teusH/MySense/docs/ssd1306.md

# Adafruit tiny display SSD1306
The Adafruit display

has SPI (7 wires) or I2C bus (4 wires) connector.
The SPI version will not cooperate with Grove Pi Shield!

## references
* https://raspberrytips.nl/oled-display-spi-raspberry-pi/
* https://media.readthedocs.org/pdf/ssd1306/stable/ssd1306.pdf

## hardware SPI installation
Wiring:
```
Raspberry Pi    color   OLED Module
5V   (PIN #1)   red     VDD (VIN)       PIN1 is V3.3
GND  (PIN #6)   black   GND
GPIO23 (PIN #16)        green   DC
GPIO24 (PIN #18)        blew    RES (RST)
MOSI (PIN #19)  purple  SDA (DATA)
SCLK (PIN #23)  orange  SCK (CLK)
CE0  (PIN #24)  yellow  CS
```
## Pi configuration
Use `ls -l /dev/spidev*`: /dev/spidev0.0  /dev/spidev0.1 to see if SPI is enabled.
If not existant enable SPI in the raspberry Pi config tool:
```shell
sudo raspi-config
```
* ‘Advanced Options' ▸ SPI ▸ YES and push Enter. 
Use `ls -l /dev/i2c-*` to see if I2C is enabled.
If not enable I2C via raspi-config.
The Pi might show I2C write errors. MySense display server will terminate if there are too many write errors. It is a known hardware bug in the Pi3 I2C driver.

## dependences installation
Use `INSTALL.sh DISPLAY` to install them or manually:
```shell
sudo apt-get install build-essential python-dev python-pip
sudo pip install RPi.GPIO

sudo apt-get install python-imaging python-smbus

sudo apt-get install git
git clone https://github.com/adafruit/Adafruit_Python_SSD1306.git
cd Adafruit_Python_SSD1306; sudo python setup.py install
```

## test hardware and software
SSD1306-test.py:
```python
import Adafruit_GPIO.SPI as SPI
import Adafruit_SSD1306

from PIL import Image
from PIL import ImageDraw
from PIL import ImageFont

disp = Adafruit_SSD1306.SSD1306_128_64(rst=24, dc=23, spi=SPI.SpiDev(0, 0, max_speed_hz=8000000))

disp.begin()
disp.clear()
disp.display()

image = Image.new('1', (disp.width, disp.height))

draw = ImageDraw.Draw(image)
draw.rectangle((0,0,disp.width-1,disp.height-1), outline=1, fill=0)

font = ImageFont.load_default()
draw.text((16, 24),'RASPBERRYTIPS.NL',  font=font, fill=255)

disp.image(image)
disp.display()
```

Voorbeeld:
import time
import sys
import subprocess

import Adafruit_GPIO.SPI as SPI
import Adafruit_SSD1306

from PIL import Image
from PIL import ImageDraw
from PIL import ImageFont

from time import sleep
```
## display service
Run `python MyDisplayServer.py start` to start the display service. The service uses localjost/2017 socket address to collect lines. Lines of text can be preceeded with the following xml:
* <clear> clear display immediatly
* <text font=FONT_NAME size=8> to get a line in some ttf font as defined in `/usr/share/fonts/truetype/` directory.
The line will scroll every 0.1 sec if the line is wider as the width of the display.
The display will scroll every 30 seconds one line if there are more lines as to be fit as the height of the display.

## test
Use MyDisplayClient.py to send a line to the service, eg.
```shell
python MyDisplayClient.py "This is first" "This is second line and is long."
```

## Use output channel
Add to `MySense.conf` the section:
```
    [display]
    output = True
```
