teusH/MySense/reports/Meetlokaties-Overzicht-2019-2026.pdf

# overzicht meetlocaties in enkele gemeenten

# onderzochte gemeentes met metingen en gebruikte sensoren 2019-2025

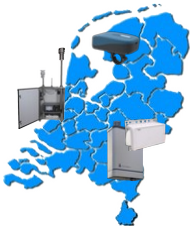
[picture p33: figure]

Teus Hagen, april 2026, MySense project.

gemeente | pagina
Amsterdam | 4
Beverwijk | 5
Gouda | 6
Haarlem | 7
Heemskerk | 8
Horst aan de Maas | 9
Hollandse Luchten | 10
Land van Cuijk | 11
Leidschendam-Voorburg | 12
Leusden | 13
Nijmegen | 14
Peel en Maas | 16
Velsen | 17
Venray | 18
Zaanstad | 19
informatie over de de metingen | 2
mogelijke conclusies en uitnodiging daartoe | 3

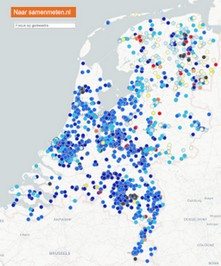
[picture p34: figure]

### - Voor een aantal gemeentes worden de low-cost meetstations van enkele gemeentes

aangegeven operationeel per jaar van 2019 t/m 2025.
- Meetstations, operationeel gehouden door diverse projecten en burger initiatieven,

### gebruikmakend van diverse fijnstof sensoren. Alleen PM2.5 metingen zijn meegenomen

in dit onderzoek.

### - De informatie is vergaard via Samen Meten Dataportaal API (april 2026) met

Samen Meten Tools. (https://github.com/teusH/MySense/blob/master/SamenMetenTools/README.md)

### - De om de interactieve kaartjes te downloaden als HTML bestand kan geclickt worden op de kaartjes bij elk overzicht. Het HTML bestand kan dan vervolgens via de browser

ingezien worden. De kaarten zijn van OpenStreetMap en Leaflet.

### - De icon’s en vlaggetjes van enkele regio’s zijn puur bedoeld als indicatie van een gemeente of regio. De gemeente vlaggetjes waaien soms alle kanten op. Wapperen bij

de één harder als bij de ander.

### - De analyse van het getoonde (spreadsheet) cijfermateriaal wordt overgelaten aan de

lezer. Er zijn meer mogelijkheden als dan hier getoond wordt.

### - Dit overview is met behulp van een spreadsheet (ODS formaat), zie

https://github.com/teusH/MySense/SamenMetenTools (https://github.com/teusH/MySense/blob/master/SamenMetenTools/SLA-cases-Overzicht-Meetpunten.ods) voor de data bron.

# overzicht meetlocaties in enkele gemeentes

# Samen Meten Dataportaal

# meetlocaties met metingen en gebruikte sensoren 2019-2025

Teus Hagen, april 2026, MySense project.

naar Samen Meten Dataportaal (https://samenmeten.rivm.nl/dataportaal/)

- Voor meer conclusies en mogelijkheden tot conclusie wordt verwezen naar de spreadsheet. (https://github.com/teusH/MySense/blob/master/SamenMetenTools/SLA-cases-Overzicht-Meetpunten.ods) Zie https://github.com/teusH/MySense/SamenMetenTools.
- De overzichten geven niet weer wat het meten heeft opgeleverd en bijgedragen aan beleidsmaatregelen.
- Maak gebruik van de interactieve browser kaartjes door downloaden van de pagina en te visualiseren in de browser.
- Ontwikkeling in kwaliteit en mogelijkheden van de fijnstof sensoren: van Shiney, naar Nova en Sensirion en recentelijk Bosch. Van WiFi naar IoT mobiel netwerk.
- Pas op er zijn groeperingen (clustering) van meetstations op minder dan 100 meter van elkaar. Ze hangen niet altijd op de meest gunstige plek.
- Er is onduidelijkheid tav de duurzaamheid van low-cost meetstations en meetprojecten en aantal metingen.
- Het aantal operationele meetstation bereikte, op maar een paar na, in 2023 het hoogtepunt.
- De uitdaging van dit document is om meer conclusies te trekken en de gegevens uit te breiden naar behoefte.
- De software is vrij te gebruiken en uit te breiden onder reciprocal licentie voorwaarden: EUPL (European Union Public Licence).
- Disclaimer: dit overzicht is met zorg samengesteld. De hoeveelheid gegevens is enorm. Verbeteringen worden op prijs gesteld.

# overzicht meetlocaties in enkele gemeentes

# Samen Meten Dataportaal

# voorzichtige conclusies en uitnodiging tot meer conclusies

Teus Hagen, april 2026, MySense project.
- Voor meer conclusies en mogelijkheden tot conclusie wordt verwezen naar de spreadsheet. (https://github.com/teusH/MySense/blob/master/SamenMetenTools/SLA-cases-Overzicht-Meetpunten.ods)

# overzicht meetlocaties Samen Meten Amsterdam

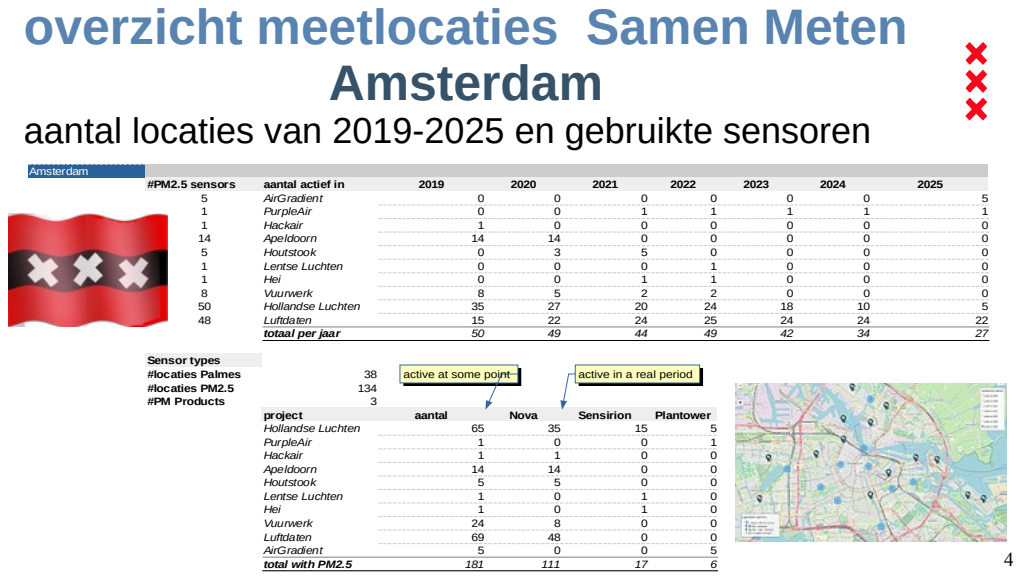
[picture p35: page 4]
Amsterdam; #PM2.5 sensors; aantal actief in; AirGradient; PurpleAir; Hackair; Apeldoorn; Houtstook; Lentse Luchten; Hei; Vuurwerk; Hollandse Luchten; Luftdaten; totaal per jaar; Sensor types; #locaties Palmes; #locaties PM2.5; #PM Products; Nova; project; aantal; Sensirion; Plantower; total with PM2.5; active at some point; active in a real period

aantal locaties van 2019-2025 en gebruikte sensoren

# overzicht meetlocaties Samen Meten Beverwijk

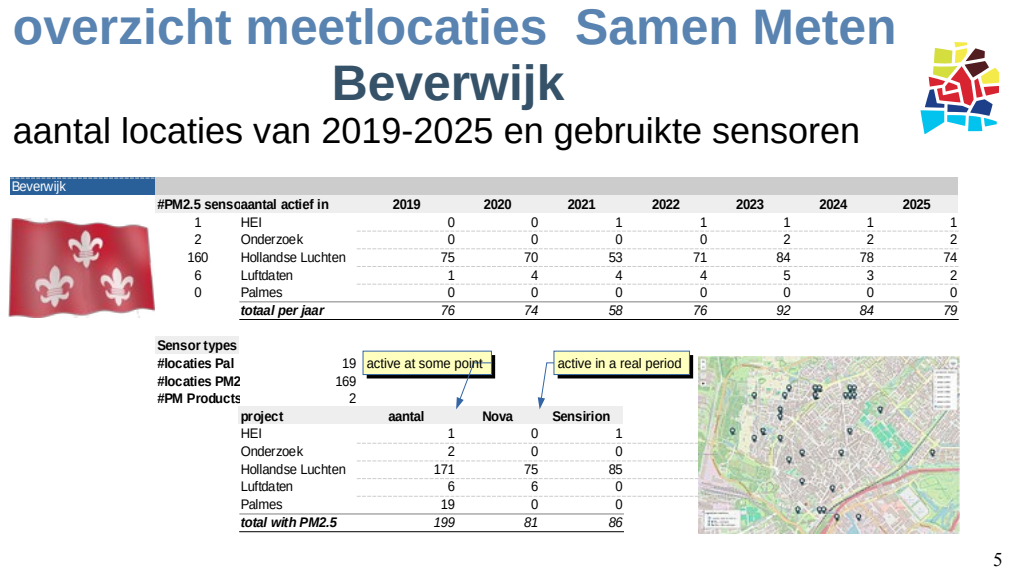
[picture p36: page 5]
Beverwijk; #PM2.5 sensoaantal actief in; HEI; Onderzoek; Hollandse Luchten; Luftdaten; Palmes; totaal per jaar; Sensor types; #locaties Pal; #locaties PM2; #PM Products; Nova; project; aantal; Sensirion; Sensirion HEI; Plantower Onderzoek; Shiney; total with PM2.5; active at some point; active in a real period

aantal locaties van 2019-2025 en gebruikte sensoren

# overzicht meetlocaties Samen Meten Gouda

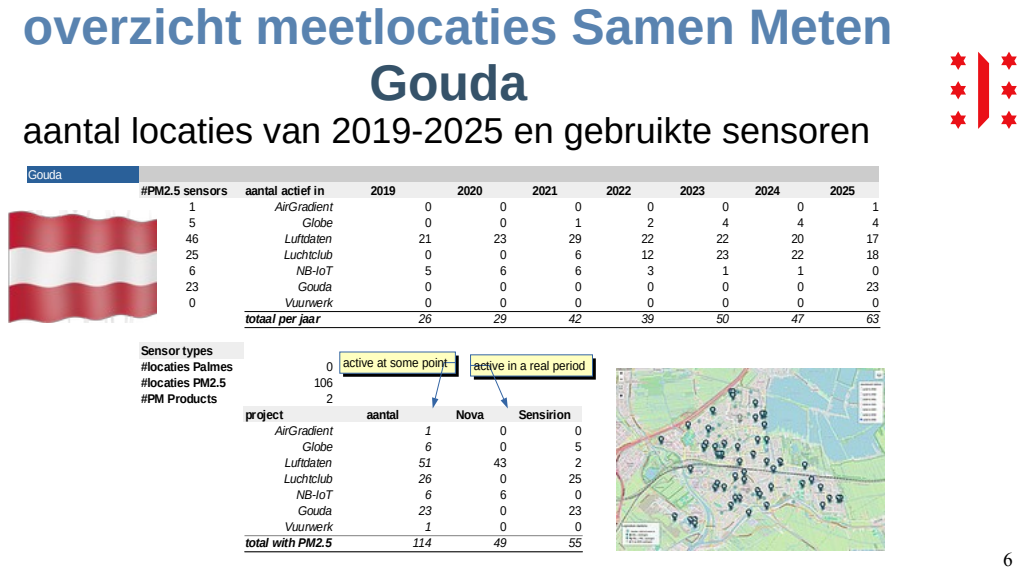
[picture p37: page 6]
Gouda; #PM2.5 sensors; aantal actief in; AirGradient; Globe; Luftdaten; Luchtclub; NB-IoT; Vuurwerk; totaal per jaar; Sensor types; #locaties Palmes; #locaties PM2.5; #PM Products; Nova; project; aantal; Sensirion; total with PM2.5; active at some point; active in a real period

aantal locaties van 2019-2025 en gebruikte sensoren

# overzicht meetlocaties Samen Meten Haarlem

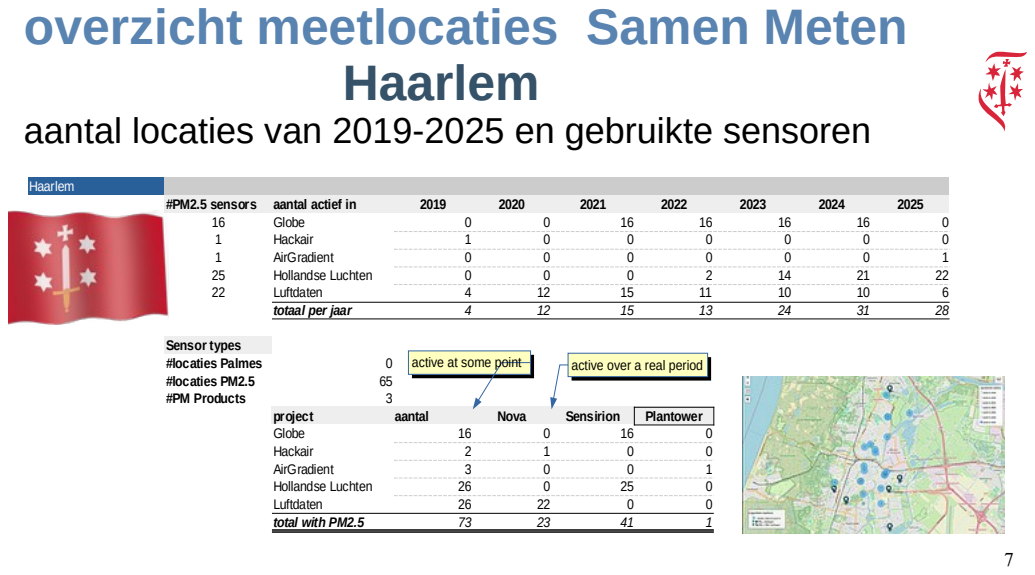
[picture p38: page 7]
Haarlem; #PM2.5 sensors aantal actief in; Globe; Hackair; AirGradient; Hollandse Luchten; Luftdaten; totaal per jaar; Sensor types; #locaties Palmes; #locaties PM2.5; #PM Products; Nova; project; aantal; Sensirion; Plantower; Shiney; total with PM2.5; active at some point; active over a real period

aantal locaties van 2019-2025 en gebruikte sensoren

# overzicht meetlocaties Samen Meten Heemskerk

# aantal locaties van 2019-2025 en gebruikte sensoren

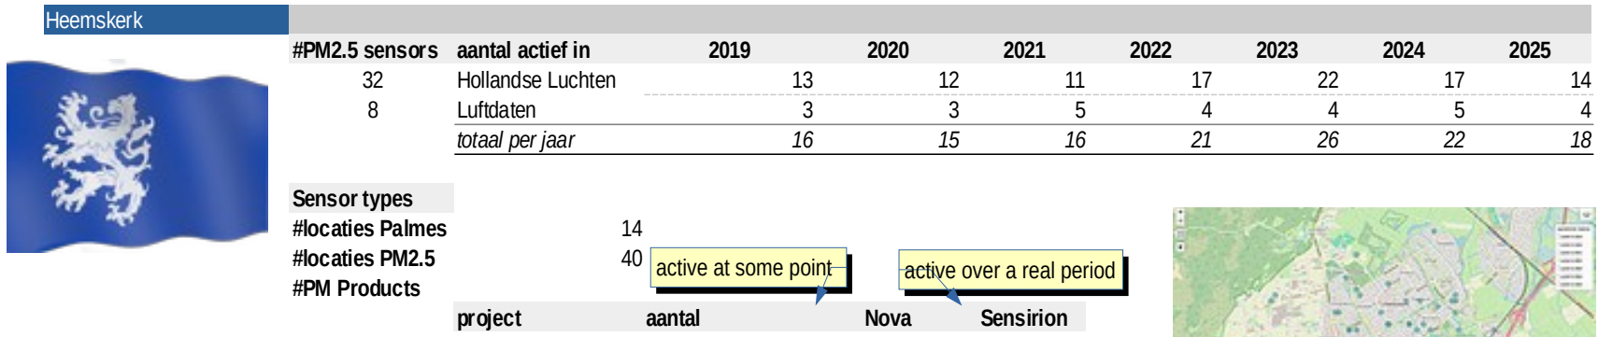
[picture p39: figure]
Heemskerk; #PM2.5 sensors aantal actief in; Hollandse Luchten; Luftdaten; totaal per jaar; Sensor types; #locaties Palmes; #locaties PM2.5; #PM Products; Nova; project; aantal; Sensirion; active at some point; active over a real period
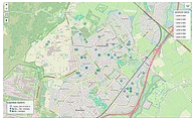
[picture p40: figure]

Sensirion | Hollandse Luchten | 32 | 13 | 19
Plantower | Luftdaten | 9 | 8 | 0
Shiney | total with PM2.5 | 41 | 21 | 19

# overzicht meetlocaties Samen Meten Horst aan de Maas

# aantal locaties van 2019-2025 en gebruikte sensoren

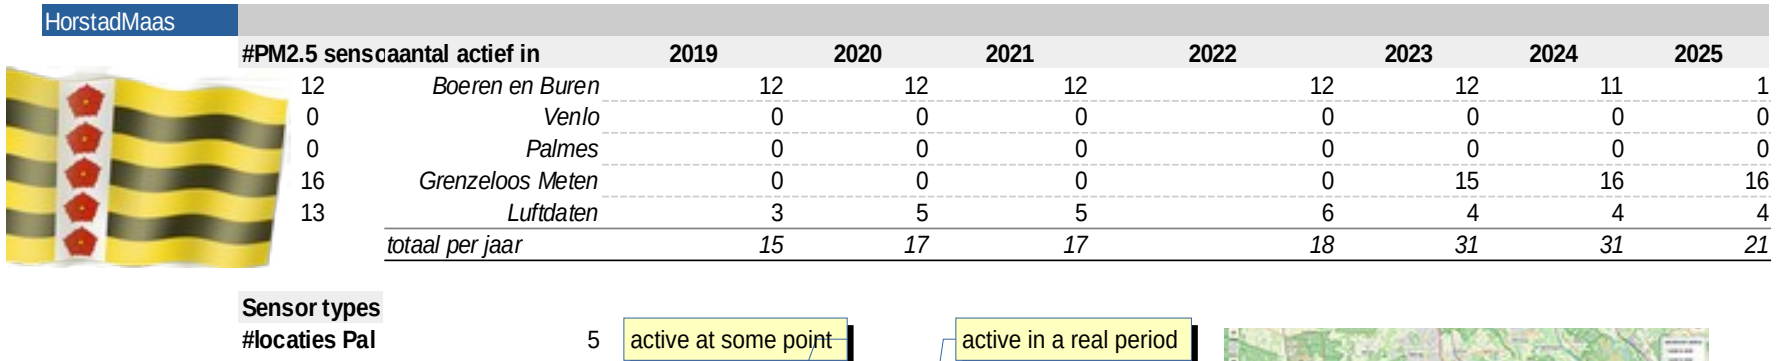
[picture p41: figure]
HorstadMaas; #PM2.5 sensoaantal actief in; Boeren en Buren; Venlo; Palmes; Grenzeloos Meten; Luftdaten; totaal per jaar; Sensor types; #locaties Pal; active at some point; active in a real period
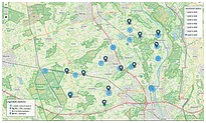
[picture p42: figure]

#locaties PM2 | 41

#PM Products | 2

Nova | project | aantal | Nova | Sensirion
Sensirion | Boeren en Buren | 12 | 12 | 0
| Venlo | 3 | 0 | 0
| Palmes | 5 | 0 | 0
| Grenzeloos Meten | 16 | 0 | 16
| Luftdaten | 19 | 13 | 0
| total with PM2.5 | 55 | 25 | 16

# overzicht meetlocaties Samen Meten Hollandse Luchten

# aantal locaties van 2019-2025 en gebruikte sensoren

Ijmond
#PM2.5 sensors | aantal actief in | 2019 | 2020 | 2021 | 2022 | 2023 | 2024 | 2025

Beverwijk | | 76 | 74 | 58 | 76 | 92 | 84 | 79
Haarlem | | 4 | 12 | 15 | 13 | 24 | 31 | 28
Heemskerk | | 16 | 15 | 16 | 21 | 26 | 22 | 18
Velsen | | 41 | 41 | 39 | 35 | 23 | 27 | 25
Amsterdam | | 50 | 49 | 44 | 49 | 42 | 34 | 27
Zaanstad | | 25 | 28 | 28 | 34 | 30 | 32 | 29
| totaal per jaar | 187 | 191 | 172 | 194 | 207 | 198 | 177

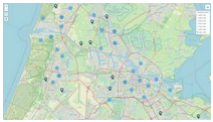
[picture p43: figure]

Sensor types | actief | Nova | Sensirion | Plantower
| Beverwijk | 81 | 86
| Haarlem | 23 | 41 | 1
| Heemskerk | 41 | 21 | 19
| Velsen | 47 | 23 | 1
| Amsterdam | 111 | 17 | 6
| Zaanstad | 1 | 31 | 33
| totaal met PM2.5 | 303 | 188 | 27

# overzicht meetlocaties Samen Meten Land van Cuijk

# aantal locaties van 2019-2025 en gebruikte sensoren

LandvCuijk
#PM2.5 sensors | aantal actief in | 2019 | 2020 | 2021 | 2022 | 2023 | 2024 | 2025

2 | AirGradient | 0 | 0 | 0 | 0 | 0 | 0 | 2
0 | Palmes | 0 | 0 | 0 | 0 | 0 | 0 | 0
1 | Hollandse Luchten | 0 | 0 | 0 | 1 | 1 | 1 | 0
89 | Luftdaten | 24 | 34 | 46 | 29 | 24 | 24 | 21
| totaal per jaar | 24 | 34 | 46 | 30 | 25 | 25 | 23

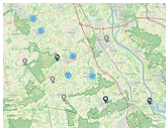
[picture p44: figure]

Sensor types
#locaties Palmes | 13

#locaties PM2.5 | 92

#PM Products | 3

Nova | project | aantal | Nova | Sensirion | Plantower
Sensirion | AirGradient | 2 | 0 | 0 | 2
Plantower | Palmes | 13 | 0 | 0 | 0
Shiney | Hollandse Luchten | 1 | 0 | 1 | 0
| Luftdaten | 97 | 87 | 1 | 1
| total with PM2.5 | 113 | 87 | 2 | 3
active at some point | active in a real period

# overzicht meetlocaties Samen Meten Leidschendam-Voorburg

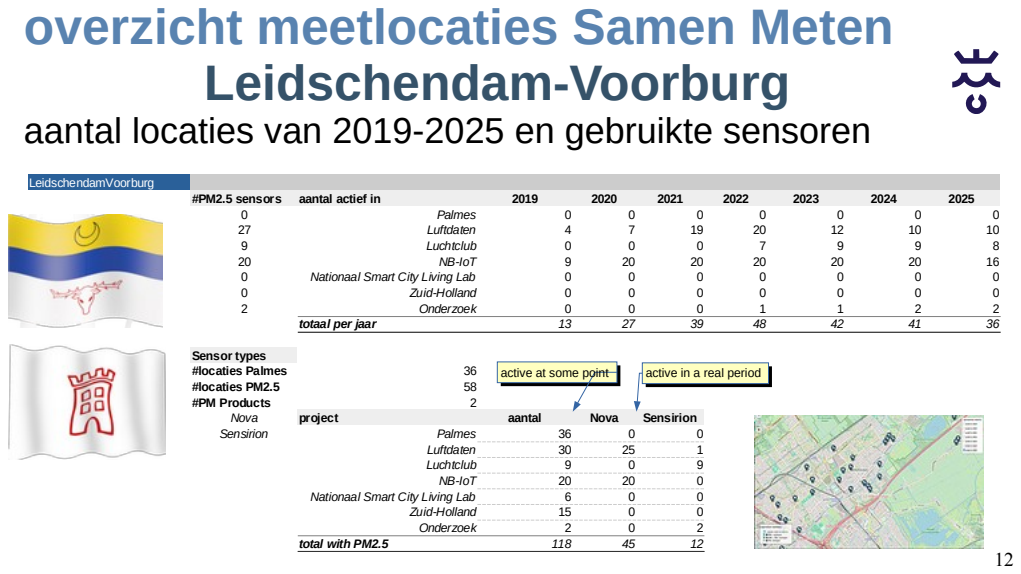
[picture p45: page 12]
LeidschendamVoorburg; #PM2.5 sensors; aantal actief in; Palmes; Luftdaten; Luchtclub; NB-IoT; Nationaal Smart City Living Lab; Zuid-Holland; Onderzoek; totaal per jaar; Sensor types; #locaties Palmes; #locaties PM2.5; #PM Products; Nova; project; aantal; Sensirion; total with PM2.5; active at some point; active in a real period

aantal locaties van 2019-2025 en gebruikte sensoren

# overzicht meetlocaties Samen Meten Leusden

# aantal locaties van 2019-2025 en gebruikte sensoren

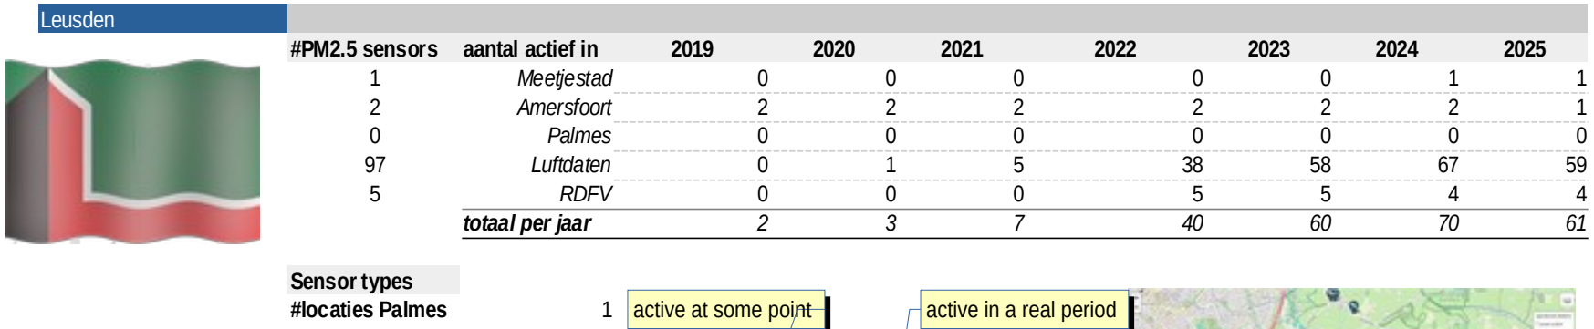
[picture p46: figure]
Leusden; #PM2.5 sensors aantal actief in; Meetjestad; Amersfoort; Palmes; Luftdaten; RDFV; totaal per jaar; Sensor types; #locaties Palmes; active at some point; active in a real period
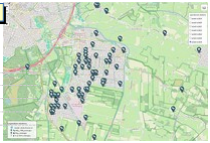
[picture p47: figure]

#locaties PM2.5 | 100

#PM Products | 2

project | aantal | Nova | Sensirion
Meetjestad | 1 | 0 | 1
Amersfoort | 2 | 2 | 0
Palmes | 1 | 0 | 0
Luftdaten | 172 | 75 | 22
RDFV | 6 | 0 | 5
total with PM2.5 | 182 | 77 | 28

# overzicht meetlocaties Samen Meten Nijmegen (1)

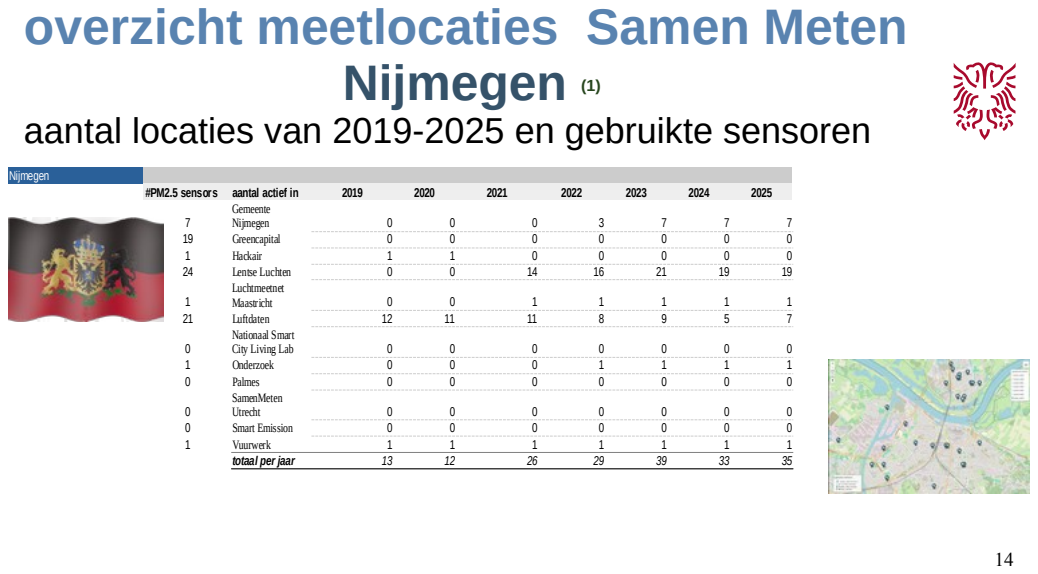
[picture p48: page 14]
Nijmegen; #PM2.5 sensors aantal actief in; Greencapital; Hackair; Lentse Luchten; Luftdaten; Onderzoek; Palmes; Smart Emission; Vuurwerk; totaal per jaar; Gemeente Nijmegen; Luchtmeetnet Maastricht; SamenMeten Utrecht

aantal locaties van 2019-2025 en gebruikte sensoren

Nationaal Smart
City Living Lab

# overzicht meetlocaties Samen Meten Nijmegen (2)

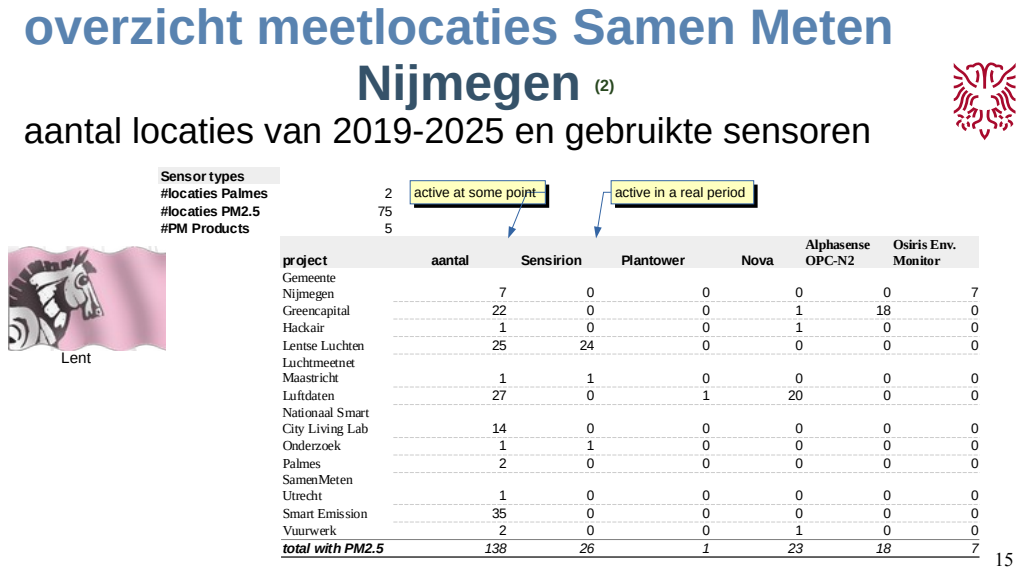
[picture p49: page 15]
Sensor types; #locaties Palmes; #locaties PM2.5; #PM Products; project; aantal; Sensirion; Plantower; Nova; Greencapital; Hackair; Lentse Luchten; Luftdaten; Onderzoek; Palmes; Smart Emission; Vuurwerk; total with PM2.5; Alphasense OPC-N2; Osiris Env. Monitor; Gemeente Nijmegen; Luchtmeetnet Maastricht; Nationaal Smart City Living Lab; SamenMeten Utrecht; active at some point; active in a real period; Lent

aantal locaties van 2019-2025 en gebruikte sensoren

# overzicht meetlocaties Samen Meten Peel en Maas

# aantal locaties van 2019-2025 en gebruikte sensoren

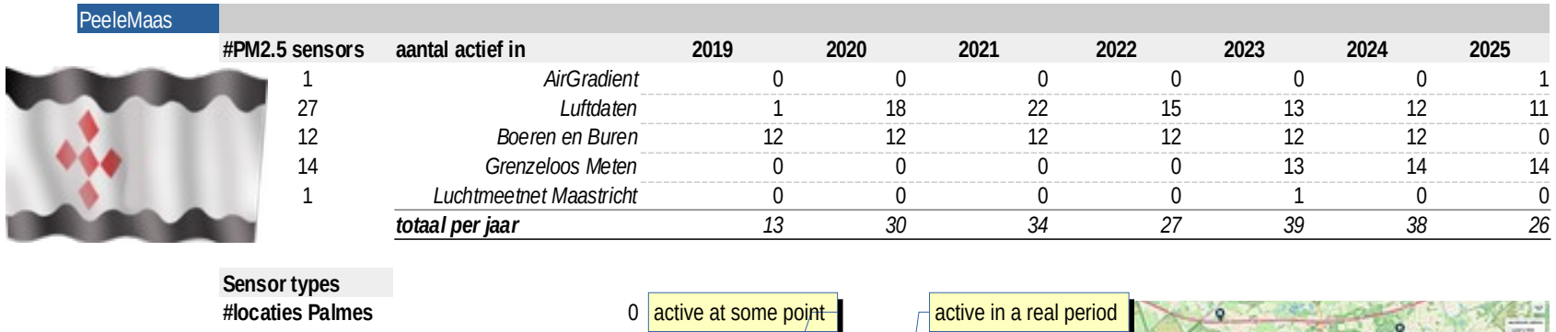
[picture p50: figure]
PeeleMaas; #PM2.5 sensors; aantal actief in; AirGradient; Luftdaten; Boeren en Buren; Grenzeloos Meten; Luchtmeetnet Maastricht; totaal per jaar; Sensor types; #locaties Palmes; active at some point; active in a real period
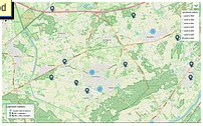
[picture p51: figure]

#locaties PM2.5 | 55

#PM Products | 2

Nova project | aantal | Nova | Sensirion
Sensirion | AirGradient | 1 | 0 | 0
Plantower | Luftdaten | 31 | 27 | 0
| Boeren en Buren | 12 | 12 | 0
| Grenzeloos Meten | 14 | 0 | 14
| Luchtmeetnet Maastricht | 1 | 0 | 1
total with PM2.5 | 59 | 39 | 15

# overzicht meetlocaties Samen Meten Velsen

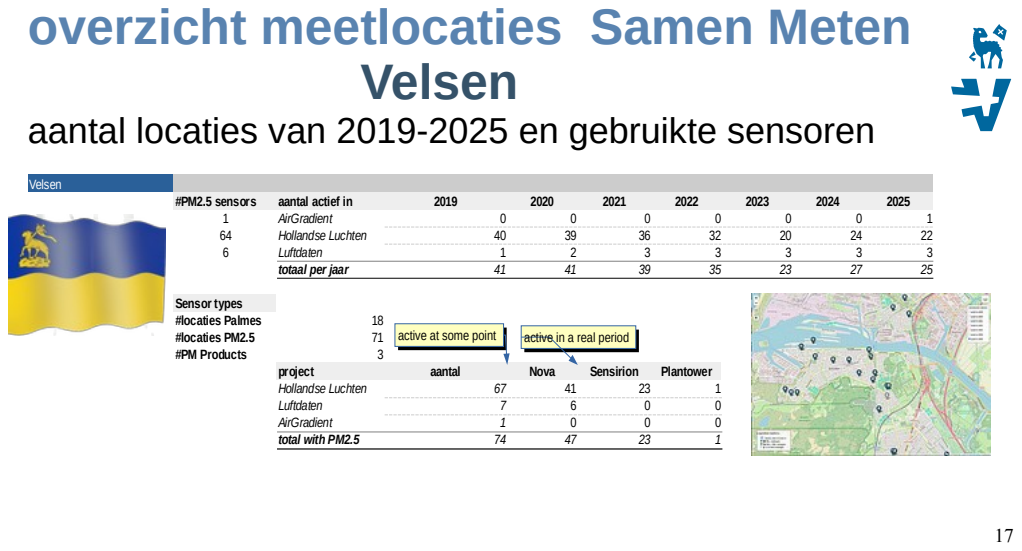
[picture p52: page 17]
Velsen; #PM2.5 sensors; aantal actief in; AirGradient; Hollandse Luchten; Luftdaten; totaal per jaar; Sensor types; #locaties Palmes; #locaties PM2.5; #PM Products; Nova; project; aantal; Sensirion; Plantower; total with PM2.5; active at some point; active in a real period

aantal locaties van 2019-2025 en gebruikte sensoren

# overzicht meetlocaties Samen Meten Venray

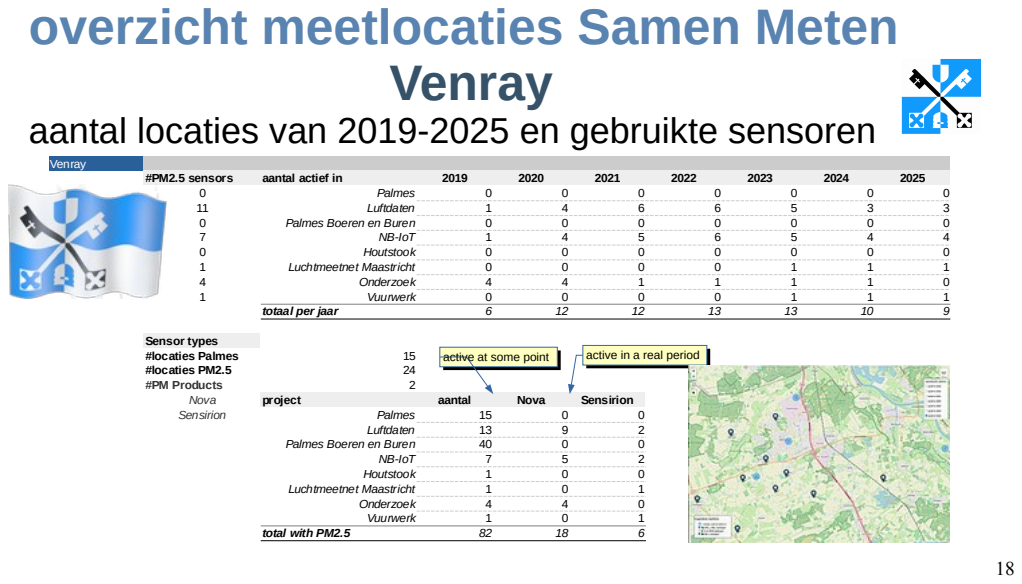
[picture p53: page 18]
Venray; #PM2.5 sensors; aantal actief in; Palmes; Luftdaten; Palmes Boeren en Buren; NB-IoT; Houtstook; Luchtmeetnet Maastricht; Onderzoek; Vuurwerk; totaal per jaar; Sensor types; #locaties Palmes; #locaties PM2.5; #PM Products; Nova; project; aantal; Sensirion; total with PM2.5; active at some point; active in a real period

aantal locaties van 2019-2025 en gebruikte sensoren

# overzicht meetlocaties Samen Meten Zaanstad

# aantal locaties van 2019-2025 en gebruikte sensoren

Zaanstad
#PM2.5 sensors aantal actief in | 2019 | 2020 | 2021 | 2022 | 2023 | 2024 | 2025

1 | AirGradient | 0 | 0 | 0 | 0 | 0 | 0 | 1
1 | Globe | 0 | 0 | 0 | 0 | 0 | 0 | 0
1 | HEI | 0 | 0 | 1 | 1 | 0 | 0 | 0
46 | Hollandse Luchten | 18 | 18 | 17 | 26 | 24 | 25 | 22
15 | Luftdaten | 7 | 10 | 10 | 7 | 5 | 6 | 5
1 | Onderzoek | 0 | 0 | 0 | 0 | 1 | 1 | 1
0 | Palmes | 0 | 0 | 0 | 0 | 0 | 0 | 0
| totaal per jaar | 25 | 28 | 28 | 34 | 30 | 32 | 29

Sensor types
#locaties Palmes | 55

#locaties PM2.5 | 65

#PM Products | 3

| project | aantal | Plantower | Sensirion | Nova
| AirGradient | 1 | 1 | 0 | 0
| Globe | 1 | 0 | 1 | 0
| HEI | 1 | 0 | 1 | 0
| Hollandse Luchten | 60 | 0 | 28 | 18
| Luftdaten | 20 | 0 | 0 | 15
| Onderzoek | 1 | 0 | 1 | 0
| Palmes | 55 | 0 | 0 | 0
| total with PM2.5 | 139 | 1 | 31 | 33
active at some point | active in a real period

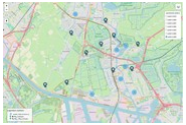
[picture p54: figure]
