teusH/MySense/reports/Scapeler Cases.pdf

## Over Scapeler

- Sensor Technologie
- Data Verzamelen, Verwerken, Analyseren, Modelleren en Visualiseren
- Maatschappelijke Waarde
- Dataportaal
- Empowerment
- Onafhankelijkheid

1

## Empowerment

Is het proces waarbij iemand gestimuleerd wordt zelfstandig te beslissen en te handelen en voor zichzelf op te komen. Dit gebeurt met methodieken die leiden tot het vergroten van het zelfvertrouwen, zelfbewustzijn en tot een positief zelfbeeld bij individuen, groepen of organisaties. Het doel van empowerment is iemand grip te laten krijgen op zijn of haar situatie en/of omgeving

2

05-04-2026

## Meetapparatuur

Drie standaard modellen:
1. ApriSensor-S:
PMSA003+DS18B20+BME280
2. ApriSensor-S-SPS30:
SPS30+DS18B20+BME680
3. ApriSensor-Duo:

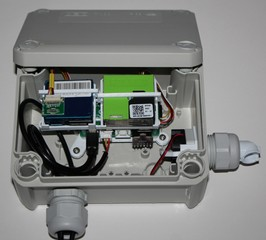
[picture p55: figure]

PMSA003+SPS30+DS18B20+BME680

3

## Wat meten we?

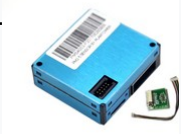
[picture p56: figure]

- Plantower PMSA003: Fijnstof PM+PN
- Sensirion SPS30: Fijnstof PM+PN
- Bosch BME280/BME680: T+RH+Pl
- Bosch BME680: T+RH+Pl (+VOC)

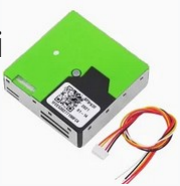
[picture p57: figure]

- Dallas DS18B20: T extern sensorkit
05-04-2026 | 4

## Dataportaal

- 135 sensor kits
- Nederland, België, Zwitserland en Japan
- Extra lagen:

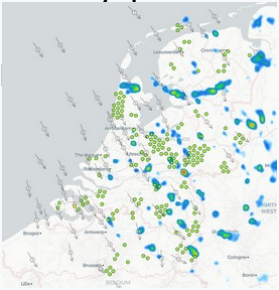
[picture p58: figure]

- Windrichting, windkracht (KNMI)
- Regen radar (KNMI)
- Luchtmeetnet
- CAMS
- Stookwijzer

5

## Case 1: Regionaal Meetnet Midden Limburg

- Meetperiode minimaal 3 jaar
- Regionaal Dataportaal
- Focus op schone lucht en gezondheid
- Houtrook

6

## Case 2: Hollandse Luchten

- HL op zoek naar alternatieve meetapparatuur
- Meetapparatuur in test opstelling
- 2x ApriSensor DUO + 2x ApriSensor-S
- Data verzamelen

7

## Case 3: Gemeente Rheden

- Sensor netwerk in gemeente Rheden
- Monitoren effect houtstookregels op luchtkwaliteit
- Meetlocaties bij burgers thuis en in openbare ruimten
- Meten in bebouwde kom en buitengebied
- Oriënterende fase met gemeente

8
