teusH/MySense/reports/SLA-Brandbrief-11mei2016.pdf

# SLA Brandbrief over de zin van:

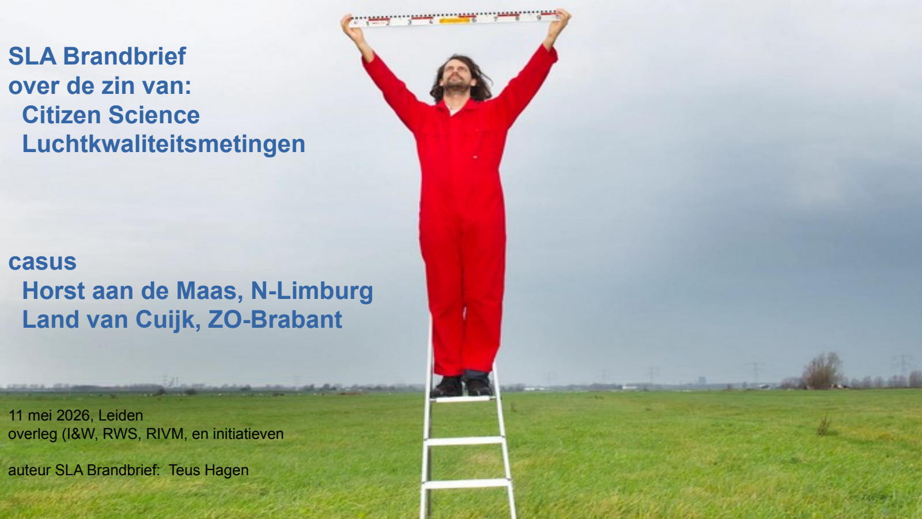
[picture p117: page 1]

# foto: Io Cooman, Volkskrant

# Citizen Science Luchtkwaliteitsmetingen

# casus Horst aan de Maas, N-Limburg Land van Cuijk, ZO-Brabant

## 11 mei 2026, Leiden overleg (I&W, RWS, RIVM, en initiatieven

## auteur SLA Brandbrief: Teus Hagen

Leiden, 11 mei 2026 - Teus Hagen | - SLA Brandbrief, casus Horst ad Maas, Land van Cuijk - | V1.1 | slide 2 van 15

# initiatief MySense

# Horst aan de Maas

⧫ | start ontwikkeling meetstations, data-com, data-analyse, website, rapportages
⧫ | 2018 start met interactieve real time overzichten, referentie metingen via LML
⧫ | doel: Terms of Reference: PM metingen rond melkvee-, varkens- en kippen-‘stallen’

⧫

# lokale beleidsvorming:

# constructieve en kwalitatieve inbreng, bewustwording, data analyse

# ⧫ 2025 einde: budgettering, demotivatie, uitblijven (lokale) dialoog met lokale overheid

# 2011 aanleg Landbouw Ontwikkelings-Gebied Grubbenvorst

referentie: CASUS Horst aan de Maas (https://github.com/teusH/MySense/blob/master/reports/202603-Casus-Horst%20aan%20de%20Maas.pdf)

Leiden, 11 mei 2026 - Teus Hagen | - SLA Brandbrief, casus Horst ad Maas, Land van Cuijk - | V1.1 | slide 3 van 15

# initiatief stichting BWLvC

# Land van Cuijk

⧫ | start lokale politiek, kosten bijdrage gem. St. Anthonis, MySense (fijnstof) meetstation, website,
| rapportages.
⧫ | 2019 start, onafhankelijke metingen, gekalibreerde metingen, verbetering meetstations
⧫ | doel: Terms of Reference: PM en NH3 metingen, meetfeiten rond emissies bronnen

⧫

# lokale beleidsvorming:

# constructieve en kwalitatieve inbreng, bewustwording, data analyse

⧫ | 2025 einde: einde budget, demotivatie, achterblijven (lokale) dialoog,
| einde gemeente St. Anthonis

# 2018 emissies bio-industrie: vleesvarkens, vlees- en legkippen

referentie: CASUS Land van Cuijk (https://github.com/teusH/MySense/blob/master/reports/202604-Casus-Land%20van%20Cuijk.pdf)

Leiden, 11 mei 2026 - Teus Hagen | - SLA Brandbrief, casus Horst ad Maas, Land van Cuijk - | V1.1 | slide 4 van 15

# wat en hoe nu gaan we nu samen verder ?

⧫ | doel luchtkwaliteitsmetingen en wat is er bereikt
⧫ | aanleiding tot schrijven van de brandbrief
⧫ | overwegingen en wederzijdse verwachtingen
⧫ | referentie materiaal (leesvoer voor thuis)

Leiden, 11 mei 2026 - Teus Hagen, Frans Kets, Walter Takens | - | Schone Lucht Akkoord Burger Participatie: het SLA glas is nu halfvol, en toen? - | V0.1 slide 5 van 15

# Citizen Science

en

# luchtkwaliteitsmetingen

# - doel:

λ

Inzicht te bieden in de luchtkwaliteit en de gezondheidseffecten daarvan, zich actief inzetten voor gezonde lucht in de gemeente, duiden en kwantificeren van effect van maatregelen door ondernemer en lokale overheid.

# - uitgangspunten:

λ | onafhankelijke, kwalitatief en goed geïnformeerde aanpak van meten en analyseren.
λ | proactieve communicatie naar en met belanghebbenden.
λ | een constructieve en op kennis gebaseerde inbreng ten opzichte van beleidskwesties in gemeente, provincie en rijk.

# - effectieve en informerende aanpak

# - bewustwording bij lokale overheid, ondernemer en burger

# - ontwikkeling van kwalitatieve low-cost meettechniek, data communicatie en opslag en data analyse

Leiden, 11 mei 2026 - Teus Hagen, Frans Kets, Walter Takens | - | Schone Lucht Akkoord Burger Participatie: het SLA glas is nu halfvol, en toen? - | V0.1 slide 6 van 15

# en ... de resultaten zijn best positief

# λ wetenschappelijk:

invloed weer en seizoen op luchtkwaliteit (wind, menglaag).
- vraagtekens: kalibratie, stabiliteit van metingen, afhankelijkheid van het weer.
- analyse software.
- ontwikkeling low-cost meettechniek, data management en data analyse.

# λ politiek:

# - bewustwording

λ | via inspreken Raad (fracties hebben het te druk).
λ | lokale nieuwsvoorzieningen

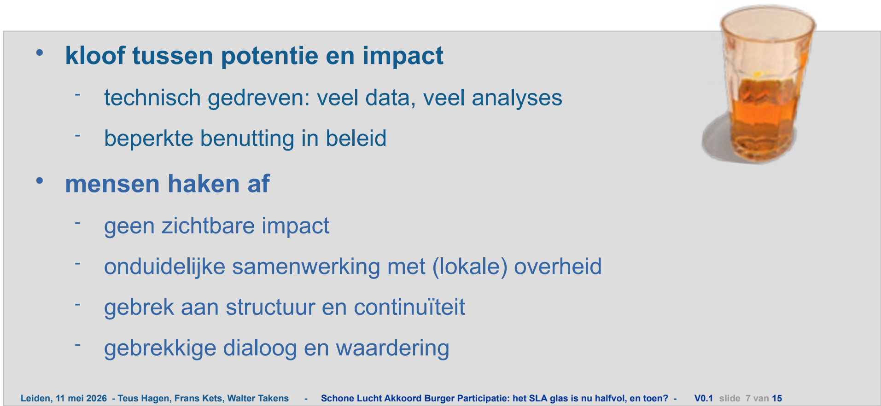
[picture p118: figure]
kloof tussen potentie en impact; - beperkte benutting in beleid; mensen haken af; - geen zichtbare impact; - gebrek aan structuur en continuïteit; - gebrekkige dialoog en waardering

Leiden, 11 mei 2026 - Teus Hagen, Frans Kets, Walter Takens | - | Schone Lucht Akkoord Burger Participatie: het SLA glas is nu halfvol, en toen? - | V0.1 slide 7 van 15
waarom? | de SLA Brandbrief

# technisch gedreven: veel data, veel analyses

# - onduidelijke samenwerking met (lokale) overheid

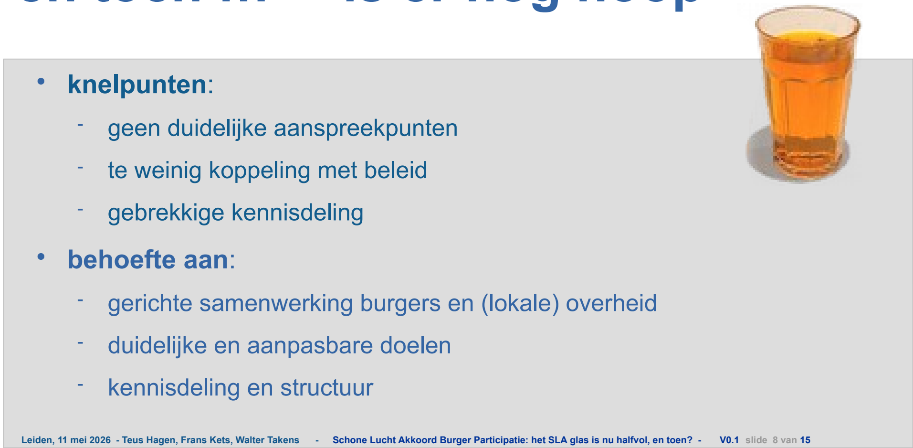
[picture p119: figure]
knelpunten:; - geen duidelijke aanspreekpunten; te weinig koppeling met beleid; - gebrekkige kennisdeling; behoefte aan:; - duidelijke en aanpasbare doelen; - kennisdeling en structuur

Leiden, 11 mei 2026 - Teus Hagen, Frans Kets, Walter Takens | - | Schone Lucht Akkoord Burger Participatie: het SLA glas is nu halfvol, en toen? - | V0.1 slide 8 van 15
en toch … | is er nog hoop

# - gerichte samenwerking burgers en (lokale) overheid

# de SLA Brandbrief

# 5 november 2025

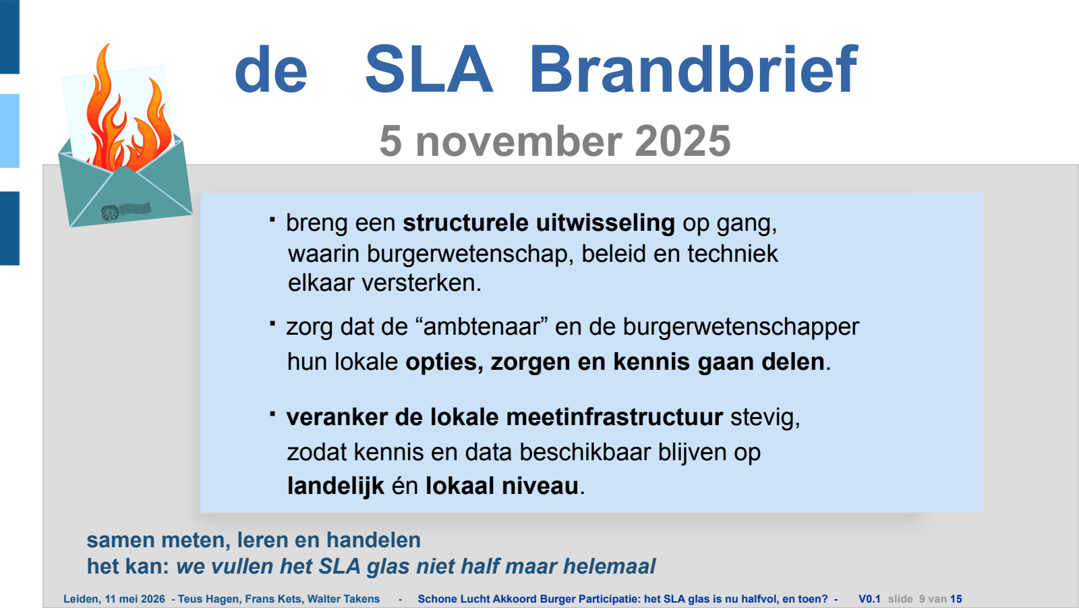
[picture p120: page 9]

Leiden, 11 mei 2026 - Teus Hagen, Frans Kets, Walter Takens | - | Schone Lucht Akkoord Burger Participatie: het SLA glas is nu halfvol, en toen? - | V0.1 slide 9 van 15
- breng een structurele uitwisseling op gang,

# waarin burgerwetenschap, beleid en techniek

elkaar versterken.

# - zorg dat de “ambtenaar” en de burgerwetenschapper

hun lokale opties, zorgen en kennis gaan delen.
- veranker de lokale meetinfrastructuur stevig,

# zodat kennis en data beschikbaar blijven op

landelijk én lokaal niveau.

# samen meten, leren en handelen het kan: we vullen het SLA glas niet half maar helemaal

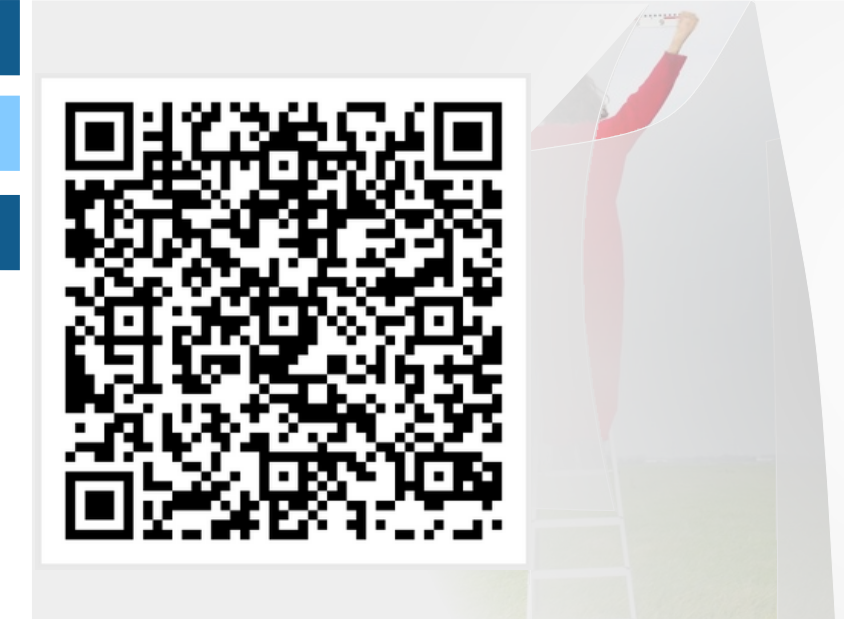
[picture p121: page 10]
Leiden, 11 mei 2026 - Teus Hagen, Frans Kets, Walter Takens; - naar photo: Io Cooman, Volkskrant; Schone Lucht Akkoord Burger Participatie: het SLA glas is nu halfvol, en toen? -; V0.1 slide 10 van 15

download:
github.com/teusH/MySense/reports/

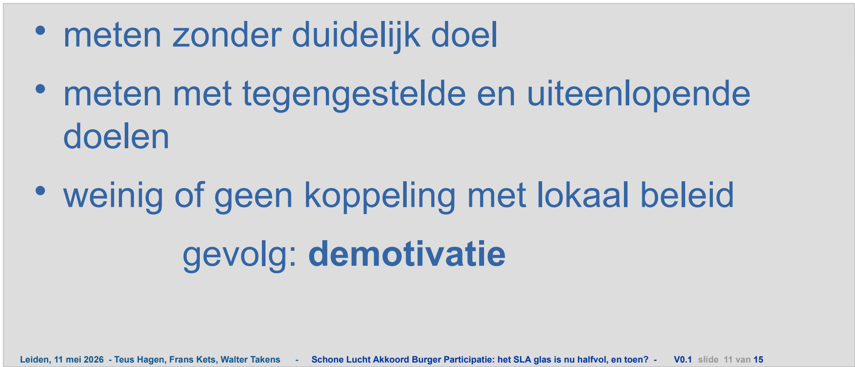
[picture p122: figure]
λ meten zonder duidelijk doel; doelen; gevolg: demotivatie

Leiden, 11 mei 2026 - Teus Hagen, Frans Kets, Walter Takens | - | Schone Lucht Akkoord Burger Participatie: het SLA glas is nu halfvol, en toen? - | V0.1 slide 11 van 15

# luchtkwaliteitsmetingen en doelgerichtheid

# λ meten met tegengestelde en uiteenlopende

# λ weinig of geen koppeling met lokaal beleid

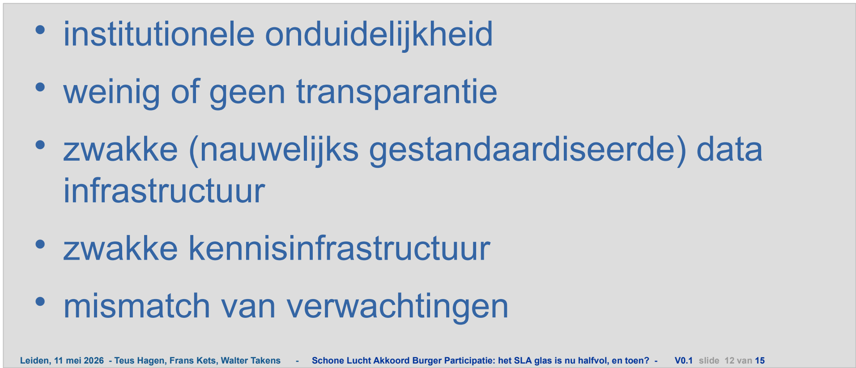
[picture p123: figure]
λ institutionele onduidelijkheid λ weinig of geen transparantie; infrastructuur λ zwakke kennisinfrastructuur λ mismatch van verwachtingen

Leiden, 11 mei 2026 - Teus Hagen, Frans Kets, Walter Takens | - | Schone Lucht Akkoord Burger Participatie: het SLA glas is nu halfvol, en toen? - | V0.1 slide 12 van 15

# de structurele problemen

# λ zwakke (nauwelijks gestandaardiseerde) data

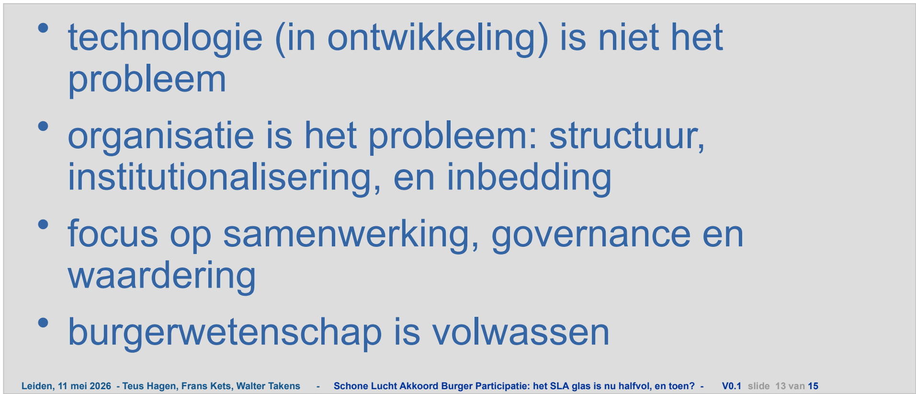
[picture p124: figure]
probleem; institutionalisering, en inbedding; focus op samenwerking, governance en waardering λ burgerwetenschap is volwassen

Leiden, 11 mei 2026 - Teus Hagen, Frans Kets, Walter Takens | - | Schone Lucht Akkoord Burger Participatie: het SLA glas is nu halfvol, en toen? - | V0.1 slide 13 van 15

# conclusie

# technologie (in ontwikkeling) is niet het

λ organisatie is het probleem: structuur,

Leiden, 11 mei 2026 - Teus Hagen, Frans Kets, Walter Takens | - | Schone Lucht Akkoord Burger Participatie: het SLA glas is nu halfvol, en toen? - | V0.1 slide 14 van 15

# leesvoer SLA Brandbrief

de vele details, een selectie | (o.a. https://github.com/teusH/MySense/)
λ | SLA Brandbrief (https://github.com/teusH/MySense/blob/master/reports/BrandBrief-SLA-V1.2.pdf) (open brief aan I&W, pdf, SLA Participatiedag 5 nov 2025)
λ | De digitale kloof overbruggen (https://waag.org/sites/waag/files/2026-03/De%20digitale%20kloof%20overbruggen.pdf) (onderzoeksrapport Waag Futurelab, pdf, maart 2026)
λ | Lokale Verbindingen (https://waag.org/sites/waag/files/2026-03/Lokale%20verbindingen.pdf) (gids voor ambtenaren, Waag Futurelab, pdf, maart 2026)
λ | SLA Participatie clarificatie document (https://github.com/teusH/MySense/blob/master/reports/ClarificatieBrandbrief260426.pdf) (achtergronds info, pdf, april 2026)
λ | Overzicht 15 gemeentes meetlokaties 2019-2025 (https://github.com/teusH/MySense/blob/master/reports/Meetlokaties-Overzicht-2019-2026.pdf) Noord- en Zuid-Holland, Brabant, Limburg (pdf, april 2026)
λ | Onderzoek 15 gemeentelijke meetlocaties en sensoren 2019-2025 (https://github.com/teusH/MySense/blob/master/reports/SLA-cases-Overzicht-Meetpunten.ods) (ODS spreadsheet, maart 2026)
λ | Cases en navelstaren:
- Casus Leidschendam-Voorburg (https://github.com/teusH/MySense/blob/master/reports/20260309-casus-Leidschendam-Voorburg.pdf) (Zuid Holland, pdf, febr 2026)
- Casus Horst ad Maas (https://github.com/teusH/MySense/blob/master/reports/202603-Casus-Horst%20aan%20de%20Maas.pdf) (Noord Limburg, pdf, maart 2026)
- Casus Land van Cuijk (https://github.com/teusH/MySense/blob/master/reports/202604-Casus-Land%20van%20Cuijk.pdf) (Zuid-Oost Brabant, pdf, maart 2026)
- Casus Scapeler (https://github.com/teusH/MySense/blob/master/reports/Scapeler%20Cases.pdf) (Houtstook metingen, pdf, april 2026)
λ Citizen Science: Citizen Sensing (https://waag.org/nl/citizen-sensing/) (Waag Futurelab webpagina, mei 2026)

Leiden, 11 mei 2026 - Teus Hagen, Frans Kets, Walter Takens | - | Schone Lucht Akkoord Burger Participatie: het SLA glas is nu halfvol, en toen? - | V0.1 slide 15 van 15

# leesvoer

de vele details, een selectie | (https://github.com/teusH/MySense/)
λ | Historisch overzicht luchtkwaliteit meten mbt lokale overheid (https://github.com/teusH/MySense/blob/master/reports/Tijdslijn%202011-2023%20luchtkwaliteitsmetingen%20Behoud%20de%20Parel%20_%20Behoud%20de%20Parel.pdf) (2011-2023,

# web pagina)

λ | 3 jaar meten in een agrarische omgeving (https://github.com/teusH/MySense/blob/master/reports/3JaarMetenInAgrRegioWatNu.pdf) (sept 2022, rapport)
λ | Luchtkwaliteit meten een leerschool (https://github.com/teusH/MySense/blob/master/reports/20230601-WAR-luchtkwaliteit-meten-leerschool-Teus-16X10-final.pdf) (juni 2023, Meetkoppel presentatie)
λ | Luchtkwaliteit meten: werkkader en organisatie structuur en ervaringen (https://github.com/teusH/MySense/blob/master/reports/Samen%20meten%20aan%20luchtkwaliteit%20_%20Behoud%20de%20Parel.pdf)

# (sept 2023, notitie)
