teusH/MySense/reports/ClarificatieBrandbrief260426.pdf

30 april 2026

## CLARIFICATIES T.A.V. SLA BRANDBRIEF

Introductie
Het gezamenlijke doel van beleid, bestuur en citizen science is een betere luchtkwaliteit in Nederland. Om dit te bereiken is een goede samenwerking noodzakelijk.
De intenties daartoe zijn er.

De brandbrief zoals gepresenteerd op de SLA Participatiedag op 5 november 2025 geeft uiting aan een aantal zorgen over de effectiviteit van deelname van burgerwetenschappers binnen het kader van het Schone Lucht Akkoord en geeft enkele knelpunten aan.
Alhoewel er zeker positieve kanten kunnen worden aangewezen, zien wij mogelijkheden tot verbetering.

Achtergrond: burgerwetenschappers zijn er in soorten en maten. Wij onderscheiden hier:
1. de innovator, geïnteresseerd in techniek en analysemethodes.
2. de milieuverbeteraar, gericht op invloed op bestuurlijke beslissingen en daarom als analist ook actief in het analyseren van metingen; Dit vertrouwt op metingen van “huisvesters”.
3. de huisvester, die het leuk vind om een metertje thuis te hebben.
4. de ondernemer, die de techniek omarmt en deze wil uitbaten.

Ruimte voor verbetering
We beschouwen de Burgerparticipatie issues zoals aangestipt in de SLA Brandbrief, hier nader:
- Er is een teruglopende interesse (bijv. minder stations, en problemen om opvolging voor lokale trekkers te vinden):
- t.a.v. de innovator: de technologie, die ten dienste staat van globale of lokale voorspellingen van luchtkwaliteit (de indicatoren PM2,5, PM10, NO2), is geëvolueerd en wordt volwassen. De innovatieve burgerwetenschapper kiest een andere uitdaging, minder in hardware ontwikkeling, meer in analyse, en soms in een ander veld.
- t.a.v. de milieuverbeteraar: er is een flinke zorg: de relatie burgerwetenschappers – bestuur / (lokale) ambtenaren:
- Burgerwetenschappers in luchtkwaliteit hebben serieuze tools en serieuze kennis verworven. Deze kunnen meer en beter worden benut dan nu het geval is.
- “Meten om alleen het meten” – zonder doel – draagt niets bij. Strakkere en doelgerichte samenwerking tussen politiek en meetgroep is nodig om projecten samen te definiëren / te effectueren.
- Het is onduidelijk hoe de overheid voor burgerinspraak is ingericht. Bijv. waar is het aanspreekpunt? Hoe effectueer je samenwerking? Hoe ga je om met het feit dat ambtenaren van baan wisselen en burgerwetenschappers er na een paar jaar mee ophouden?
- Een eerste eenvoudige stap ter verbetering: gezamenlijke SLA dag voor ambtenaren en burgerwetenschappers gericht op uitwisseling en actionele vooruitgang. Meer concrete verbeterstappen dienen partijen gezamenlijk te ontwikkelen.
- T.a.v. de huisvester:
- “Het nieuwtje is er van af”. De stekker gaat uit het stopcontact. Einde meting.
- Metingen zijn niet nuttig als een milieuverbeteraar en de overheidsinstanties (RIVM) er niets (zichtbaars) mee doen.
- Hoe lossen we dit op?
- Veranderingen van technologie – sensoren, data verwerking, analyse:
- Er is (dankzij o.a. de ondernemers”) een opmars van kant en klare sensoren.

SLA Brandbrief besprekingen april-mei 2026

30 april 2026

- Positief voor de ‘simpele’ kant van het werk van milieuverbeteraar en huisvester (er zijn data).
- Negatief voor de motivatie voor de innovator (waar is de uitdaging?) en analist (kwaliteitscontrole, publieke beschikbaarheid van meetresultaten).
- Knowledge management:
- Burgerwetenschappers zijn niet goed in het delen van methodes en verkopen van kennis. Resultaat – fragmentatie van kennis en duplicatie van werk. Kan het delen van methodes niet verder worden gestimuleerd? Hulp bieden door structuur te laten ontstaan? Uitdagingen aanbrengen?
- RIVM website en het Samen Meten Forum zijn niet voldoende voor een effectieve uitwisseling. Overheidsinstellingen kunnen zich daar ook laten zien.

Strategie vragen voor de toekomst
- Partijen: de vier klassen burgerparticipanten (al dan niet in verenigd verband), de lokale en provinciale overheden en diensten en de centrale overheid (ministerie). Met ieder zijn eigenaardigheden en eigen cultureel gedreven aanpak.
- Wat is het doel van het SLA en een SLA opvolger ten aanzien van het gebruik van burgerwetenschappers?
- Is er een beleidskader te schetsen voor de samenwerking tussen overheid en burgerwetenschap? Zo ja, voor welke type burgerwetenschapper?
- Komen de doelen van overheid en de verschillende soorten burgerwetenschappers overeen?
- Welke valkuilen en prioriteiten zijn er? Waar zitten de krenten in de pap? Hoe maken we de krenten smakelijk voor alle partijen? Het gaat om appreciatie voor de kostbare inbreng van alle partijen.

Teus Hagen, Frans Kets, Walter Takens, e.a.

SLA Brandbrief besprekingen april-mei 2026
