teusH/MySense/reports/20260309-casus-Leidschendam-Voorburg.pdf

# Navelstaren LV2 geschiedenis

# (Naar Mart de Kruif)

# λ Voorgeschiedenis λ Doel λ Middelen λ Mensen λ Resultaten λ Einde verhaal λ Wil

# Voorgeschiedenis

λ 2017

## - Aanleiding aanleg Rotterdamse Baan bij woonwijk

## λ Dec 2017

## - RIVM bijeenkomst

## - PZH stelt “paddenstoelen” beschikbaar (5 per gemeente)

## - Wij vragen om 10 (Leidschendam & Voorburg)

## λ Daarna pas (2018):

## - Organiseren distributie over gemeente

## - Maar twee in de buurt van de Rotterdamse Baan

## λ Eerste metingen:

## - Ontwikkelen van display methodes

# Doel

λ 2018 Definiëren van uitgangspunten en aanpak in Terms of Reference (één A4tje - Wie zijn wij?)

# - Doel:

λ

“door inzicht te bieden in de luchtkwaliteit en de gezondheidseffecten daarvan, zich actief inzetten voor gezonde

## lucht in de gemeente”

# - Uitgangspunten:

λ | Onafhankelijke en goed geïnformeerde aanpak van meten en analyseren
λ | Proactieve communicatie naar en met belanghebbenden
λ | Een constructieve en op kennis gebaseerde inbreng ten opzichte van beleidskwesties in gemeente, provincie en rijk

# - Detaillering van aanpak

λ |

# Middelen

λ

## “Paddenstoelen” (gesubsidieerd door PZH)

## - NO2, PM10

## λ PM2,5

## - Gesubsidieerd door PZH

## - Luftdaten kastjes

## λ Palmes buisjes

## - Gesubsidieerd door gemeente (2 projecten)

## λ Analyse

## - Getrivm.exe (zelfbouw)

## - Qlik sense Cloud (commerciëel)

## - Python: prototype en daarna opvolgende versies van ALVA

## λ Ondersteuning

## - Door RIVM

## - Door SLA; WHO en EU publicaties

# Mensen

## λ LV2

## - Kerngroep

λ | Verloop over de jaren
λ | Bèta mensen en politiek geïnteresseerden

## - Huisvesters

## λ Provincie

## - Andere groepen, coördinatie

## - Politieke steun – Jan Harm Brouwer

## λ Gemeente

## - Ambtenaar

## - Gemeenteraadsleden

## λ Rijk

## - SLA vergaderingen

## - RIVM

# Communicatie

λ | Nieuwsbrief (90 abonnees)
λ | Forum PZH

# Meetings

λ | PZH coördinatie
λ | SLA
λ | Koppelting
λ | PZH software groep
λ | gemeenteraadsvergaderingen
λ | Gesprekken met ambtenaar
λ | Gesprekken met fractie
| vertegenwoordigers gemeenteraad

# Volgen:

## λ Ontwikkelingen WHO, EU

# Positieve Resultaten

# λ Wetenschappelijk:

# Invloed weer en seizoen op luchtkwaliteit (wind, menglaag)

# - Vraagtekens kalibratie

# - Stabiliteit metingen

# - Analyse software

# λ Politiek:

# - Bewustwording

## λ Moties D66 en GL in gemeenteraad

### - D66: funding Palmesbuisjes

### - GL: aandringen op WHO; houtstook; snelheid op A12 (Utrechtse Baan), A4

# - Metingen Palmesbuisjes bij Mall of the Netherlands

λ | Maar - Budget onvoldoende voor meting over twee jaar
λ | Maar - Budget onvoldoende voor opvolgende metingen (werd later gecorrigeerd)

# Einde verhaal

λ

# Januari 2023

# “trekker” vertrekt uit LV2

# λ Maakt wat kleine dingen af

# - Blijft achter: IT-er (website ontwikkelaar); verbindingsman met huisvesters; twee meer politiek geïnteresseerden (connectie gemeentehuis)

# λ April 2023

# - Einde verhaal - Verbindingsman met huisvesters blijft actief

λ

# ondersteuning RIVM experimenten (roet meting)

λ

# Twee jaar projekt met Palmes buisjes bij gemeente

| –

# Wil

λ Continuïteit

- Gemeenteraadsverkiezingen 2022 geeft nieuwe coalitie – VVD, Gemeentebelangen, D66 (Was: Gemeentebelangen, GL, CDA)

λ Groundhog day – elke keer moeten gemeenteraadsleden worden bijgepraat

- Vervanging milieuambtenaar 2023 en in 2026
- Verloop binnen LV2 zelf

λ Resultaten

- Metingen niet merkbaar gebruikt in beslissingen
- Geen coördinatie metingen met gemeente (doelstelling vaag of onduidelijk)

λ Complexiteit

- Stabiliteit apparatuur en calibratie (onvoldoende nauwkeurig voor de gemeente)
- Commerciële apparatuur vervangt de zelfbouw (minder interessant voor CStists)
- Eigen analysesoftware telkens meer flexibel en daardoor moeilijker aan te sturen

λ Learning curve te hoog

- Veelheid van relaties die moeten worden onderhouden
λ | De getallen die bij de gemeente aanslaan komen van de officiële rapporten
λ | TIJD!

# Conclusie

- Doel | Te ambitieus?
- Middelen | OK, steeds beter
- Mensen | Veel relaties tov kerngroep
- Wil | Te weinig resultaat voor de moeite Steeds complexere omgeving
