teusH/MySense/reports/OverzichtMetingen BWLvC2019-2020.pdf

# drie jaar luchtkwaliteit meten

# in landelijk gebied

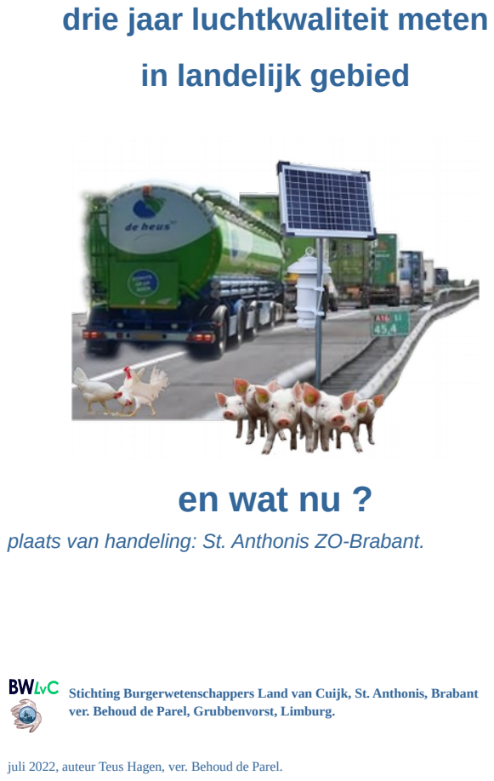
[picture p138: page 1]

en wat nu ?

plaats van handeling: St. Anthonis ZO-Brabant.

Stichting Burgerwetenschappers Land van Cuijk, St. Anthonis, Brabant
ver. Behoud de Parel, Grubbenvorst, Limburg.

juli 2022, auteur Teus Hagen, ver. Behoud de Parel.

## Voorwoord

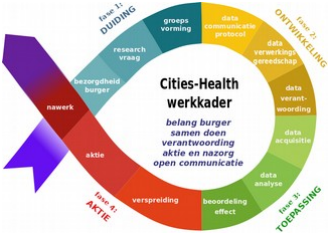
[picture p139: figure]

## Samenvatting

## Luchtkwaliteitsmetingen Land van Cuijk

Stichting Burgerwetenschappers Land van Cuijk is naar aanleiding van zorgen over de luchtkwaliteit ivm Intensieve Veeteelt ondernemingen in de (toenmalige) gemeente St Anthonis opgericht in 2019 om met name real time fijnstof en meteo metingen in de regio te doen. Dit naar aanleiding dat de gemeente Raad hiervoor een onkostenbijdrage aan de stichting Burgerwetenschappers hiervoor beschikbaar stelde en een open data communicatie LoRaWan netwerk liet aanleggen.

bron: citieshealth.eu

Ondersteund door de ver. Behoud de Parel in Grubbenvorst worden elk uur de metingen van een twintigtal meetpunten in St. Anthonis op http://behouddeparel.nl/ (http://behouddeparel.nl/meetkits/86) meetkits/86 (http://behouddeparel.nl/meetkits/86) real time weergegeven en in een overzichtssituatie per straat op http://behouddeparel.nl/?q=Regionaal Overzicht 86 beschikbaar gesteld. Hierdoor is door interactief door de tijd heen te lopen de verschillen tussen de

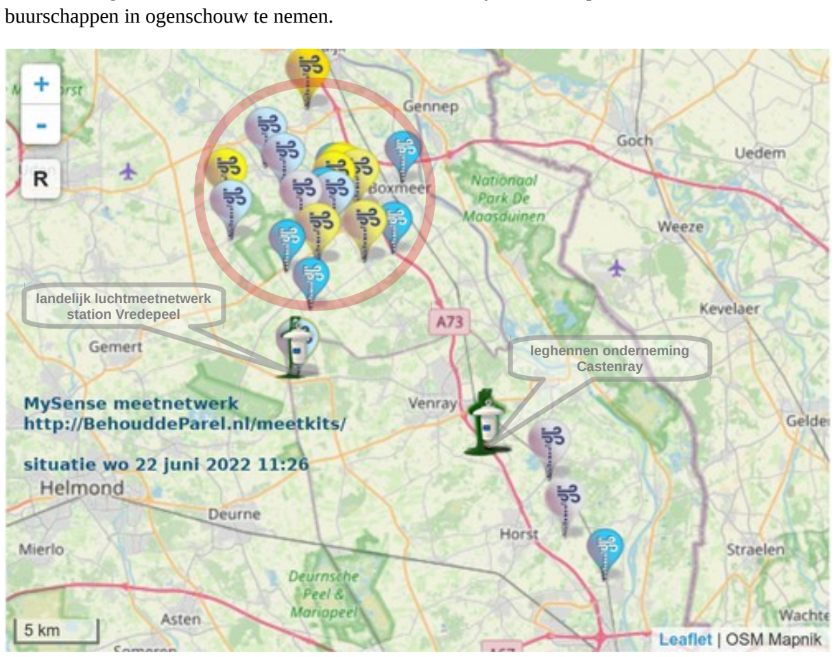
[picture p140: figure]
buurschappen in ogenschouw te nemen.; landelijk luchtmeetnetwerk station Vredepeel; leghennen onderneming Castenray

Op sommige locatie is er duidelijk sprake van meer of minder fijnstof. Externe invloeden zoals regen, luchtvochtigheid, temperatuur, windsnelheid (lagere concentraties) spelen een duidelijke rol. De fijnstof metingen zijn voor een deel ook in te zien bij RIVM (https://samenmeten.rivm.nl) en Sensors.Community (https://deutschland.maps.sensor.community/#11/51.6174/5.9566).
De markers op het kaartje geven een berekende gradatie (RIVM LKI index: (https://www.luchtmeetnet.nl/informatie/luchtkwaliteit/luchtkwaliteitsindex-(lki)) goed 0 t/m 10) van lucht kwaliteit aan. De kleur van de marker loopt van goed (donker blauw) via grijs, oranje (matig) op via rood (slecht) naar paars. Een marker in de vorm van een lantaarntje geeft aan dat de meetkit uitstaat. De LKI index is een Nederlandse weergave van RIVM om met een simpel getal mbv PM10, (PM2.5,) stikstofoxide en ozon de luchtkwaliteit weer te geven. Niet alle indicatoren behoeven gemeten te zijn.
In het afgelopen jaar heeft de stichting ook ammoniak en stikstofoxide metingen gedaan met behulp van zg gasbuisjes. Gedurende een jaar zijn op een achttal locaties zijn hiertoe maandelijks gasbuisjes geplaatst. De aflezing van de gas concentraties gebeurt door Bureau Blauw. De meetresultaten moeten nog door het RIVM beschikbaar gesteld worden. Helaas zijn deze metingen niet compleet over het gehele jaar. Van de stikstofoxide gasbuisjes zijn maar 60% van de laboratorium uitslagen bekend. Gemiste metingen zijn lineair geëxtrapoleerd.

Enkele opmerkingen tav de fijnstof metingen
- inzicht alleen als je over een langere periode kijkt
- PM2.5 fractie is indicator
- gaat om lokale verhoging of verlaging van fijnstof blootstelling tov achtergrondsnivos
- fijnstof nivo wordt gemeten door het tellen van deeltjes in groottes. De referentie metingen zijn in gewichten. Omrekenen van tellingen naar gewichten geeft fouten door omgevings-aktoren zoals bijv rel. vochtigheid. Maw correcties zijn noodzakelijk en zijn lokaal afhankelijk.
- ammoniak wordt boven de 300m omgezet naar bijv secundair fijnstof PM2.5).
- bij meten in buitenlucht heb je te maken met meten van lage concentraties.
- niet overal is energie uit stopcontact aanwezig: toepassen van zonne-energie is bij fijnstof metingen complex.
- een betrouwbaar communicatie voor meetdata is fundamenteel. Niet overal is internet betrouwbaar aanwezig.
- continue meten over lange periodes om kwalitatieve conclusies te trekken is noodzakelijk: het gaat dag en nacht door.
- het gaat om lokale blootstelling niet om interregionale modelberekeningen
- meetconclusies moeten ergens toe leiden: bijv lokaal beleid en adequate gezondheidsadvisering
- metingen zijn ongeschikt voor milieu handhaving
windsnelheden zijn in de regio laag. Maw verdunning vind niet gauw plaats.

Voorzichtige conclusies van metingen verricht over periode 2019-2021
- PM2.5 nivo’s neemt de laatste jaren niet af. De verwachting was een afname.
- PM10 nivo’s zijn ook bij de landelijke metingen nogal wisselvallig
- De fijnstof groottes (profiel) verschil nogal per type intensieve veeteelt onderneming: kippen (hogere PM10), varkens (hogere PM2.5, PM1)
- secundait fijnstof (PM2.5 afkomstig van ammoniak en stikstof) bij varkenshouderij is hoog
- lokaties waar doorlopend fijnstof nivo hoger is als het lokale gemiddelde
- lokaties waar in perioden hogere nivo’s zijn.
- lokaties met hoog percentage tov achtergronds nivo’s
-…

Fijnstof
Fijnstof (Particular Matter of PM) zijn vaste microscoop kleine vaste deeltjes van 10 micrometer en kleiner. Hoe kleiner hoe meer risicovol tav de gezondheid: bijv astma tot zelfs hartfalen. De oorsprong is zowel vanuit de natuur (meestal door natuurlijke oorsprong) als door toedoen van menselijk handelen (meestal de kleinere deeltjes).
Van oudsher wordt fijnstof gemeten in gewichten. Het tellen van deeltjes mbv laser technologie is goedkoper. Ook omdat de operationele kosten bij geavanceerde ‘deeltjes tellers’ goedkoper zijn en omdat er meerdere steekproeven mogelijk zijn zal op den duur de deeltjes tellingen gemeengoed worden. Een bijkomende voordeel is dat de verdeling naar grootte (fijnstof profiel) een beter inzicht geeft in de oorzaak van de emissies en dus de beleidsmaatregelen tot verlaging van de imissies.
De verschillende soorten fijnstof:
- De meest gebruikte benaming is naar grootte: PM10 (kleiner als 10 micrometer), PM2.5 (kleiner als 2.5 micrometer), t/m PM0.1 (ultra fijnstof).
- Naar oorzaak:
primair fijnstof (het resultaat van verbranding, wrijving, of verdamping) en secundair fijnstof (moleculen van verzurende stoffen). Secundaire fijnstof kan zich hechten aan primair fijnstof.
Condenseerbaar fijnstof bestaat uit deeltjes die zich in de lucht vormen door afkoeling van verbrandingsgassen, bijv door houtstook ofwel sfeerverwarming. Recent wordt condenseerbaar fijnstof pas meegerekend.
Stikstof

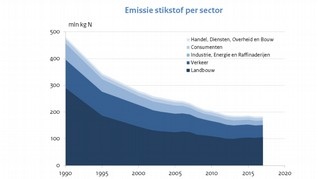
[picture p141: figure]

Stikstof is op zichzelf niet schadelijk voor de mens. Sommige stikstofverbindingen brengen echter wel schade toe aan onze gezondheid en aan de natuur. De uitstoot moet daarom omlaag. Voorbeelden van stikstof emissies zijn: ammoniak en fijnstof (ca 41% van stikstof emissies uit veeteelt en melkhouderij). Nederland is de hoogste in de EU. Bron: NPOkennis.nl

EU blootstellingsnormen en WHO advieswaarden
De EU normen (tientallen jaren geleden vastgesteld) en WHO adviesnivo’s van 2021 zijn gebaseerd op gewicht per kubieke meter.
De huidige EU normen (grenswaarden uit 2008), de WHO advieswaarden uit 2005 en de huidige WHO advieswaarden uit 2021 voor de jaargemiddelde concentratie NO2 en fijnstof PM10 en PM2,5. De normen definiëren grenswaarden mede gebaseerd op aantal dagen en daggemiddelden. Om de verschillen weer te geven is onderstaande tabel wat vereenvoudigde.
stof | EU normen
| 2008 | WHO advieswaarde
| | 2005 | WHO advieswaarde
| | | 2021
NO2 | 40 µg/m³ | 40 µg/m³ | 10 µg/m³
PM10 | 40 µg/m³ | 20 µg/m³ | 15 µg/m³
PM2,5 | 25 µg/m³ | 10 µg/m³ | 5 µg/m³

De laatste jaren zijn fijnstof sensoren beschikbaar gekomen die de fijnstofdeeltjes tellen (deeltjes tellers). Bij de weergave van de metingen worden de tellingen omgerekend naar gewichten. Nadeel is dat hierdoor correcties moeten gedaan worden nav allerlei invloeden zoals bijv rel. vochtigheid en lokatie afhankelijkheid. Een referentie meting bijv. door metingen van Lanbdelijk Meetnetwerk Luchtkwaliteit (LML) meetstation is hiervoor noodzakelijk. De nivo’s zijn (politiek) gekozen en vastgesteld op basis van wetenschappelijk onderzoek aan de hand van ‘aanvaarde’ gezondheidsrisico’s en blootstelling (inademing) van de stoffen over een periode van een jaar. Schone Lucht Akkoord (SLA)
Het doel van het Schone Lucht Akkoord is om de luchtkwaliteit in Nederland te verbeteren. Het is een akkoord tussen Rijk, 12 provincies en momenteel 90 gemeenten. Samen streven
de deelnemende partijen naar een gezondheidswinst van minimaal 50 procent in 2030 ten opzichte van 2016. Ondanks dat duidelijk is geworden ( Brief aan Tweede Kamer van ju (https://www.schoneluchtakkoord.nl/actueel/nieuws-schone-lucht-akkoord/algemeen/rivm-onderzoek-who-advieswaarden-tweede-kamer/) l (https://www.schoneluchtakkoord.nl/actueel/nieuws-schone-lucht-akkoord/algemeen/rivm-onderzoek-who-advieswaarden-tweede-kamer/) i 2022) (https://www.schoneluchtakkoord.nl/actueel/nieuws-schone-lucht-akkoord/algemeen/rivm-onderzoek-who-advieswaarden-tweede-kamer/) dat de WHO advieswaarden van 2021 niet in 2030 gehaald zullen worden is het streven wel om die waarden te halen (bron: RIVM rapport aan de Tweede Kamer).
De eerste uitvoeringsagenda en rapportage (https://www.rivm.nl/lucht/sla) van mei 2022 geeft duidelijk aan dat dan wel alle zeilen ook bij de gemeentes bijgezet moet worden. Nederland staat ook dan nog steeds aan de top van de EU landen tav emissies (fijnstof, stikstof, ammoniak en ozon). SLA deelnemers kunnen cofinanciering krijgen voor projecten via de Specifieke Uitkering Schone Lucht Akkoord (SpUkSLA) (https://www.schoneluchtakkoord.nl/schone-lucht-akkoord/producten/) van totaal 10M Euro. Het is een 50% subsidie regeling. Aan te vragen voor 1 oktober 2022!
Het RIVM berekende gezondheidseffect (korter leven) in 2016 en in 2030 bij het al vastgestelde luchtbeleid (KEV) en met aanvullende maatregelen waaronder de SLA maatregelen van provincies en gemeenten (VES), bijv voor Land van Cuijk (bron: https://www.rivm.nl/lucht/sla):

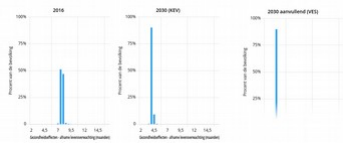
[picture p142: figure]

Geordende lijst van locaties op maandag 11 juli 2022 van locaties gemeente Land van Cuijk met een hogere meetwaarden hebben als het gemiddelde in deze regio. Top 10 met waarden hoger als het gemiddelde fijnstof PM2.5:

1.Boompjesweg Landhorst (http://behouddeparel.nl/SAN?q=content/landhorst-boompjesweg)
2.Noordkant-3 St Anthonis (http://behouddeparel.nl/SAN?q=content/st-anthonis-noordkant-3)
3.Zandkant St Anthonis (http://behouddeparel.nl/SAN?q=content/st-anthonis-zandkant)
4.Noordkant-2 St Anthonis (http://behouddeparel.nl/SAN?q=content/st-anthonis-noordkant-2)
5.Cerespark Stevensbeek (http://behouddeparel.nl/SAN?q=content/stevensbeek-cerespark)
6.Spekklef Oploo (http://behouddeparel.nl/SAN?q=content/oploo-spekklef)
7.Willem-Alexanderlaan Haps (http://behouddeparel.nl/SAN?q=content/haps-willem-alexanderlaan) 8.Noordkant-1 St Anthonis (http://behouddeparel.nl/SAN?q=content/st-anthonis-noordkant-1)
9.Bosweg St Anthonis (http://behouddeparel.nl/SAN?q=content/st-anthonis-bosweg)
10.Vloetweg Oploo (http://behouddeparel.nl/SAN?q=content/oploo-vloetweg)

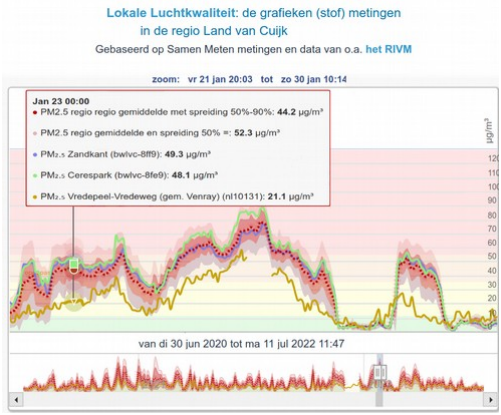
[picture p143: figure]
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
