teusH/MySense/docs/images/DC1100.png

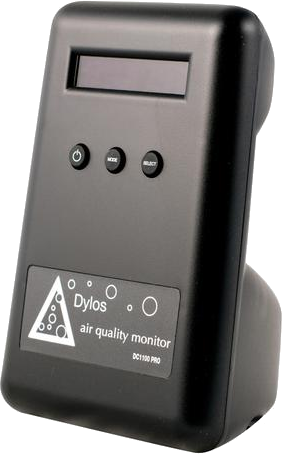
docs/images/DC1100.png
