teusH/MySense/PyCom/images/dubbelwandige-LantaarnType-MySense-3.png

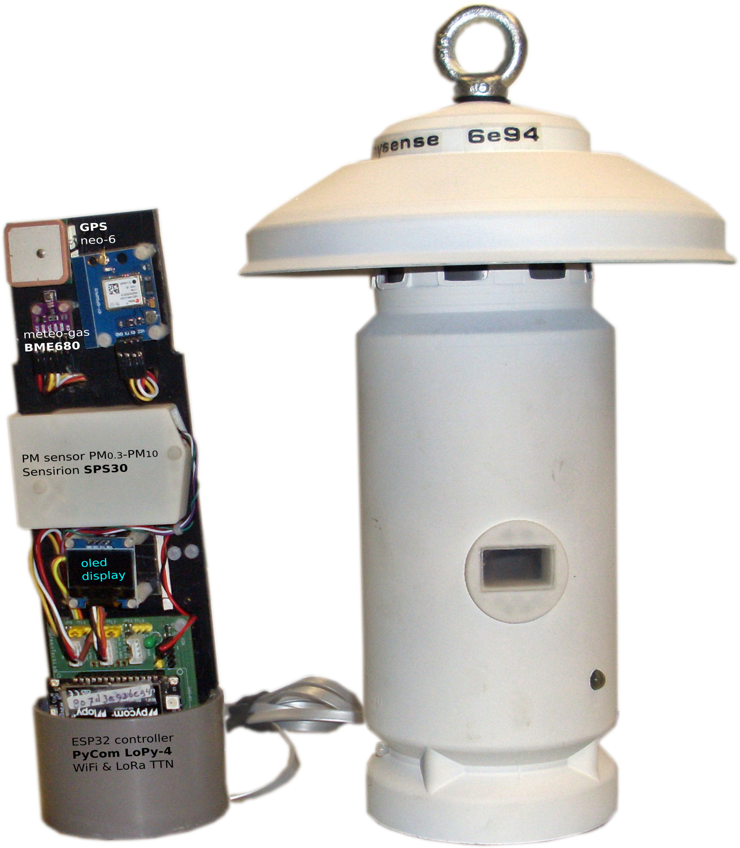
PyCom/images/dubbelwandige-LantaarnType-MySense-3.png
