teusH/MySense/PyCom/images/pwsave1.jpg

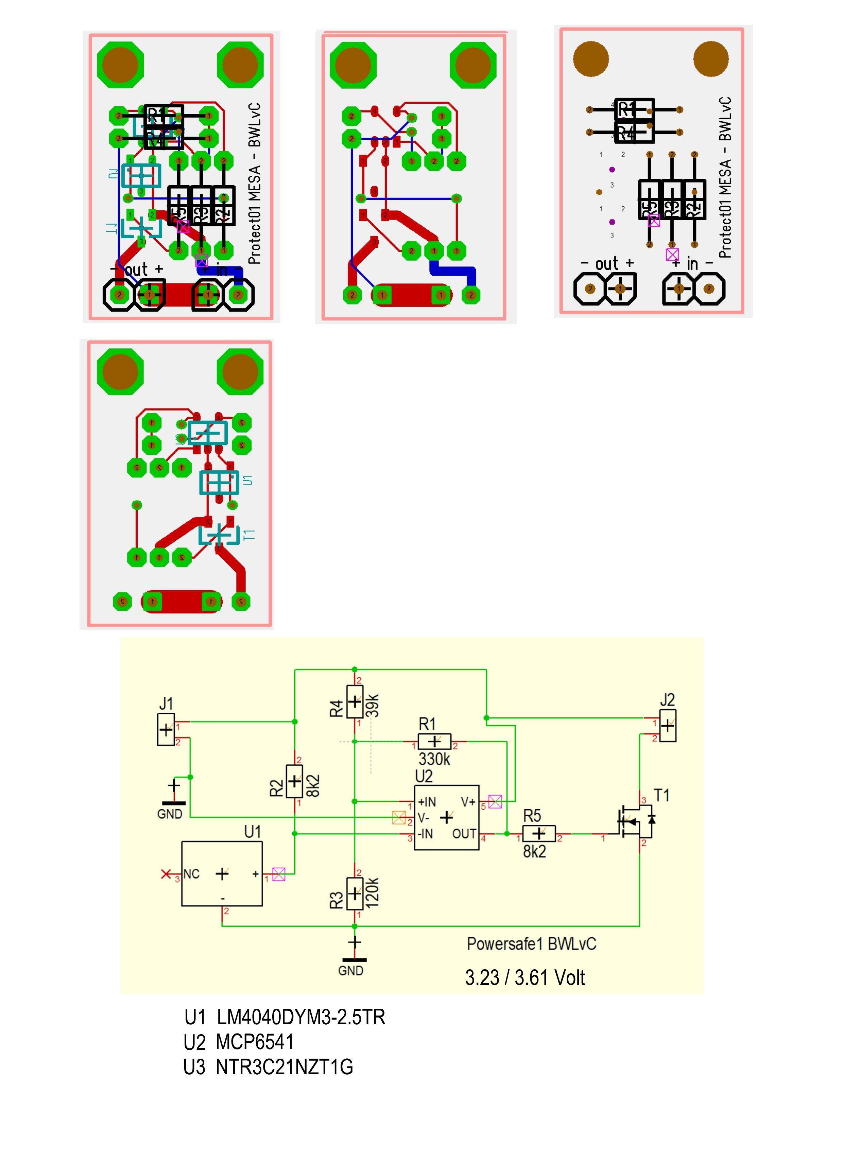
PyCom/images/pwsave1.jpg
