teusH/MySense/RPi/images/MySense1.png

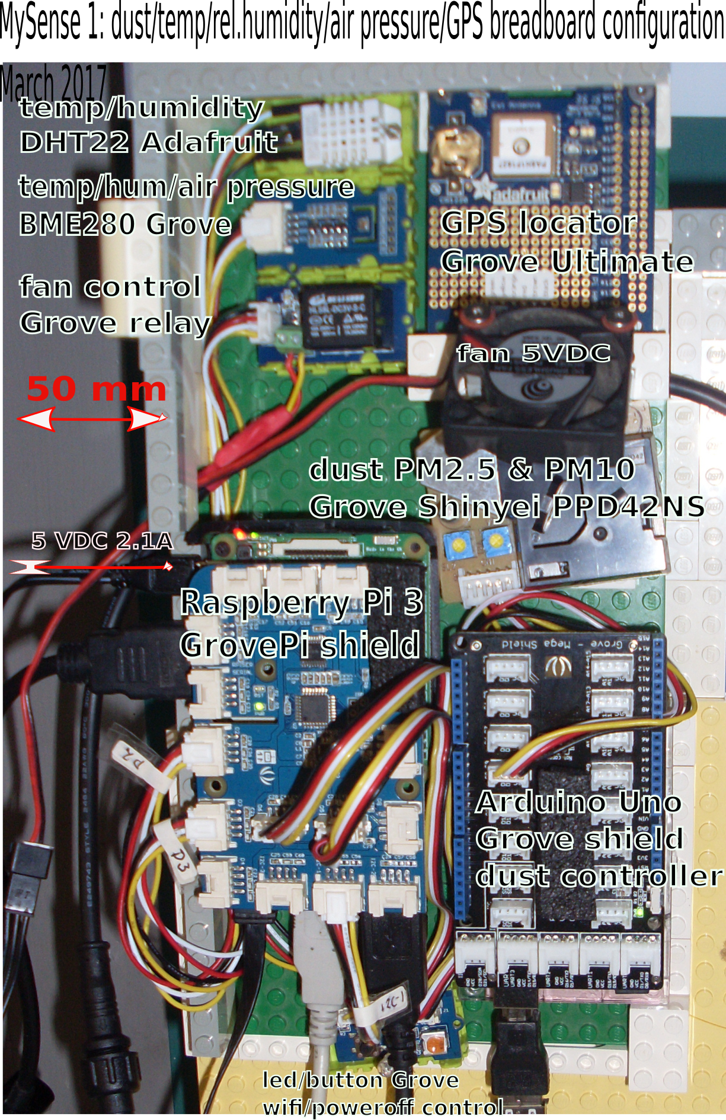
RPi/images/MySense1.png
