teusH/MySense/RPi/images/MySense-kit-1.png

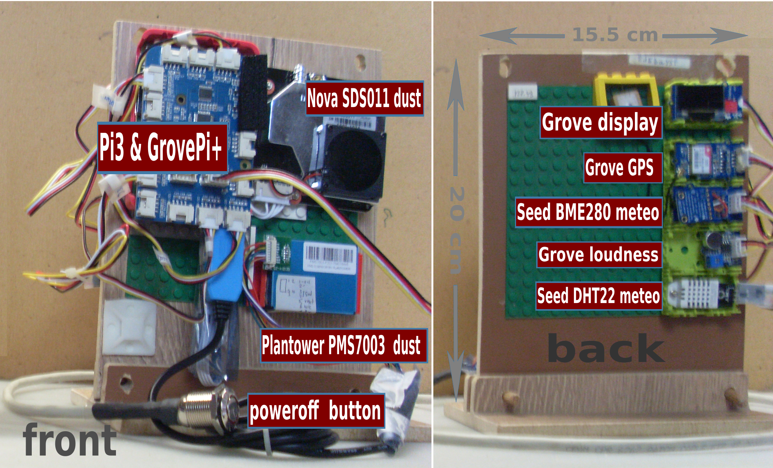
RPi/images/MySense-kit-1.png
