teusH/MySense/RPi/images/MySense-kit-2.png

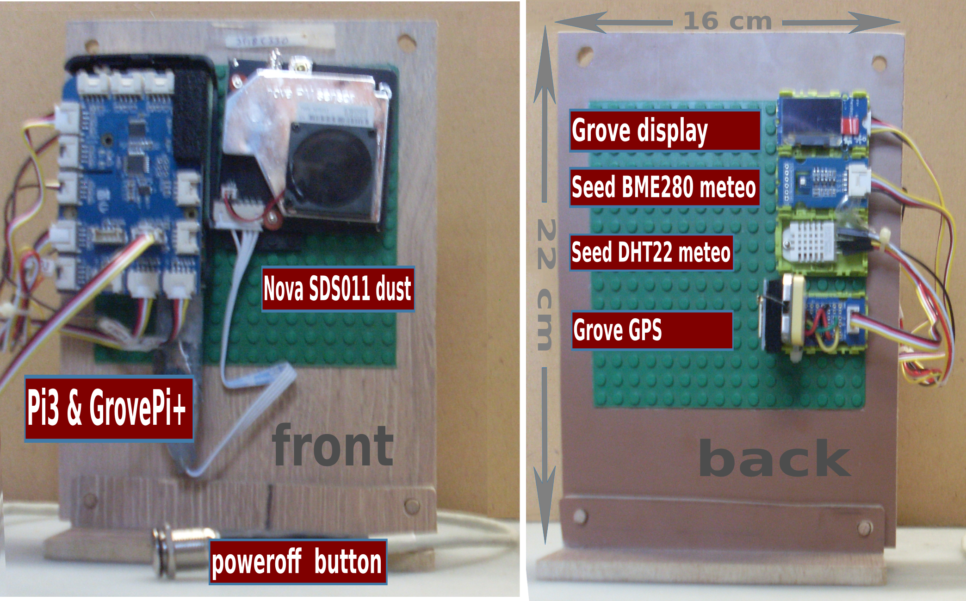
RPi/images/MySense-kit-2.png
