teusH/MySense/RPi/images/MySenseCase-Pi.png

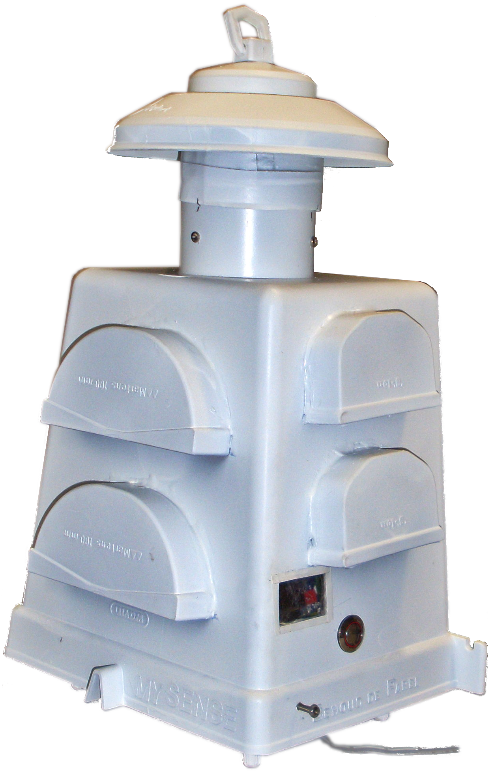
RPi/images/MySenseCase-Pi.png
