teusH/MySense/RPi/images/NH3-IBC-ADC.png

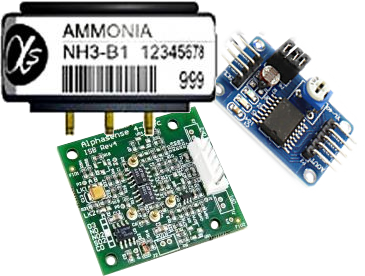
RPi/images/NH3-IBC-ADC.png
