teusH/MySense/RPi/images/Sensor-2-kast+sensors.png

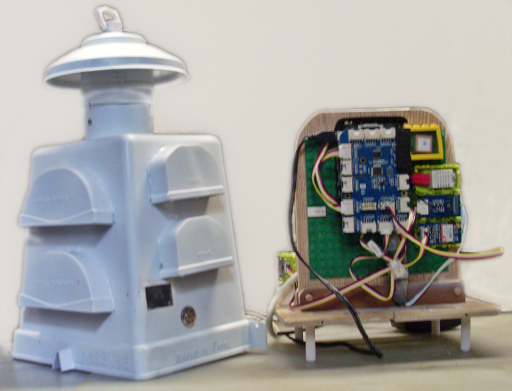
RPi/images/Sensor-2-kast+sensors.png
