teusH/MySense/RPi/images/VW_13033927-PPD42NS_ESP8266-wifi-sensor.png

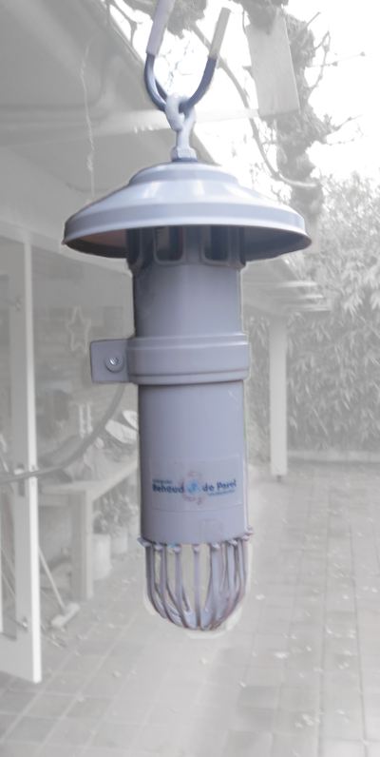
RPi/images/VW_13033927-PPD42NS_ESP8266-wifi-sensor.png
