teusH/MySense/reports/Overview sensorkits HW costs.pdf

# Table of costs and bills (the shopping list)

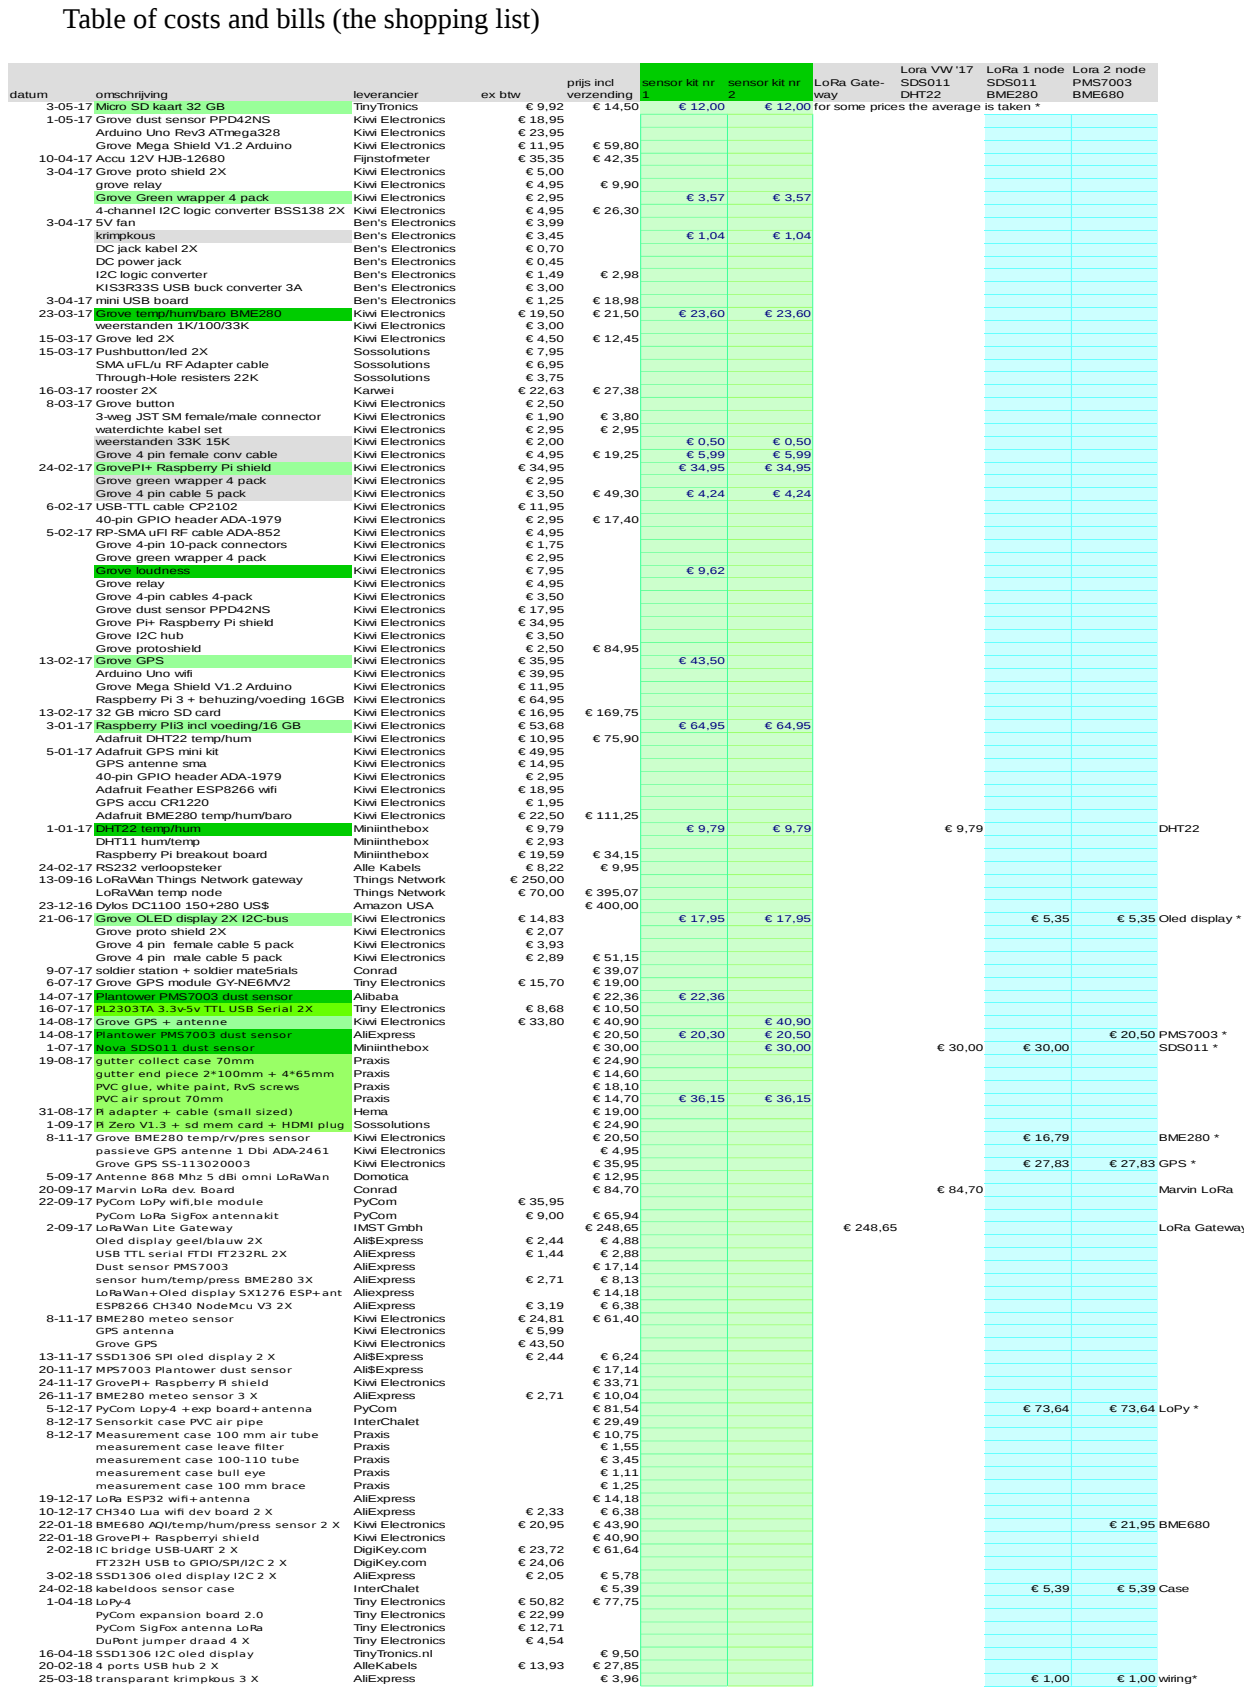
[picture p189: page 1]
datum; omschrijving; leverancier; ex btw; 3-05-17 Micro SD kaart 32 GB; TinyTronics; € 12,00 for some prices the average is taken *; 1-05-17 Grove dust sensor PPD42NS; Kiwi Electronics; Arduino Uno Rev3 ATmega328; Grove Mega Shield V1.2 Arduino; 10-04-17 Accu 12V HJB-12680; Fijnstofmeter; 3-04-17 Grove proto shield 2X; grove relay; Grove Green wrapper 4 pack; 4-channel I2C logic converter BSS138 2X Kiwi Electronics; 3-04-17 5V fan; Ben's Electronics; krimpkous; DC jack kabel 2X; DC power jack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

sensor kit nr
