teusH/MySense/PyCom/images/LoPy-PCB-V1-wiring.pdf

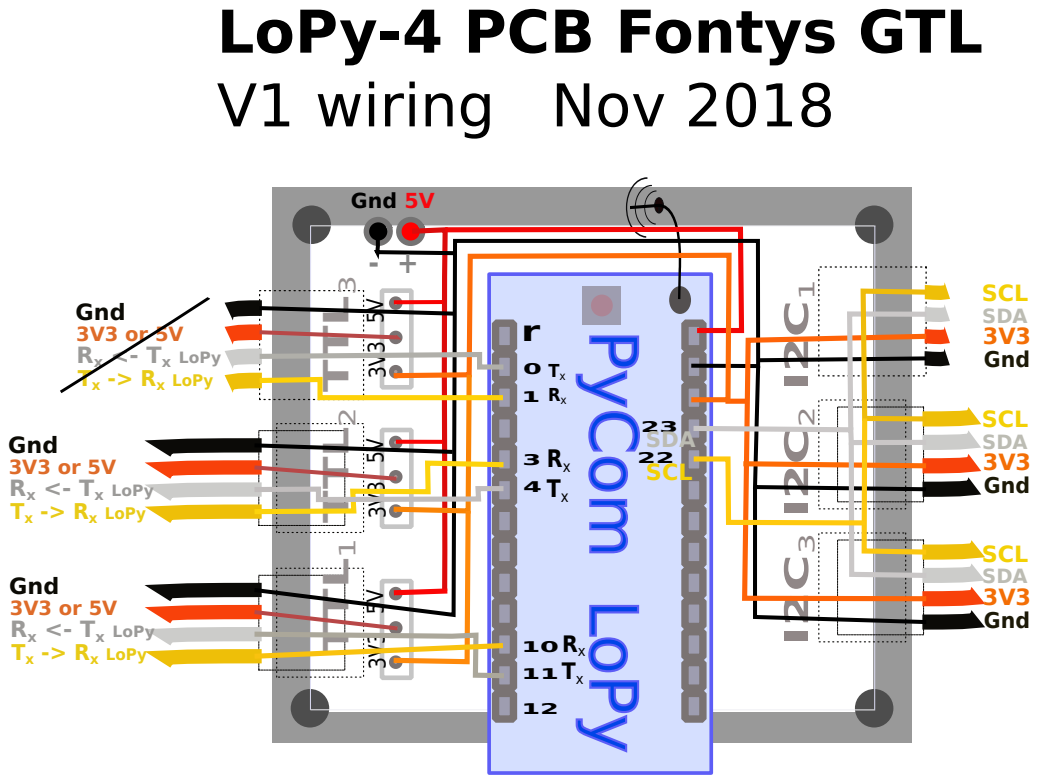
[picture p190: page 1]
V1 wiring Nov 2018 TTL¹ TTL² TTL³ 3V3 5V 3V3 5V 3V3 5V; 23 22SCL; SDA; SCL; 3V3 Gnd; Gnd 5V

LoPy-4 PCB Fontys GTL

Gnd
Rx <- Tx LoPy
Tx -> Rx LoPy
