teusH/MySense/PyCom/images/MySense-LoRa-layout-lantern.pdf

# fan

# Nova

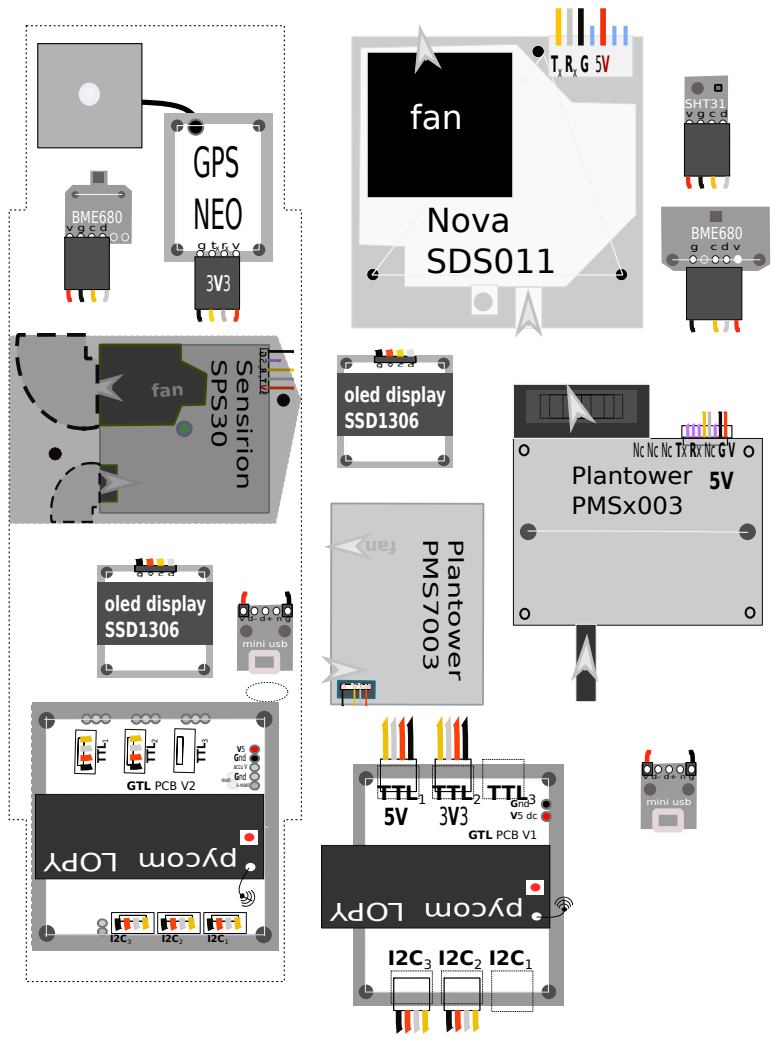
[picture p191: page 1]
PMS7003; Plantower; Gnd V5 dc; TTL1 TTL2 TTL3 5V 3V3; GTL PCB V1; SDS011; SHT31 v g c d; BME680; oled display SSD1306; BME680 v g c d; SPS30; Sensirion; fan; TTL1; TTL2; TTL3; GTL PCB V2; Gnd; Gnd s-reset reset; accu V; GPS NEO; mini usb

Plantower
PMSx003
