teusH/MySense/PyCom/lopy-191228_PCB.pdf

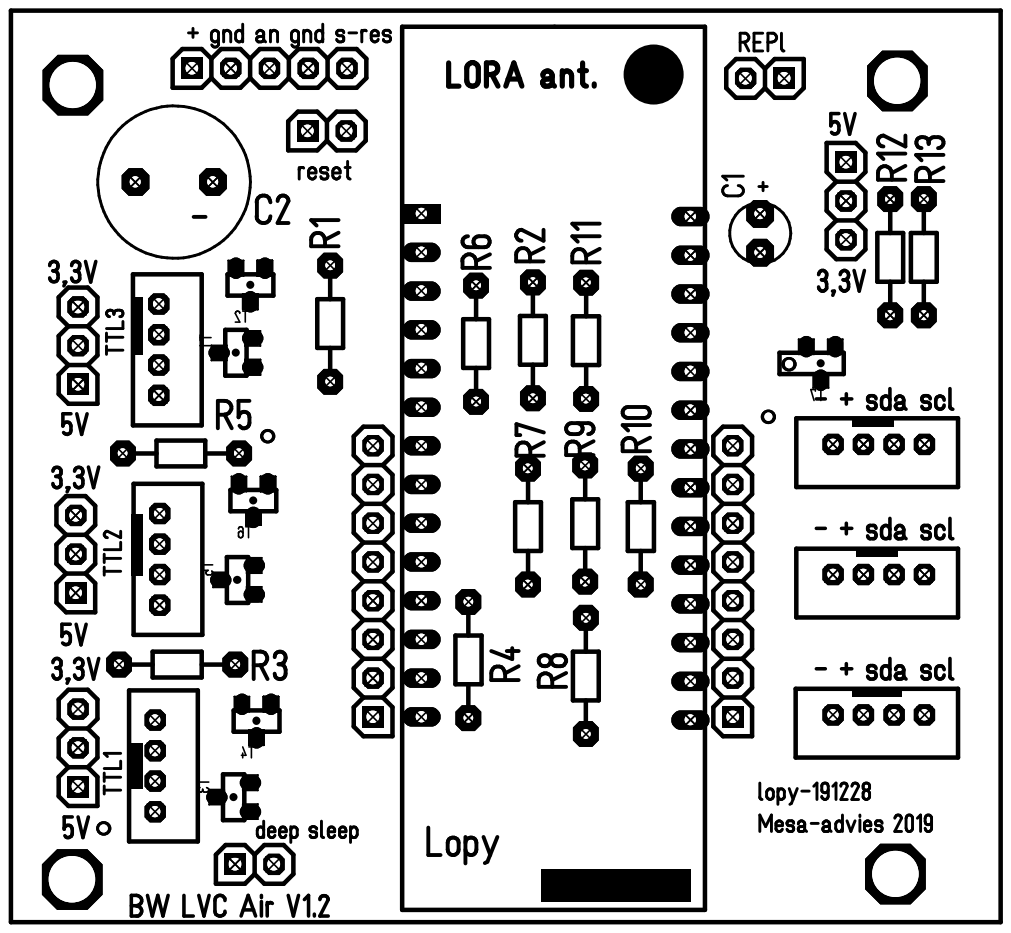
[picture p192: page 1]
