teusH/MySense/PyCom/lopy-191228_SCH.pdf

J9

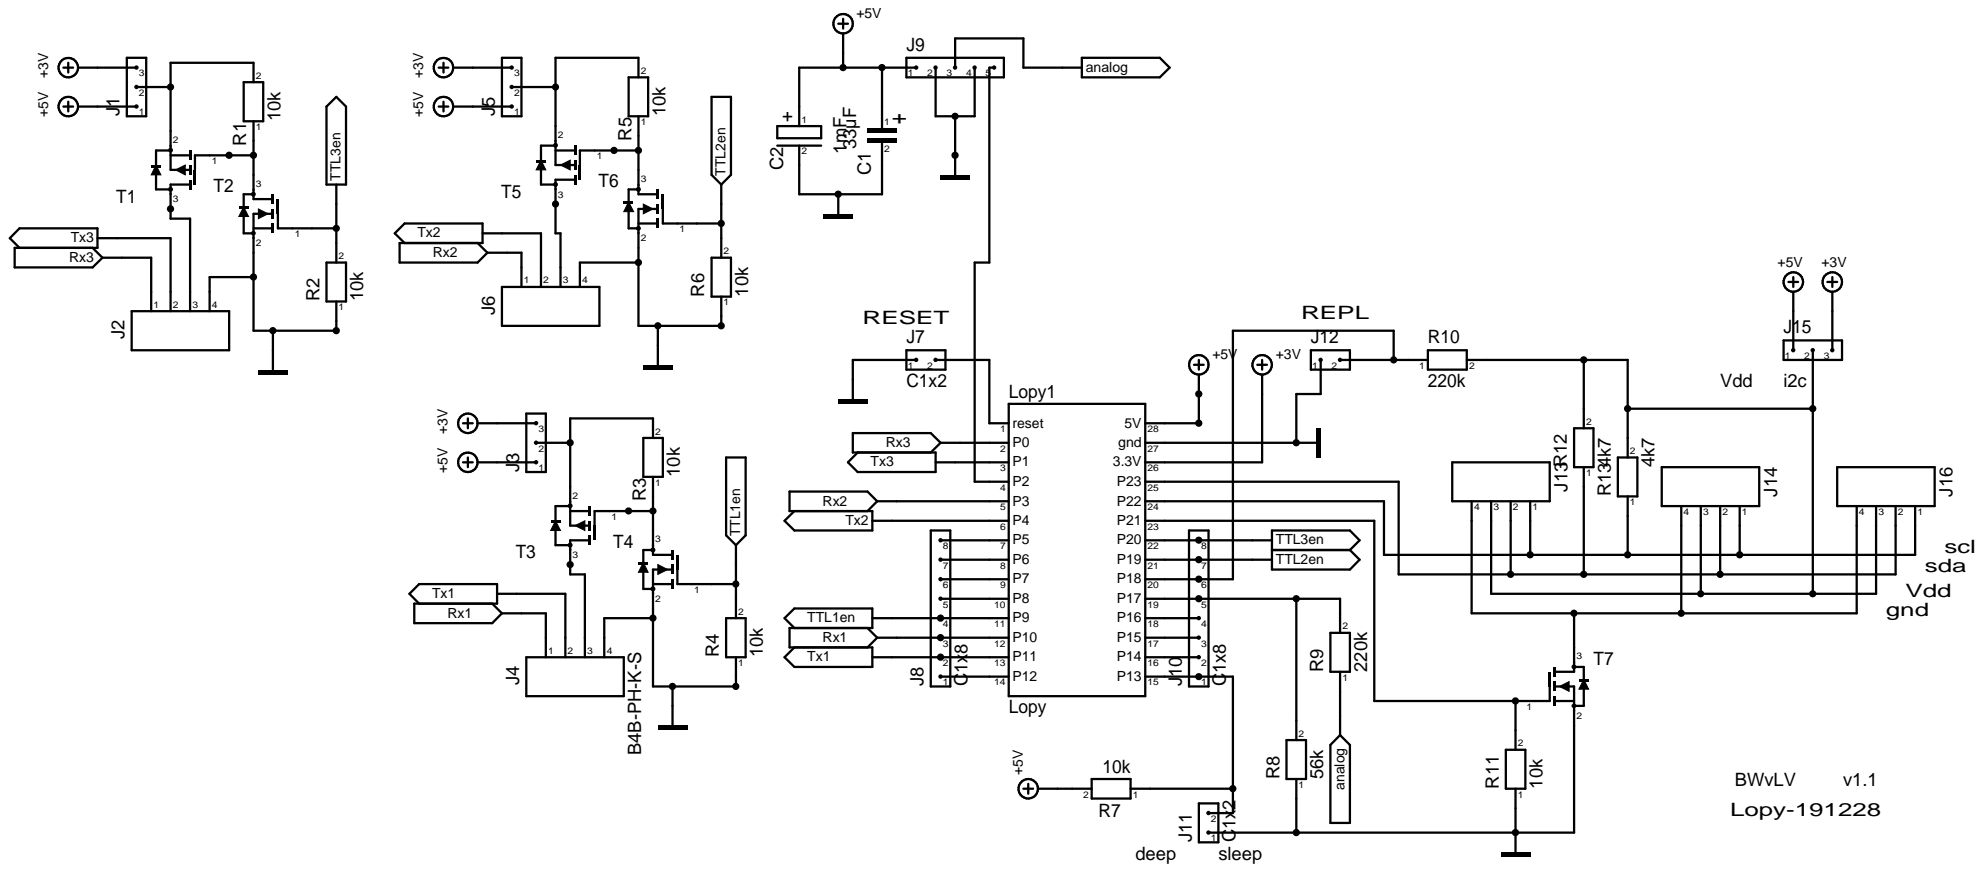
[picture p193: page 1]
