teusH/MySense/RPi/MyLUFTDATEN.py

#!/usr/bin/env python3
# -*- coding: utf-8 -*-
# Contact Teus Hagen webmaster@behouddeparel.nl to report improvements and bugs
# 
# Copyright (C) 2017, Behoud de Parel, Teus Hagen, the Netherlands
#
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

# $Id: MyLUFTDATEN.py,v 1.1 2019/10/25 15:55:42 teus Exp teus $

# TO DO: write to file or cache
# reminder: InFlux is able to sync tables with other MySQL servers

""" Publish measurements to Madavi.de and Luftdaten.info
    they will appear as graphs in http://www.madavi.de/sensor/graph.php
    Make sure to enable acceptance for publishing in the map of Luftdaten
    by emailing the prefix-serial and location details.
    if 'madavi' and/or 'luftdaten' is enabled in ident send them a HTTP POST
    Relies on Conf setting by main program
"""
modulename='$RCSfile: MyLUFTDATEN.py,v $'[10:-4]
__version__ = "0." + "$Revision: 1.1 $"[11:-2]

try:
    import MyLogger
    import sys
    import datetime
    import json
    import requests
    import signal
    from time import time
    import re
except ImportError as e:
    MyLogger.log(modulename,"FATAL","One of the import modules not found: %s" % e)

# configurable options
__options__ = ['output','luftdaten','madavi','id_prefix', 'serials', 'projects','active']

Conf = {
    'output': False,
    # defined by, obtained from LuftDaten: Rajko Zschiegner dd 24-12-2017
    'id_prefix': "TTNMySense-", # prefix ID prepended to serial number of module
    'luftdaten': 'https://api.luftdaten.info/v1/push-sensor-data/', # api end point
    'madavi': 'https://api-rrd.madavi.de/data.php', # madavi.de end point
    # expression to identify serials to be subjected to be posted
    'serials': '(f07df1c50[02-9]|93d73279d[cd])', # pmsensor[1 .. 11] from pmsensors
    'projects': 'VW2017',  # expression to identify projects to be posted
    'active': True,      # output to luftdaten maps is also activated
    'registrated': None, # has done initial setup
    # 'debug': True,       # print output on POSTs
}

# ========================================================
# write data directly to a database
# =======================================================
# once per session registrate and receive session cookie
# =======================================================
# TO DO: this needs to have more security in it e.g. add apikey signature
def registrate(net):
    global Conf
    if Conf['registrated'] != None:
            return Conf['registrated']
    if net['module'] is bool:
        if (not net['module']) or (not net['connected']): return False
    Conf['match'] = re.compile(Conf['projects']+'_'+Conf['serials'], re.I)
    Conf['registrated'] = True
    return Conf['registrated']

# Luftdaten nomenclature and ID codes:
sense_table = {
    "meteo": {
        # X-Pin codes as id used by Luftdaten for meteo sensors
        # from airrohr-firmware/ext_def.h
        "types": {
            # 680 pin nr is a guess
            'DHT22': 7, 'BME680': 11, 'BME280': 11, 'BME180': 11,
            'BMP280': 3, 'BMP180': 3,
            'DS18B20': 13, 'HTU21D': 7,
        },
        "temperature": ['temperature','temp','dtemp',],
        "humidity": ['humidity','hum','rv','rh',],
        "pressure": ['pres','pressure','luchtdruk',],
    },
    "dust": {
        # X-Pin codes as id used by Luftdaten for dust sensors
        # TO DO: complete the ID codes used by Luftdaten
        "types": {
            'SDS011': 1, 'PMS3003': 1, 'PMS7003': 1, 'PMS5003': 1,
            # SPS30 pin nr is a guess
            'SPS30': 1, 'HPM': 25, 'PPD42NS': 5, 'SHINEY': 5,
        },
        "P1": ['pm10','pm10_atm',],  # should be P10
        "P2": ['pm2.5','pm25'],      # should be P25
        # missing pm1
    },
}

# send only a selection of possible measurements from the sensors
# Post meteo and dust data separately
def sendLuftdaten(ident,values):
    global __version__, Conf
    # the Luftdaten API json template
    # suggest to limit posts and allow one post with multiple measurements
    headers = {
        'X-Sensor': Conf['id_prefix'] + ident['serial'],
        # 'X-Pin': str(integer_ID),  # this should be deprecated. It is doubling traffic
    }
    postdata = {
        'software_version': 'MySense' + __version__,
        # 'sensordatavalues': [{ sensor_field_id: %.2f float},]
    }
    postTo = []
    for url in ['madavi','luftdaten']:
        if (url == 'luftdaten') and (not Conf['active']): continue
        # post first to Madavi on succes maybe to Luftdaten
        if (url in ident.keys()) and ident[url]:
            postTo.append(Conf[url])
    if not len(postTo): return True
    for sensed in ['dust','meteo']:
        headers['X-Pin'] = None
        for sensorType in sense_table[sensed]['types']:
            if sensorType.lower() in [ x.lower() for x in ident['types']]:
                headers['X-Pin'] = str(sense_table[sensed]['types'][sensorType])
                break
        if not headers['X-Pin']: continue
        postdata['sensordatavalues'] = []
        for field in sense_table[sensed].keys():
            for valueField in values:
                if valueField in sense_table[sensed][field]:
                    postdata['sensordatavalues'].append({ 'value_type': field, 'value': str(round(values[valueField],2)) })
        if not len(postdata['sensordatavalues']): continue
        if not post2Luftdaten(headers,postdata,postTo):
            return False
    return True
        
# seems https may hang once a while
def alrmHandler(signal,frame):
    MyLogger.log(modulename,'ATTENT','HTTP POST hangup, post aborted. Alarm nr %d' % signal)
    # signal.signal(signal.SIGALRM,None)

def watchOn(url):
    if url[:6] != 'https:': return None
    rts = [None,0,0]
    rts[0] = signal.signal(signal.SIGALRM,alrmHandler)
    rts[1] = int(time())
    rts[2] = signal.alarm(3*60)
    return rts

def watchOff(prev):
    if prev == None: return 1
    alrm = signal.alarm(0)
    if prev[0] and (prev[0] != alrmHandler):
        signal.signal(signal.SIGALRM,prev[0])
        if prev[2] > 0: # another alarm and handler was active
            prev[1] = prev[2] - (int(time()) - prev[1])
            if prev[1] <= 0:
                prev[1] = 1
            signal.alarm(prev[1])
    return alrm
    
# do an HTTP POST to [ Madavi.de, Luftdaten, ...]
def post2Luftdaten(headers,postdata,postTo):
    global Conf
    # debug time: do not really post this
    if ('debug' in Conf.keys()) and Conf['debug']:
        MyLogger.log(modulename,'DEBUG',"Post headers: %s" % str(headers))
        MyLogger.log(modulename,'DEBUG',"Post data   : %s" % str(postdata))
    rts = True
    for url in postTo:
        # print("Luftdaten POST to %s" % url)
        # print("Post headers: %s" % str(headers))
        # print("Post data   : %s" % str(postdata))
        prev = watchOn(url)
        try:
            r = requests.post(url, json=postdata, headers=headers)
            # MyLogger.log(modulename,'INFO','Post to: %s' % url)
            MyLogger.log(modulename,'DEBUG','Post returned status: %d' % r.status_code)
            if not r.ok:
                MyLogger.log(modulename,'ERROR','Post to %s with status code: %d' % (headers['X-Sensor'],r.status_code))
        except requests.ConnectionError as e:
            MyLogger.log(modulename,'ERROR','Connection error: ' + str(e))
            rts = False
        except Exception as e:
            MyLogger.log(modulename,'ERROR','Error: ' + str(e))
            rts = False
        if not watchOff(prev):
            MyLogger.log(modulename,'ERROR','HTTP timeout error on %s' % url)
            rts = False
    return rts

notMatchedSerials = []
def publish(**args):
    global Conf, notMatchedSerials
    if (not 'output' in Conf.keys()) or (not Conf['output']):
        return
    for key in ['data','internet','ident']:
        if not key in args.keys():
            MyLogger.log(modulename,'FATAL',"Publish call missing argument %s." % key)
    if not registrate(args['internet']):
        MyLogger.log(modulename,'WARNING',"Unable to registrate the sensor.")
        return False 
    for key in ['project','serial']:
        if (not key in args['ident'].keys()) or (not args['ident'][key]):
            return True
    matched = Conf['match'].match(args['ident']['project']+'_'+args['ident']['serial'])
    # publish only records of the matched project/serial combi,
    # default Madavi is enabled for those matches
    if not matched:
        if not args['ident']['project']+'_'+args['ident']['serial'] in notMatchedSerials:
            notMatchedSerials.append(args['ident']['project']+'_'+args['ident']['serial'])
            MyLogger.log(modulename,'INFO',"Skipping records of project %s with serial %s to post to Luftdaten" % (args['ident']['project'],args['ident']['serial']))
        return True
    elif not 'madavi' in args['ident'].keys():  # dflt: Post to madavi.de
        args['ident']['madavi'] = True
    mayPost = False
    # if 'madavi' and/or 'luftdaten' is enabled in ident send them a HTTP POST
    for postTo in ['madavi','luftdaten',]:
        if not postTo in args['ident'].keys(): args['ident'][postTo] = False
        elif args['ident'][postTo]: mayPost = True
    if args['ident']['luftdaten']: args['ident']['madavi'] = True
    if mayPost: return sendLuftdaten(args['ident'],args['data'])
    return True

# test main loop
if __name__ == '__main__':
    from time import sleep
    Conf['output'] = True
    Conf['active'] = False      # no Post to Luftdaten in this test
    net = { 'module': True, 'connected': True }
    # Conf['debug'] = True        # e.g. print Posts
    Output_test_data = [
        {   'ident': {'geolocation': '?',
              'luftdaten': False,
              'description': 'MQTT AppID=pmsensors MQTT DeviceID=pmsensor11',
              'fields': ['time', 'pm25', 'pm10', 'temp', 'rv'],
              'project': 'VW2017', 'units': ['s', 'ug/m3', 'ug/m3', 'C', '%'],
              'serial': '93d73279dc',
              'types': ['time', u'SDS011', u'SDS011', 'DHT22', 'DHT22']},
           'data': {
                'pm10': 3.6, 'rv': 39.8, 'pm25': 1.4, 'temp': 25,
                'time': int(time())-24*60*60}},
        {   'ident': {
              'description': 'MQTT AppID=pmsensors MQTT DeviceID=pmsensor1',
              'luftdaten': False,
              'fields': ['time', 'pm25', 'pm10', 'temp', 'rv'],
              'project': 'VW2017', 'units': ['s', 'ug/m3', 'ug/m3', 'C', '%'],
              'serial': 'f07df1c500',
              'types': ['time', u'PMS7003', u'PMS7003', 'BME280', 'BME280']},
           'data': {
                'pm10': 3.6, 'rv': 39.8, 'pm25': 1.6, 'temp': 24, 'pressure': 1024.2,
                'time': int(time())-23*60*60}},
        {   'ident': {
              'geolocation': '51.420635,6.1356117,22.9',
              'version': '0.2.28', 'serial': 'test_sense', # no serial match
              'fields': ['time', 'pm_25', 'pm_10', 'dtemp', 'drh', 'temp', 'rh', 'hpa'],
              'extern_ip': ['83.161.151.250'], 'label': 'alphaTest', 'project': 'BdP',
              'units': ['s', 'pcs/qf', u'pcs/qf', 'C', '%', 'C', '%', 'hPa'],
              'intern_ip': ['192.168.178.49', '2001:980:ac6a:1:83c2:7b8d:90b7:8750',
                    '2001:980:ac6a:1:17bf:6b65:17d2:dd7a'],
              'types': ['time','Dylos DC1100', 'Dylos DC1100',
                'DHT22', 'DHT22', 'BME280', 'BME280', 'BME280'],
              },
            'data': {
              'drh': 29.3, 'pm_25': 318.0, 'temp': 28.75,
              'time': 1494777772, 'hpa': 712.0, 'dtemp': 27.8,
              'rh': 25.0, 'pm_10': 62.0 },
        },
        ]
    for post in Output_test_data:
        try:
            if publish(
                ident=post['ident'],
                data=post['data'],
                internet=net
            ):
                print "Published\n"
            else:
                print "ERROR\n"
        except Exception as e:
            print("output channel error was raised as %s" % e)
            eak
