teusH/MySense/RPi/MyDISPLAY.py

#!/usr/bin/env python3
# -*- coding: utf-8 -*-
# Contact Teus Hagen webmaster@behouddeparel.nl to report improvements and bugs
# 
# Copyright (C) 2017, Behoud de Parel, Teus Hagen, the Netherlands
#
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

# $Id: MyDISPLAY.py,v 1.9 2018/08/29 15:29:28 teus Exp teus $

""" Publish measurements to display service
    Relies on Conf setting by main program
"""
modulename='$RCSfile: MyDISPLAY.py,v $'[10:-4]
__version__ = "0." + "$Revision: 1.9 $"[11:-2]

try:
    import MyLogger
    import sys
    import datetime
    import socket
    from time import time, sleep
except ImportError as e:
    MyLogger.log(modulename,"FATAL","One of the import modules not found: %s" % e)

# configurable options
__options__ = ['output','port']

Conf = {
    'output': False,
    'host': 'localhost', # host InFlux server, key 'host': no need for internet access
    'port': 2017,        # default display port number
    'fd': None,          # have sent to db: current fd descriptor, 0 on IO error
    'omit' : ['time','geolocation',],  # fields not archived
    'match': [		 # translation table for db and unit names
        ('pm_','PM'),
        ('PM25','PM2.5'),
        ('PM1','PM1'),
        ('C','oC'),
        ('F','oF'),
        ('o3','O3'),
        ('co','CO'),
        ('no','NO'),
        ('nh','NH'),
        ('pha','air'),
        ('pcs/0.01qf','pcs/qf'),
        ('pcs','#'),
           ],
}

# ========================================================
# write data directly to a database
# ========================================================
# create table <ProjectID_Serial>, record columns,
#       registration Sensors table on the fly
def attributes(**t):
    global Conf
    Conf.update(t)

def displayMsg(msg):
    global Conf
    # degree = u'\N{DEGREE SIGN}'
    # micro = u'\N{MICRO SIGN}'
        
    if not len(msg): return True
    if not type(msg) is list: msg = msg.split("\n")
    for i in range(len(msg)-1,-1,-1): 
        if not len(msg[i]):
            msg.pop(i)
            continue
        msg[i] = format(msg[i])
        if msg[i][-1] == "\n": msg[i] = msg[i][:-1]
        # no unicode for socket send
        # msg[i] = msg[i].replace('oC',degree + 'C')
        #msg[i] = msg[i].replace('ug/m3',micro + 'g/m³')
        # msg[i] = msg[i].replace('ug/m3',micro + 'g/m3')
    msg = "\n".join(msg) + "\n"
    if not len(msg): return True
    try:
        sock = socket.socket(socket.AF_INET, socket.SOCK_STREAM)
        sock.connect((Conf['host'],Conf['port']))
        sock.send(msg)
        sock.close()
        return True
    except:
        raise IOError("Unable to talk to display service")
        return False

# connect to db and keep connection as long as possible
def db_connect(geo,name):
    """ Display geo location and name on display """
    global Conf
    if not 'fd' in Conf.keys(): Conf['fd'] = False
    if not Conf['fd']:
        Conf['port'] = int(Conf['port'])
        if (Conf['host'] != 'localhost') and (not Conf['port']):
            MyLogger.log(modulename,'ERROR',"Access display service %s / %d."  % (Conf['host'], Conf['port']))      
            Conf['output'] = False
            return False
        if (Conf['fd'] != None) and (not Conf['fd']): # should not happen, internal error
            MyLogger.log(modulename,'ERROR','Unable to use display service')
            Conf['output'] = False
            return False
        try:
            lines = []
            lines.append(datetime.datetime.fromtimestamp(time()).strftime('At %Hh %Mm%Ss ') + ' MySense activated')
            if len(name): lines.append(name)
            if geo:
                geo = geo.split(',')
                if len(geo) == 3:
                    lines.append('long: %8.5f, lat: %8.5f, alt: %dm' % (float(geo[0]),float(geo[1]),int(float(geo[2]))))
                elif len(geo) == 2:
                    lines.append('long: %8.5f, lat: %8.5f' % (float(geo[0]),float(geo[1])))
            displayMsg(lines)
            sleep(30)   # allow some time to read the ident info
            Conf['fd'] = True
        except IOError:
            MyLogger.log(modulename,'ERROR',"Access display service on %s / %d. Display Server is running?"  % (Conf['host'], Conf['port']))      
            Conf['output'] = False
    return Conf['fd']

# registrate the sensor to the Sensors table and update location/activity
def db_registrate(ident):
    """ create or update identification inf to Sensors table in database """
    global Conf
    if ("registrated" in Conf.keys()) and (Conf['registrated'] != None):
        return Conf['registrated']
    if len(ident['fields']) == 0:
        return False
    geo = ''
    if 'geolocation' in ident.keys(): geo = ident['geolocation']
    name = ''
    for item in ['project','serial','label']:
        if (item in ident.keys()) and len(ident[item]):
            if len(name): name += ', '
            name += item + ': ' + ident[item]
    if not db_connect(geo,name):
        return False
    Conf["registrated"] = True
    return True

def publish(**args):
    """ add records to the database,
        on the first update table Sensors with ident info """
    global Conf, ErrorCnt
    if (not 'output' in Conf.keys()) or (not Conf['output']):
        return
    for key in ['data','ident']:
        if not key in args.keys():
            MyLogger.log(modulename,'FATAL',"Publish call missing argument %s." % key)

    # TO DO: get the translation table from the MySense.conf file
    def trans(name):
        global Conf
        if (not 'match' in Conf.keys()) or (not type(Conf['match']) is list):
            return name
        for item in Conf['match']:
             if not type(item) is tuple: continue
             if name.find(item[0]) < 0: continue
             name = name.replace(item[0],item[1])
        return name

    def findInfo(ident,field):
        UT = ['','']   # (unit,sensor type)
        try:
            indx = ident['fields'].index(field)
            UT[0] = ident['units'][indx]
            UT[1] = ident['types'][indx].upper()
        except:
            pass
        finally:
            return (UT[0],UT[1])

    if Conf['fd'] == None: Conf['registrated'] = None
    if not db_registrate(args['ident']):
        MyLogger.log(modulename,'WARNING',"Unable to registrate the sensor.")
        return False
    if Conf['fd'] == None:
        return False
   
    if 'text' in args['data'].keys():   # special case, overloading this method
        # show a text line as eg starting up sensor X
        if type(args['data']['text']) is str:
            displayMsg(['<clear>' + args['text']])
        elif type(args['data']['text']) is list:
            lines = []
            for string in args['data']['text']:
                if type(string) is str: lines.append(string)
            if len(lines):
                try: displayMsg(lines)
                except:
                    MyLogger.log(modulename,'ERROR','Unable to send text to display service.')
                    return False
        return True

    lines = ['','','','']   # sensor type, DB name, unit, value
    for item in args['data'].keys():
        if item in Conf['omit']: continue
        if type(args['data'][item]) is list:
            MyLogger.log(modulename,'WARNING',"Found list for sensor %s." % item)
            continue
        else:
            if args['data'][item] == None: continue
            Unit, Type = findInfo(args['ident'],item)
            bar = ''
            if len(lines[0]): bar = '|'
            thisValue = args['data'][item]
            if thisValue is float:
                thisValue = '%.1f' % thisValue
            elif Type[0:3] == 'gps': continue   # do not display geo location
            string = format(thisValue).replace('.0','')
            if string[0] == '<': string = 'NaN'       # not a number of string
            lines[0] += bar +  '%6.6s' % Type
            lines[1] += bar + ' %5.5s' % trans(item)
            lines[2] += bar + ' %5.5s' % trans(Unit)
            lines[3] += bar +  '%6.6s' % string
    lines.insert(0,'<clear>' + datetime.datetime.fromtimestamp(time()).strftime('%d %b %Hh%M:%S'))
    if 'time' in args['data'].keys():
        try:
            lines[0] = '<clear>' + datetime.datetime.fromtimestamp(args['data']['time']).strftime('%d %b %H:%M:%S')
        except:
            pass
    try:
        displayMsg(lines)
    except:
        MyLogger.log(modulename,'ERROR','Unable to send text to display service.')
        return False
    return True

# test main loop
if __name__ == '__main__':
    Conf['output'] = True
    Conf['port'] = 2017
    try:
        import Output_test_data
    except:
        print("Please provide input test data: ident and data.")
        exit(1)

    for cnt in range(0,len(Output_test_data.data)):
        timings = time()
        try:
            publish(
                ident=Output_test_data.ident,
                data = Output_test_data.data[cnt],
            )
        except Exception as e:
            print("output channel error was raised as %s" % e)
            break
        timings = 30 - (time()-timings)
        if timings > 0:
            print("Sleep for %d seconds" % timings)
            sleep(timings)
