teusH/MySense/RPi/MyGPS.py

#!/usr/bin/env python3
# -*- coding: utf-8 -*-
# Contact Teus Hagen webmaster@behouddeparel.nl to report improvements and bugs
#
# Copyright (C) 2017, Behoud de Parel, Teus Hagen, the Netherlands
#
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

# $Id: MyGPS.py,v 2.16 2018/05/27 10:27:47 teus Exp teus $

# TO DO:
#

""" Get geo location and time from GPSD daemon
    Works with a thread to collect geo data
    Relies on Conf setting by main program
"""
modulename='$RCSfile: MyGPS.py,v $'[10:-4]
__version__ = "0." + "$Revision: 2.16 $"[11:-2]

import os
from time import time, sleep
import threading
try:
    import MyLogger
except ImportError as e:
    MYLogger.log('FATAL',"Missing module %s" %e)

# configurable options
__options__ = [
        'input',
        'host','port',
        'raw',
        'interval','sync'
]

Conf = {
    'input': False,     # no GPS installed
    'type': 'GPSd',     # type of geolocator module
    'fields': ['geo','time'],
    'units': ['r,r,m','s'],# radials or d (degrees)
    'host': '127.0.0.1',# default gspd service
    'port': 2947,       # default unix socket port for gpsd
    'interval': 5*60,     # read location every interval seconds
    'sync': False,	# get geo info in sync with main process
    'raw': False,       # print raw measurements
    'debug': False,     # be more versatile
}

MyThread = None         # ref to GPS class, may run asynchronous
GPSthreads = None       # geo multi thread if activated

class GPSthread(threading.Thread):
    from gps3 import gps3
    from time import time, sleep

    STOP = False
    threadLock = threading.Lock() # lock to be used for average of values in buffer

    def __init__(self, **args):
        threading.Thread.__init__(self)
        inits = {}                  # defaults
        inits['interval'] = 5       # internal max minutes interval for new values
        inits['DEBUG'] = False      # be more versatile
        inits['host'] = '127.0.0.1' # localhost gpsd socket
        inits['port'] = '2947'      # default GPS daemon port
        inits['sync'] = False       # run in multi threaded modus
        inits['raw'] = False        # display raw geo values
        for key in args.keys():
            inits[key] = args[key]
        self.TINTERV = inits['interval']  # internal max interval for new values
        self.ReOpen = False         # reopen on every getRecord connection to daemon
        if not self.TINTERV: self.ReOpen = True
        self.DEBUG = inits['DEBUG']       # debug modus
        self.host = inits['host']
        self.port = inits['port']
        self.name = 'GPS client'
        self.GPSsock = None
        self.sync = inits['sync']
        self.raw = inits['raw']
        self.cur_val = {}                 # current location record

    def getRecord(self):
        for i in range(0,5):
            with self.threadLock:
                if len(self.cur_val):
                    return {
                       'time': self.cur_val['time'],
                       'geo': self.cur_val['geo'],
                       }
            self.sleep(1)
        return {}

    def GPSstart(self):
        prev_t = int(self.time()) ; prev_l = ['lat','lon','alt']
        if self.GPSsock == None:
            self.GPSdata = None
            self.GPSdata = self.gps3.DataStream()
            self.GPSsock = self.gps3.GPSDSocket()
            self.GPSsock.connect()
        self.GPSsock.watch()
        for new_data in self.GPSsock:
            if self.STOP: return
            if new_data:
                self.GPSdata.unpack(new_data)
	        if self.GPSdata.TPV['device'] == 'n/a':
		        continue
                rec = { 'time': int(self.time()) }
                geo = []
                rvals = []
                for item in ['lat','lon','alt']:
                    if self.GPSdata.TPV[item] != 'n/a':
                        try:
                            val = float(self.GPSdata.TPV[item])
                            # altitude is +- 5 meters
                            # TO DO: add distance calculation
                            if item != 'alt': strg = '%8.5f' % val
                            else: strg = '%8.1f' % val
                            strg = strg.rstrip('0').rstrip('.') if '.' in strg else strg
                            strg = strg + '.0' if not '.' in strg else strg
                            strg = strg.strip(' ')
                            geo.append(strg)
                            rvals.append('%s=%s' % (item, strg.replace(' ','')))
                        except:
                            pass
                    elif self.DEBUG:
                        print("Got for %s geo 'n/a'" % item)
                if len(geo) == 3:
                    rec['geo'] = ','.join(geo)
                    if self.DEBUG:
                        print("Got new GPS rec: %s (lat,lon,alt)" % rec['geo'])
                    if (prev_l[0] != geo[0]) or (prev_l[1] != geo[1]):
                        prev_t = rec['time']; prev_l = geo
                        with self.threadLock: self.cur_val = { 'time': time(), 'geo': rec['geo']}
                        if (self.raw != None) and (not type(self.raw) is bool) and len(geo):
                            self.raw.publish(
                                tag='geo',
                                data='lat=%s,lon=%s,alt=%s' % (geo[0],geo[1],geo[2])
                                )
                    # slow down if no change in TINTERV minutes
                    elif rec['time'] - prev_t > self.TINTERV:
                        if not self.sync:
                            with self.threadLock: self.cur_val['time'] = 0
                    break
        self.GPSsock.watch(enable=False)
        if self.ReOpen:
            self.GPSsock.close()
            self.GPSsock = None
            self.GPSdata = None
        return

    def GPSclient(self):
        while not self.STOP:
            try:
                self.GPSstart()
                self.sleep(0.5)	# allow client time to start collecting
            except:
                raise IOError("GPS daemon is disconnected")
                self.STOP = True
            if self.sync:
                return
            if self.DEBUG:
                print("Long time sleep")
            if not self.STOP: self.sleep(self.TINTERV)
        return

# initialize
def start_thread():
    from time import sleep
    global Conf, MyThread, GPSthreads
    if MyThread.STOP:
        return True
    if not Conf['sync']:
        try:
            GPSthreads = threading.Thread(target=MyThread.GPSclient)
            GPSthreads.start()
        except StandardError as e:
            MyLogger.log(modulename,'ERROR',"Unable to start thread." % e)
            return False
        sleep(1)      # allow some data to come in
    return True

def stop_thread():
    MyThread.STOP = True        # ask self threads to stop
    try:
        threading.join()
    except:
        pass
    MyLogger.log(modulename,'WARNING',"Stopped thread.")
    return

# set inital configuration values and ready GPSD thread
def registrate():
    global Conf, MyThread
    if not Conf['input']: return False
    if MyThread != None:
        return True
    Conf['input'] = True
    if MyThread == None:        # only once
        try:
            MyThread = GPSthread(
                interval=Conf['interval'],
                port = Conf['port'],
                host=['host'],
                sync=Conf['sync'],
                raw=Conf['raw'],
                DEBUG=Conf['debug'])
            # first call is interval secs delayed by definition
            if not Conf['interval']: Conf['sync'] = True
            if Conf['sync']: return True
            if start_thread():
                return True
        except:
            pass
        MyThread = None
    raise IOError("Unable to registrate/start GPS thread.")
    Conf['input'] = False
    return False

# get data from GPSD thread
def getdata():
    """ getdata() is interface to collect GPS data:
	{time(long:seconds), geo(string:lat,lon,alt) }
    """
    global Conf, MyThread
    if not registrate():                # start up input readings
        return {}
    try:
        if Conf['sync']: MyThread.GPSclient()
        rec = MyThread.getRecord()     # pick up a record
        if not 'geo' in rec.keys():
            return {}                  # for 5 minutes no geo change
        return rec
    except IOError as er:
        MyLogger.log(modulename,'WARNING',"Sensor input failure: %s" % er)
    return {}

# test main loop
if __name__ == '__main__':
    from time import sleep
    import sys
    Conf['input'] = True
    # Conf['sync'] = True      # sync = False will start async collect
    Conf['debug'] = True       # True will print GPSD collect info from thread
    # Conf['raw'] = True
    # Conf['interval'] = 0
    nr = 10
    if len(sys.argv) > 1:
        try: nr = int(sys.argv[1])
        except: pass
    if nr == 1:
        Conf['debug'] = False
        Conf['sync'] = True
        Conf['interval'] = 0
    for cnt in range(0,nr):
        timing = time()
        try:
            data = getdata()  # get geo info from thread
        except Exception as e:
            print("input sensor error was raised as %s" % e)
            sys.exit(1)
        if nr == 1:
            if 'geo' in data.keys():
              print(data['geo'])
              sys.exit(0)
            else: sys.exit(1)
        else:
            print("Getdata returned:")
            print(data)
        timing = 15 - (time()-timing)
        if timing > 0:
            if Conf['debug']:
                print("Slowing down for %d/15 seconds for new cycle." % timing)
            sleep(timing)
    if (not Conf['sync']) and (MyThread != None):
        MyThread.stop_thread()
