teusH/MySense/RPi/MyARDUINO.py

#!/usr/bin/env python3
# -*- coding: utf-8 -*-
# Contact Teus Hagen webmaster@behouddeparel.nl to report improvements and bugs
# 
# Copyright (C) 2017, Behoud de Parel, Teus Hagen, the Netherlands
#
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

# $Id: MyARDUINO.py,v 1.21 2017/06/07 21:38:45 teus Exp teus $

# TO DO: open_serial function may be needed by other modules as well?
#       add more sensors

# Defeat: output average PM count over 59(?) or 60 seconds:
#         monitor mode: 60 times per hour of 30 seconds samples per PM

"""
    Get sensor values via the Arduino board serial USB interface.
    Relies on Conf setting by main program
    Output dict with Shinyei PPD42NS and maybe other sensors
    Arduino produces lines output (json string) like (format: <type>_<unit>):
    sync:
    {} EOL-char
    configuration:
    { "version": "1.05","type": "PPD42NS",
      "interval": 60, "sample: 20, "request": False } EOL-char
    data:
    { "pm25_count":null,"pm25_ratio":null,"pm25_pcs/cf":null,"pm25_ug/m3":null,
    "pm10_count":2435471,"pm10_ratio":8.02,"pm10_pcs/cf":4490,"pm10_ug/m3":7.00
    } EOL-char

    Arduino firmware can operate in two modes:
        driven on send values requests (request == True, send any char not 'C')
        every interval (dftl 60 secs) a sample (flt 15 secs)
    Firmware config Options: interval, sample and mode. Send command line::
    'C interval sample R<EOL>'
    Arduino responds with configuration json string
    where interval/sample is a number (in secs), R (request mode) is optional
    Request mode timeout is 1 hour.
"""
modulename='$RCSfile: MyARDUINO.py,v $'[10:-4]
__version__ = "0." + "$Revision: 1.21 $"[11:-2]

# configurable options
__options__ = [
    'input','type','usbid','firmware',
    'calibrations',      # calibration per sensor
    'interval','sample', # report interval in secs, sample timing in secs
    'bufsize', 'sync',   # multithead buffer size and search for input
    'fields',            # record names for values collected
    # 'units',           # Arduino is defining record names and units
    'raw',               # display raw measurements
    'file',              # records input file for debugging
]

Conf = {
    'input': False,      # Dylos input sensor is required
    'fd': None,          # input handler
    'type': "Arduino Uno",   # type of sensor(s) controller
    'usbid': 'usb-Arduino_srl_', # usb ID via lsusb
    'firmware': '1.08',  # firmware number
     # define 'names': [] if one want to extract the names from firmware, but
     # note the order of names and so map to 'fields' is then at random
    'names': ['pm25','pm10'],  # record names as provided by firmware
    'fields': ['pm25','pm10'], # types of pollutants
     # 'pcs/qf' particle count per qubic foot per sample timing
     # 'ug/m3' particle count per qubic foot per sample timing per minute
     # 'count' and 'ratio' (0-100) per sample timing
    'units' : ['pcs/qf','pcs/qf'], # per type the measurment unit
    'calibrations': [[0,1],[0,1]], # per type calibration (Taylor serie)
    'interval': 60,     # read interval in secs (dflt)
    'sample': 30,       # sample timing for the count (seconds)
    'bufsize': 30,      # size of the window of values readings max
    'sync': False,      # use thread or not to collect data
    'debug': False,     # be more versatile on input data collection
    'keys': [],         # set of keys from firmware to be exported
    'raw': False,       # dflt value, no raw measurements displayed
    'file': None,       # debug records from input file

}
#    from MySense import log
try:
    try:
        import os
        from time import time
        from time import sleep
        import MyLogger
        import serial
    except:
        try:
            import Serial as serial
        except ImportError as e:
            MyLogger.log(modulename,'FATAL',"Missing module %s" % e)
    import re
    import subprocess           # needed to find the USB serial
    import MyThreading          # needed for multi threaded input
    import json                 # Arduino will export json data
except ImportError as e:
    MyLogger.log(modulename,'FATAL',"Missing module %s" % e)

# calibrate as ordered function order defined by length calibration factor array
def calibrate(nr,conf,value):
    if (not 'calibrations' in conf.keys()) or (nr > len(conf['calibrations'])-1):
        return value
    if type(value) is int:
        value = value/1.0
    if not type(value) is float:
        return None
    rts = 0.0; pow = 0
    for a in Conf['calibrations'][nr]:
        rts += a*(value**pow)
        pow += 1
    return round(rts,1)

# =======================================================================
# serial USB input or via (test) input file
# =======================================================================
def open_serial():
    global Conf
    #  scan for available ports. return a list of tuples (num, name)
    if Conf['fd'] != None:
        return True

    if (not Conf['file']) and Conf['usbid']:
        serial_dev = None
        if Conf['usbid'] != None:
            # try serial with product ID
            byId = "/dev/serial/by-id/"
            if not os.path.exists(byId):
                MyLogger.log(modulename,'FATAL',"There is no USBserial connected. Abort.")
            device_re = re.compile(".*\s%s.*(?P<device>ttyACM\d+)$" % Conf['usbid'], re.I)
            devices = []
            try:
                df = subprocess.check_output(["/bin/ls","-l",byId])
                for i in df.split('\n'):
                    if i:
                        info = device_re.match(i)
                        if info:
                            dinfo = info.groupdict()
                            serial_dev = '/dev/%s' % dinfo.pop('device')
                            break
            except CalledProcessError:
                MyLogger.log(modulename,'ERROR',"No serial USB connected.")
            except (Exception) as error:
                MyLogger.log(modulename,'ERROR',"Serial USB %s not found, error:%s"%(Conf['usbid'], error))
                Conf['usbid'] = None
        if Conf['usbid'] == None:
            MyLogger.log(modulename,'WARNING',"Please provide serial USB producer info.")
            MyLogger.log(modulename,'FATAL',"No USB input stream defined.")
            return False
        #Initialize Serial Port
        try:
            Conf['fd'] = serial.Serial(  # for here tuned for Dylos
                serial_dev,
                baudrate=9600,
                parity=serial.PARITY_NONE,
                stopbits=serial.STOPBITS_ONE,
                bytesize=serial.EIGHTBITS,
                timeout=65*60)  # allow also monitor mode
            MyLogger.log(modulename,'INFO',"Serial USB: %s" % serial_dev)
            sleep(2)    # give Arduino some time to reset
        except (Exception) as error:
            MyLogger.log(modulename,'FATAL',"%s" % error)
            return False
        # configure the Arduino with interval and sample timing
        if type(Conf['interval']) is str: Conf['interval'] = int(Conf['interval'])
        if (Conf['interval'] < 0) or (Conf['interval'] > 3600):
            Conf['interval'] = 60
        if type(Conf['sample']) is str: Conf['sample'] = int(Conf['sample'])
        if Conf['sample'] <= 10:
            Conf['sample'] = 10
            MyLogger.log(modulename,'WARNING','Shinyei dust adjusted sample time to 10 secs')
        if Conf['sample'] > Conf['interval']/2:
            Conf['interval'] = 2 * Conf['sample']
            MyLogger.log(modulename,'WARNING','Shinyei dust adjusted interval time to %d secs' % Conf['interval'])
        cnt = 0
        # start arduino with config details, try to synchronize
        while True:
            if (cnt%4) == 0:    # configure Arduino firmware
                Conf['fd'].write("C %d %d\n" % (Conf['interval'],Conf['sample'])) 
            cnt += 1
            line = Conf['fd'].readline()
            try:
                i = line.index('{')
            except ValueError:
                continue
            line = line[i:]
            while line.count('{') > 1:
                if len(line) < 3: break
                line = line[line.index('{')+1:]
            try:
                i = line.index('}')
                line = line[0:line.index('}')+1]
            except ValueError:
                continue
            try:
                config = json.loads(line[line.index('{'):line.index('}')+1])
                if (Conf['interval'] != config['interval']) or (Conf['sample'] != config['sample']):
                    MyLogger.log(modulename,'WARNING',"Conf != Arduino conf: interval %d~%d sample %d~%d" % (Conf['interval'],config['interval'],Conf['sample'],config['sample']))
                Conf['interval'] = config['interval']
                Conf['sample'] = config['sample']
                if Conf['firmware'][0] != config['version'][0]:
                    MyLogger.log(modulename,'ERROR',"Firmware %s incompatible, need version %s" % (Conf['firmware'][0],config['version'][0]))
                    return False 
                Conf['firmware'] = config['version']
                if 'type' in config.keys():
                    if Conf['type'] != config['type']:
                        MyLogger.log(modulename,'ATTENT','%s sensor(s) type: %s' % (Conf['type'],config['type']));
                    Conf['type'] = config['type']
                # if 'fields' in config.keys(): Conf['fields'] = config['fields']
                break
            except:
                continue
            if cnt > 12:
                MyLogger.log(modulename,'ERROR', "Unable to start")
                return False
    elif Conf['file']:
        try:
            Conf['fd'] = open(Conf['file'])
            Conf['sync'] = True
        except:
            MyLogger.log(modulename,'FATAL', "Failed top open test input from %s" % Conf['file'])
            return False
    else: return False
    return True

MyThread = None
def registrate():
    global Conf, MyThread
    if not Conf['input']: return False
    if Conf['fd'] != None: return True
    Conf['input'] = False
    if (Conf['type'] == None) or (Conf['type'][0:7].lower() != 'arduino'):
        return False
    Conf['keys'] = []
    if type(Conf['names']) is list:
        for i in range(0,len(Conf['fields'])):
            Conf['keys'].append("%s_%s" % (Conf['names'][i],Conf['units'][i].replace('#','')))
    if not open_serial():
        return False
    Conf['input'] = True
    if MyThread == None: # only the first time
        MyThread = MyThreading.MyThreading( # init the class
            bufsize=Conf['bufsize'],
            interval=Conf['interval'],
            name='Arduino PM sensors',
            callback=Add,
            conf=Conf,
            sync=Conf['sync'],
            DEBUG=Conf['debug'])
        # first call is interval secs delayed by definition
        try:
            if MyThread.start_thread(): # start multi threading
                return True
        except:
            pass
        MyThread = None
    raise IOError("Unable to registrate/start Arduino input thread.")
    Conf['input'] = False
    return False

# ================================================================
# Arduino Shinyei PDD42 PM count per minute per cubic food input via serial USB
# Arduino may handle more sensors as eg DHT, gas etc.
# ================================================================
# get a record
Conf['Serial_Errors'] = 0
def Add(conf):
    bin_data = {}
    try:
        try:
            if (not conf['file']) and (conf['interval'] == 0):
                # request a json string
                conf['fd'].write("\n")
            line = conf['fd'].readline()
            if not conf['file']:
                while conf['fd'].inWaiting():       # skip to latest record
                    line = conf['fd'].readline()
            Serial_Errors = 0
        except IOError as er:
            conf['Serial_Errors'] += 1
            MyLogger.log(modulename,'ATTENT',"Serial error: %s, retry close/open serial." % er)
            try:
                conf['fd'].close()
            except:
                pass
            conf['fd'] = None
            if conf['Serial_Errors'] > 10:
                MyLogger.log(modulename,'ERROR',"To many serial errors. Disabled.")
                sleep(1)
                conf['output'] = False
                return {}
            return conf['getdata']()
        except StandardError as er:
            MyLogger.log(modulename,'ATTENT',"Serial access error: %s" % er)
            pass
        line = str(line.strip().decode('utf-8'))
        s = line.find('{') ; l = line.find('}')
        if (s < 0) or (l < 0):
            # MyLogger('WARNING','Not a json input value: %s' % line)
            sleep(1)
            return bin_data
        try:
            bin_data = json.loads(line[s:(l+1)])
        except:
            # Arduino Error
            MyLogger('WARNING',"Arduino Data: Error - json data load")
        if len(bin_data) <= 0:
            sleep(1)
            return bin_data
    except (Exception) as error:
        # Some other Arduino Error
        MyLogger.log(modulename,'WARNING','Error in Add routine: %s' % error)
        sleep(1)
        return {}
    if ('firmware' in conf.keys()) and ('version' in bin_data.keys()):
        if conf['firmware'][0] != bin_data['version'][0]:
            MyLogger.log(modulename,'FATAL','Version/firmware incompatible')
        del bin_data['version']
    if 'type' in bin_data.keys():
        if conf['type'] != bin_data['type']:
            MyLogger.log(modulename,'ATTENT','%s sensor(s) type: %s' % (conf['type'],bin_data['type']));
            conf['type'] = bin_data['type']
        del bin_data['type']
    if len(conf['keys']):
        for key in bin_data.keys():
            if not key in conf['keys']:
                del bin_data[key]
                if not 'keys_skipped' in conf.keys(): conf['keys_skipped'] = []
                if not key in conf['keys_skipped']:
                    MyLogger.log(modulename,'ATTENT','Skip value with name %s.' % key)
                    conf['keys_skipped'].append(key)
    else:       # at start: denote all record names/units from Arduino firmware
        conf['keys'] = []; conf['names'] = []
        conf['units'] = []
        if not 'calibrations' in conf.keys(): conf['calibrations'] = []
        if not 'fields' in conf.keys(): conf['fields'] = []
        nr = 0
        for key in bin_data.keys():
            conf['keys'].append(key)
            id_un = key.split('_'); nr += 1
            if nr > len(conf['fields']): conf['fields'].append(id_un[0])
            if nr > len(conf['calibrations']): conf['calibrations'].append = [0,1]
            conf['names'].append(id_un[0])
            conf['units'].append(id_un[1].replace('#',''))
            MyLogger.log(modulename,'ATTENT','New nr %d sensor added: %s units %s' % (nr,id_un[0],id_un[1]))
    raw = []
    for i in range(0,len(conf['fields'])):
        dataKey = '%s_%s' % (conf['names'][i],conf['units'][i])
	if (type(bin_data[dataKey]) is float) or (type(bin_data[dataKey]) is int):
        	raw.append('%s=%.1f' % (dataKey.replace('/','').replace('.',''),bin_data[dataKey]*1.0))
        if dataKey in bin_data.keys():
            bin_data.update( {conf['fields'][i]:calibrate(i,conf,bin_data[dataKey])})
            del bin_data[dataKey]
    if ('raw' in conf.keys()) and (Conf['raw'] != None) and len(raw):
        conf['raw'].publish(
            tag='%s' % conf['type'].lower(),
            data='%s' % ','.join(raw))
    bin_data.update( {"time": int(time())} )
    return bin_data

def getdata():
    global Conf, MyThread
    if not registrate():                # start up input readings
        return {}
    try:
        return MyThread.getRecord()     # pick up a record
    except IOError as er:
        MyLogger.log(modulename,'WARNING',"Sensor input failure: %s" % er)
    return {}

Conf['getdata'] = getdata	# Add needs this global viariable

# test main loop
if __name__ == '__main__':
    from time import sleep
    Conf['input'] = True
    Conf['sync'] = True
    Conf['debug'] = True
    for cnt in range(0,10):
        timing = time()
        try:
            data = getdata()
        except Exception as e:
            print("input sensor error was raised as %s" % e)
            break
        print("Getdata returned:")
        print(data)
        timing = 60 - (time()-timing)
        if timing > 0:
            sleep(timing)
    if MyThread != None:
        MyThread.stop_thread()
