teusH/MySense/RPi/MyRSSI.py

#!/usr/bin/env python3
# -*- coding: utf-8 -*-
# Contact Teus Hagen webmaster@behouddeparel.nl to report improvements and bugs
# 
# Copyright (C) 2017, Behoud de Parel, Teus Hagen, the Netherlands
#
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

# $Id: MyRSSI.py,v 1.8 2017/06/26 07:09:52 teus Exp teus $

# TO DO:

""" wifi rssi values
"""
modulename='$RCSfile: MyRSSI.py,v $'[10:-4]
__version__ = "0." + "$Revision: 1.8 $"[11:-2]

# configurable options
__options__ = ['input','fields','units','raw']

Conf = {
    'input': False,
    # 'rssi':     None,   # if wifi provide signal strength
    # 'last':     None,   # last time checked to throddle connection info
    'fields': ['rssi'],   # strength or signal level
    'units' : ['dBm'],    # per field the measurement unit
    'raw': False,         # no raw measurements displayed by dflt
}

try:
    import MyLogger
    import re
    # import subprocess, threading
    import subprocess
    from threading import Timer
    from time import time
except ImportError as e:
    MyLogger(modulename,'FATAL',"Unable to load module %s" % e)

class Command(object):
    def __init__(self, cmd):
        self.cmd = cmd
        self.process = None

    def run(self, timeout):
        stdout = ''
        def target():
            global stdout
            print 'Thread started'
            self.process = subprocess.Popen(self.cmd, shell=True, stdout=subprocess.PIPE)
            stdout, stderr = self.process.communicate()
            print 'Thread finished'
            
        thread = threading.Thread(target=target)
        thread.start()

        thread.join(timeout)
        if thread.is_alive():
            print 'Terminating process'
            self.process.terminate()
            thread.join()
        print self.process.returncode
        return stdout

#command = Command("echo 'Process started'; sleep 2; echo 'Process finished'")
#command.run(timeout=3)
#command.run(timeout=1)

# obtain some wifi info so we can track the wifi availability
def getdata():
    global Conf
    if ('rssi' in Conf.keys()) and (not Conf['rssi']):
        return {}
    if not 'rssi' in Conf.keys():
        Conf.update({'rssi': 0, 'last': 0})
    # only once per 15 minutes
    if time()-Conf['last'] > 15*60:
        Conf['last'] = int(time())
        try:
            # p=subprocess.Popen('/sbin/iwconfig',shell=True,stdout=subprocess.PIPE)
            # stdout, stderr = p.communicate()
            # command = Command('/sbin/iwconfig')
            # stdout = command.run(timeout=4)
            kill = lambda process: process.kill()
            cmd = ['/sbin/iwconfig']
            iw = subprocess.Popen( cmd, stdout=subprocess.PIPE, stderr=subprocess.PIPE)
            my_timer = Timer(5, kill, [iw])
            try:
                my_timer.start()
                stdout, stderr = iw.communicate()
            finally:
                try:
                    my_timer.cancel()
                except:
                    pass
            ips = re.findall('[Ss]ignal\s+level=\s*(-[0-9]+)\s+dBm', stdout)
            # TO DO: may need to exclude wifi AP ip interfaces
            if len(ips):
                Conf['rssi'] = int(ips[0])
            else:
                return {}
            if ('raw' in Conf.keys()) and Conf['raw'] != None:
                conf['raw'].publish(
                    tag='rssi',
                    data="dBm=%.1f" % Conf['rssi'])
        except:
            return {}

    return {'time': int(time()),'rssi': Conf['rssi']}

# test main loop
if __name__ == '__main__':
    from time import sleep
    for cnt in range(0,10):
        timing = time()
        try:
            data = getdata()
        except Exception as e:
            print("input sensor error was raised as %s" % e)
            break
        print("Getdata returned:")
        print(data)
        timing = 30 - (time()-timing)
        if timing > 0:
            sleep(timing)
