teusH/MySense/RPi/MySense.py

#!/usr/bin/env python
# -*- coding: utf-8 -*-
# Contact Teus Hagen webmaster@behouddeparel.nl to report improvements and bugs
# 
# Copyright (C) 2017, Behoud de Parel, Teus Hagen, the Netherlands
#
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

# $Id: MySense.py,v 3.29 2018/05/31 19:48:04 teus Exp teus $

# TO DO: encrypt communication if not secured by TLS
#       and received a session token for this data session e.g. via a broker
#       Change the sensor read architecture to a row of functions per sensor type
#       and import them if needed
#       Backup data on temporaly gap in connection
#       Gspread: one Sensors sheet with rows of sensors, per sensor worksheet
#       Add a data aggregation interval window with for every output stream a subwindow.

# Reminder: adhere CIO P 2180.1 GSA rules of handling PII

# start this process where also the modules/plugins reside

# code is based on code from (https://github.com):
# MIT Clairity CEE Senior Capstone Project report V1 dd 15-05-14
# Waag Society Amsterdam Smart Citizens Lab Urban AirQ
# Citi-Sense
# opensensors.io
# Smart-Citizen-Kit
# smartemission
# polluxnzcity
# AirCastingAndroidClient
# smart-city-air-challenge (USA GOV)
""" Log data from sensors,
    e.g. Dylos, Alphasense Data, rel. huminity and temperature
    to local file in CSV format, and
    remotely: database and/or Google gspread spreadsheet format.
        On start register sensor with info to remote site.
        Broker: 2 json data files: register info data and json measurents
    Sensor info: type sensor, pollutant id, measurement unit
    Configuration: Conf global dict. Optionally: .conf file
    To do: On internet disconnect DB data will be saved localy till
        connection is established again.
"""
progname='$RCSfile: MySense.py,v $'[10:-4]
modulename = progname
__version__ = "0." + "$Revision: 3.29 $"[11:-2]
__license__ = 'GPLV4'
# try to import only those modules which are needed for a configuration
try:
    import sys
    import os
    # sys.path.append("/home/pi/quick2wire-python-api/")
    #import quick2wire.i2c as i2c
    import math
    import re
    import json
    from time import time, sleep
    import subprocess
    import datetime
    from threading import Thread
    from datetime import date
    import argparse
    import MyLogger
    try:
        import ConfigParser
    except ImportError as e:
        try:
            import configparser as ConfigParser
        except ImportError:
            sys.exit("ERROR: ConfigParser module not found.")
except ImportError:
    print("One of the import modules is missing.")
    print("Install eg. Debian: apt-get install python[3]-module_name first!")
    exit(1)

reload(sys)  
sys.setdefaultencoding('utf8')

# global data Conf is the central dictunary for global values
Conf = {}       # data dict for configuration variables, values and static values

# ==========================================================================
# configuration
# ==========================================================================
# allowed output/output channels can be switched on or off
# from configuration file or command argument options
# INPUT/OUTPUT)_I IO needs internet connectivity
# all are plugins declared via the init/config file
OUTPUTS_I  = []         # output using internet
OUTPUTS    = []         # local output channels
INPUTS_I   = []         # inputs from internet (disables other input channels)
INPUTS     = []         # local input channels
INTERVAL   = 60*60      # dflt main loop interval in seconds
RAW        = False      # display raw measurements for all sensors
LOCAL      = False      # no output via internet connectivity

Archive = {}            # archived queues per channel, has links to heap
Heap = {}               # heap for storing data indexed by Archive
HeapId = -1             # current heap index number
HeapSze = 100000        # max of bytes in heap

def defFields(name,conf):
    if not 'module' in conf.keys():
        MyLogger.log(modulename,"WARNING", 'no module for this sensor %s defined' % name)
        return
    if not 'fields' in conf.keys():
        if not 'fields' in conf['module'].Conf.keys():
            return
        nr = len(conf['module'].Conf['fields'])
    else: nr = len(conf['fields'].split(','))
    for key in ['fields','units','calibrations','serials','dataFlds','omits']:
        if not key in conf['module'].Conf.keys(): continue
        if not key in conf.keys():
            new = conf['module'].Conf[key] 
        else: new = conf[key]
        conf[key] = conf['module'].Conf[key]
        if type(new) is str:
            if not key in ['calibrations']:
                while new.find(', ') >= 0:
                    new = new.replace(', ',',')
                new = new.split(',')
            else:
                try:
                    new = json.loads(new)
                    if not type(new) is list: raise TypeError
                except:
                    MyLogger.log(modulename,'FATAL',"Sensor %s %s configuration error" % (name,key))
        elif not type(new) is list: new = []
        if not key in ['dataFlds']:
            while len(new) > nr: new.pop() 
            while len(new) < nr:
                if key == 'calibrations': new.append([0,1])
                else: new.append('unknown')
        #conf[key][0:len(new)] = new
        conf[key] = new

# parse the program configuration (ini) file progname.conf
#       or uppercase progname as defined by environment variable
# Parse configuration
def read_configuration():
    """ read the configuration details (options per plugin) from init file
    """
    global Conf, OUTPUTS, OUTPUTS_I, INPUTS, INPUTS_I, progname
    config = ConfigParser.RawConfigParser()
    initFile = os.getenv(progname.replace('.py','').upper())
    if not initFile:
        initFile = progname.replace('.py','') + '.conf'
    if os.path.isfile(initFile):
        try:
            config.read(initFile)
        except:
            sys.exit("Config/init file %s has configuration errors: %s" % (initFile,sys.exc_info()[1]))
    else:
        config = None
        MyLogger.log(modulename,'WARNING',"No configuration file %s.conf found." % (progname.replace('.py','')))

    if config:
        for key in config.sections():
            if not key in Conf.keys():
                Conf[key] = {}
            options = []
            if os.path.isfile('My'+key.upper()+'.pyc') or os.path.isfile('My'+key.upper()+'.py'):
                Conf[key]['import'] = 'My'+key.upper()
                Conf[key]['module'] = False
                try:
                    Conf[key]['module'] = __import__(Conf[key]['import'])
                    if not CheckVersion(Conf[key]['module'].__version__):
                        MyLogger.log(modulename,'FATAL',"Module %s version is not compatible." % key)
                except NameError:
                    MyLogger.log(modulename,'FATAL',"Module %s has no version defined." % key)
                    Conf[key]['module'] = False
                except ImportError:
                    MyLogger.log(modulename,'WARNING',"Unable to install plugin My%s. Try running the plugin for the failure message." % key.upper())
                    Conf[key]['module'] = False
                if not Conf[key]['module']:
                    del Conf[key]
                else:
                    options = Conf[key]['module'].__options__
                    for InOut in ['input','output']:
                        if InOut in options:
                            #MyLogger.log(modulename,'DEBUG',"Importing %s plugin: %s" % (InOut,Conf[key]['import']))
                            Conf[key][InOut] = False
                            if (InOut == 'input') and (not InOut in INPUTS+INPUTS_I):
                                if 'hostname' in options:
                                    INPUTS_I.append(key)
                                else:
                                    INPUTS.append(key)
                            if (InOut == 'output') and (not InOut in OUTPUTS+OUTPUTS_I):
                                if 'hostname' in options:
                                    OUTPUTS_I.append(key)
                                else:
                                    OUTPUTS.append(key)
                    # end for InOut
            else:
                if key == 'id':
                    options = ['project','serial','geolocation','label','description','street','village','province','municipality']
                elif key == 'process':
                    options = ['home','pid','user','group','start_dir','interval','raw']
                elif key == 'logging':
                    options = ['level','file']
		elif key == 'raw':
		    options = ['raw','hostname','user','password','file','database']
            #MyLogger.log(modulename,'DEBUG','Configuring module %s: options %s.' % (key,', '.join(config.options(key))) )
            # get options allowed to be redefined by the plugin
            for opt in config.options(key):
                if not opt in options: continue
                try:
                    Conf[key][opt.lower()] = config.get(key,opt)
                    if opt in ['input','output','raw','sync']:
                        Conf[key][opt.lower()] = config.getboolean(key,opt)
                    elif opt.lower() in ('port','sample','interval','bufsize','is_stable'):
                        if re.compile("^[0-9]+$").match(Conf[key][opt.lower()]):
                            Conf[key][opt.lower()] = int(Conf[key][opt.lower()])
                    elif (opt.lower() == 'level'):
                        Conf[key][opt.lower()] = Conf[key][opt.lower()].upper()
                    else:
                        Conf[key][opt.lower()] = config.get(key,opt)
                except:
                    pass
            if 'fields' in options:
                defFields(key,Conf[key])
            # end if
                
    if config == None:
        return

    for io in ['input','output']:
        if io == 'input': array = INPUTS+INPUTS_I
        else: array = OUTPUTS+OUTPUTS_I
        Conf[io + 's'] = []          # ######    different output possibilities
        for Nme in array:
            if Conf[Nme][io]:
                Conf[io+'s'].append(Nme)

    # if root change effective user/group
    try:
        if (os.geteuid() == 0) and ('user' in Conf['process'].keys()):
            import pwd
            Conf['process']['uid'] = pwd.getpwname(Conf['process']['user'])[2]
    except:
        MyLogger.show_error()
    try:
        if (os.getegid() == 0) and ('group' in Conf['process'].keys()):
            import grp
            Conf['process']['gid'] = grp.getgrnam(Conf['process']['group'])[2]
    except:
        MyLogger.show_error()
    return True

def get_serial():
    """ get serial number (cpu S/N) for this sensor node
    """
    try:        # try serial cpu number
        p=subprocess.Popen('cat /proc/cpuinfo',shell=True,stdout=subprocess.PIPE)
        stdout, stderr = p.communicate()
        ips = re.findall('Serial\s+:\s*([A-Za-z0-9]+)', stdout)
        for item in ips:
            return item.lstrip('0')
    except:
        pass
    try:
        p=subprocess.Popen('/sbin/ifconfig',shell=True,stdout=subprocess.PIPE)
        stdout, stderr = p.communicate()
        ips = re.findall('HWaddr\s+([0-9a-f]{2}(:[0-9a-f]{2}){5})', stdout)
        for item in ips:
            return item[0].replace(':','')
    except:
        pass
    return 'undefined'

# ==================================================================
# configuration defaults definitions and values: init Conf and update from conf file
# ==================================================================
# TO DO: push all input/output routines in a class and load dynamically
def get_config():
    """ Initialize Conf dictionary """
    global Conf, __version__
    Conf = {}
    Conf['process'] = {
        'home': '/var/tmp/',   # deamon process home directory, default: current
        'pid': '/var/tmp/',    # deamon pid file directory
        'user': None,          # deamon user ID
        'group': None,         # deamon grgoup ID, pref: dailout
        'start_dir': os.getcwd() + '/' # remember where we started this process
    }
    Conf['id'] = {
        'project': 'undefined',    # project identification
        'serial': get_serial(),    # serial number of this sensor 
        'geolocation': None, # lat,long, and altitude in meters
        'version': __version__,  # data version
    }
    Conf['logging'] = {
        #'level': 'NOTSET',   # verbosity
        'level': 'ATTENT',   # verbosity
        'file': '/dev/stderr', # /var/log/IoS/IoS.log Unix log file
    }
    # communication mechanism to internet land
    Conf['internet'] = {
        'import': 'MyInternet', # the plugin for internet connectivity
        'module': None,         # last time connected to internet
        'connected': None       # connected to internet?
    }
    # rawmeasurements values to be send to InFlux server or file
    # configuration used by MyRaw.py module if RAW is enabled/True
    Conf['raw'] = {
        'raw': False,           # raw measurement output enabled?
        'hostname': None,       # InFlux server
        'port': 8086,           # InFlux port number
        'user': None,           # credited user name
        'password': None,
        'file': None,           # local file name for records
        'database': None,       # identifier for database name dflt: <proj>_<serial>
    }
    # default loaded modules
    Conf['console'] = {
        'output': False,
        'import': 'MyConsole',
        'module' : None,
        'file': '/dev/stdout',
    }
    # defaults for output modes: only console output is enabled
    if not 'console' in OUTPUTS:
        OUTPUTS.append('console')
    # Configuration or init file handling
    if not read_configuration():
       MyLogger.log(modulename,'WARNING',"Init/configuration skipped.")

# ===================================================================
# Commandline arguments parsing
# ===================================================================
def get_arguments():
    """ Command line argument roll in """
    global Conf, progname, INTERVAL, HeapSze
    parser = argparse.ArgumentParser(prog=progname, description='Sensor datalogger - Behoud de Parel\nCommand arguments overwrite optional config file.', epilog="Copyright (c) Behoud de Parel\nAnyone may use it freely under the 'GNU GPL V4' license.")
    parser.add_argument("-d", "--debug", help="List of input sensors and show the raw sensor values.", default="")
    parser.add_argument("-D", "--DYLOS", help="Read pm sensor input from an input file instead. Debugging simulation.")
    parser.add_argument("-i", "--input", help="Input sensor(s), comma separated list of %s" % ','.join(INPUTS+INPUTS_I), default="%s" % ','.join(Conf['inputs']))
    parser.add_argument("-o", "--output", help="Output mode(s), comma separated list of %s" % ','.join(OUTPUTS+OUTPUTS_I), default="%s" % ','.join(Conf['outputs']))
    parser.add_argument("-l", "--level", help="Be less verbose, default='%s'" % Conf['logging']['level'], default=Conf['logging']['level'], type=str.upper, choices=MyLogger.log_levels)
    parser.add_argument("-G", "--geolocation", help="Sensor node geolocation (latitude,longitude), default='%s'" % Conf['id']['geolocation'], default=Conf['id']['geolocation'])
    parser.add_argument("-I", "--interval", help="Sensor read cycle interval in minutes, default='%d'" % (INTERVAL/60), default=(INTERVAL/60))
    parser.add_argument("-M", "--memory", help="Allocated memory space in Kbytes for queuing data, default='%d'" % (HeapSze/1000), default=(HeapSze/1000))
    parser.add_argument("-P", "--project", help="Project XYZ, default='%s'" % Conf['id']['project'], default=Conf['id']['project'], choices=['BdP','VW'])
    parser.add_argument("-R", "--raw", help="Display raw measurements of all sensors on stdout in InFlux http timestamped format (calibration purposes), default=False", default=False, dest='raw', action='store_true')
    parser.add_argument("--local", help="Only local output, no output via internet, default=use internet if configured", action='store_true', default=False, dest='local')
    parser.add_argument("-S", "--node", help="Sensor node serial number, default='%s'" % Conf['id']['serial'], default=Conf['id']['serial'])
    parser.add_argument("process", help="Process start/stop/status. Default: interactive", default='interactive', choices=['interactive','start','stop','status'], nargs='?')
    # overwrite argument settings into configuration
    return parser.parse_args()

# roll in the definition from environment eg passwords
def from_env(name):
    """ hostname, user credentials can (should) be defined from environment as
        <section name><host|user|pass> e.g. DBHOST, DBUSER, DBPASS
    """
    global Conf
    for credit in ['hostname','user','password']:
        if not credit in Conf[name].keys():
            Conf[name][credit] = None
        try:
            Conf[name][credit] = os.getenv(name.upper()+credit[0:4].upper(),Conf[name][credit])
        except:
            pass
    return True

# =================================================================
# Overwrite configuration values with argument values
# =================================================================
def integrate_options():
    """ Command line arguments overwrite configuration option values
    """
    global Conf, OUTPUTS, OUTPUTS_I, INPUTS, INPUTS_I, INTERVAL, RAW, LOCAL
    
    cmd_args = get_arguments()

    Conf['id']['project'] = cmd_args.project
    Conf['id']['serial'] = cmd_args.node
    Conf['id']['geolocation'] = cmd_args.geolocation
    if 'interval' in Conf['process'].keys():
        INTERVAL = int(Conf['process']['interval']) * 60
        del(Conf['process']['interval'])
    if int(cmd_args.interval) != 60:
        INTERVAL = int(cmd_args.interval) * 60
    try:
        LOCAL = cmd_args.local
    except:
        LOCAL = False
    HeapSze = int(cmd_args.memory) * 1000
    RAW = False; RAWok = True
    if Conf['raw']['file'] != None:
        RAWok = True
    else:
        for key in ['hostname','user','password']:
            if Conf['raw'][key] == None: RAWok = False
    if RAWok:
        if 'raw' in Conf['process'].keys():
            RAW = Conf['process']['raw']
            del(Conf['process']['raw'])
        if bool(cmd_args.raw): RAW = True
    elif 'import' in Conf['raw'].keys():
        del Conf['raw']['import']

    Conf['outputs'] = []
    # TO DO: enable MQTT to be used on output as well on input
    for Nme in OUTPUTS+OUTPUTS_I:
        # different output modes
        try:
            Conf[Nme]['output'] = cmd_args.output.rindex(Nme) >= 0
        except:
            Conf[Nme]['output'] = False
        if LOCAL and (Nme in OUTPUTS_I) and ('hostname' in Conf[Nme].keys()):
            Conf[Nme]['output'] = False  # turn external output off
        if Conf[Nme]['output']:
            if not Nme in Conf['outputs']:
                Conf['outputs'].append(Nme)
            # database credits and configurations
            if Nme in OUTPUTS_I:
                from_env(Nme)

    if 'db' in Conf['outputs']:
        try:
            Conf['db']['database']= os.getenv('DB', Conf['db']['database'])
        except:
            pass
                
    if not len(Conf['outputs']):
        if not 'console' in Conf.keys():
            Conf['console'] = { 'import': 'MyCONSOLE', 'type': None}
        Conf['console']['output'] = True
        if not Nme in Conf['outputs']:
            Conf['outputs'].append('console')
        MyLogger.log(modulename,'WARNING',"No output channels defined. Enabled output to console.")

    # TO DO: enable MQTT to be used on output as well on input
    Conf['inputs'] = []; RawOnce = False
    for Nme in INPUTS+INPUTS_I:
        # different input sensors
        try:
            Conf[Nme]['input'] = cmd_args.input.rindex(Nme) >= 0
        except:
            Conf[Nme]['input'] = False
        if Conf[Nme]['input']:
            if not Nme in Conf['inputs']:
                Conf['inputs'].append(Nme)
            if Nme in INPUTS_I:
                from_env(Nme)
            elif RAW:
                Conf[Nme]['raw'] = True
            elif (not RAWok) and ((not 'raw' in Conf[Nme].keys()) or(not Conf[Nme]['raw'])):
                Conf[Nme]['raw'] = False
            if ('raw' in Conf[Nme].keys()) and Conf[Nme]['raw']: RawOnce = True
        try:    # allow to display raw sensor values from a sensor thread
            Conf[Nme]['debug'] = cmd_args.debug.rindex(Nme) >= 0
        except:
            Conf[Nme]['debug'] = False

    if not RawOnce:
        Conf['raw'] = None
    else:
        Nme = 'raw'
        try:
            Conf[Nme]['module'] = __import__(Conf[Nme]['import'])
            if not CheckVersion(Conf[Nme]['module'].__version__):
                MyLogger.log(modulename,'FATAL',"Module %s version is not compatible." % Nme)
        except NameError:
            MyLogger.log(modulename,'FATAL',"Module %s has no version defined." % Nme)
        except ImportError:
            MyLogger.log(modulename,'FATAL',"Unable to import module %s" % Conf[Nme]['import'])
    if 'dylos' in Conf['inputs']:
        if ('usbPID' in Conf['dylos'].keys()):
            if re.compile("^[0-9a-zA-Z_,]{7,}").match(Conf['dylos']['usbPID']) == None:
                sys.exit(Conf['dylos']['usbPID'] + " is not a USB producer name.")
        if cmd_args.DYLOS:
            Conf['dylos'].update({ 'input': True, 'sync': True, 'file': cmd_args.DYLOS })

    if not len(Conf['inputs']):
        MyLogger.log(modulename,'FATAL',"No sensor input is defined.")

    Conf['logging']['level']    = cmd_args.level.upper()     # how much we log
    return cmd_args.process

# show the intension of this process
def show_startup():
    """ On startup log configuration details """
    global Conf, progname, __version__, INTERVAL, RAW, INPUTS
    MyLogger.log(modulename,'INFO',"Project: %s, Serial_ID=%s" % (Conf['id']['project'],Conf['id']['serial']))
    MyLogger.log(modulename,'ATTENT',"%s Started Sensor processing: %s Version:%s" % (datetime.datetime.strftime(datetime.datetime.today(), "%Y-%m-%d %H:%M:%S " ), progname, __version__))
    MyLogger.log(modulename,'DEBUG',"Control-C to abort")
    MyLogger.log(modulename,'DEBUG',"Engine: Python Version %s.%s.%s\n" % sys.version_info[:3])
    MyLogger.log(modulename,'DEBUG',"Startup parameters:")
    for item in ('project','serial','geolocation'):
        if (item in Conf['id'].keys()) and (Conf['id'][item] != None):
            MyLogger.log(modulename,'ATTENT',"\t %s:\t%s" % (item,Conf['id'][item]))
    MyLogger.log(modulename,'ATTENT',"\t main loop interval:\t%d minutes" % (INTERVAL/60))

    MyLogger.log(modulename,'INFO',"Available INPUT SENSORS: %s" % ', '.join(INPUTS+INPUTS_I))
    for Sensor in INPUTS+INPUTS_I:
        if (not Sensor in Conf.keys()) or (not 'input' in Conf[Sensor].keys()):
            MyLogger.log(modulename,'INFO',"Sensor %s not installed." % Sensor)
            continue
        if Conf[Sensor]['input']:
            MyLogger.log(modulename,'ATTENT',"Sensor %s (plugin %s) is switched ON." % (Sensor,Conf[Sensor]['import']))
            for Opt in Conf[Sensor].keys():
                if Opt == 'input' or Opt == 'module' or Opt[0:3] == 'raw': continue
                MyLogger.log(modulename,'INFO',"\t%s:\t%s" % (Opt,Conf[Sensor][Opt]))
        else:
            MyLogger.log(modulename,'INFO',"Sensor %s (plugin %s) is switched OFF." % (Sensor,Conf[Sensor]['import']))
                # continue
            for Opt in Conf[Sensor].keys():
                if Opt == 'input' or Opt == 'module': continue
                MyLogger.log(modulename,'DEBUG',"\t%s:\t%s" % (Opt,Conf[Sensor][Opt]))

    MyLogger.log(modulename,'INFO',"Available OUTPUT CHANNELS: %s" % ', '.join(OUTPUTS+OUTPUTS_I))
    for Mode in OUTPUTS+OUTPUTS_I:
        if Conf[Mode]['output']:
            MyLogger.log(modulename,'ATTENT',"Ouput channel %s (plugin %s) is ENABLED." % (Mode,Conf[Mode]['import']))
            for Attr in Conf[Mode].keys():
                if (Attr != 'output') and (Attr != 'password') and (Attr != 'module'):
                    MyLogger.log(modulename,'INFO',"\t%s:\t%s" % (Attr,Conf[Mode][Attr]))
        else:
           MyLogger.log(modulename,'DEBUG',"Ouput channel %s (plugin %s) is DISABLED, attributes:" % (Mode,Conf[Mode]['import']))
           # continue
           for Attr in Conf[Mode].keys():
               if (Attr != 'output') and (Attr != 'password') and (Attr != 'module'):
                   MyLogger.log(modulename,'DEBUG',"\t%s:\t%s" % (Attr,Conf[Mode][Attr]))
    
# ===========================================================
# Routines needed to run as UNIX deamon
# ===========================================================

def delpid():
    global pidfile
    os.remove(pidfile)

def pid_kill(pidfile):
    pid = int(os.read(fd, 4096))
    os.lseek(fd, 0, os.SEEK_SET)

    try:
        os.kill(pid, SIGTERM)
        sleep(0.1)
    except OSError as err:
        err = str(err)
        if err.find("No such process") > 0:
            if os.path.exists(pidfile):
                os.remove(pidfile)
        else:
            sys.exit(str(err))

    if pid_is_running():
        sys.exit("Failed to kill %d" % pid)

def pid_is_running(pidfile):
    try:
        fd = os.open(pidfile, os.O_RDONLY)
    except:
        return False
    contents = os.read(fd, 4096)
    os.lseek(fd, 0, os.SEEK_SET)
    if not contents:
        return False
    os.close(fd)

    p = subprocess.Popen(["ps", "-o", "comm", "-p", str(int(contents))],
            stdout=subprocess.PIPE, stderr=subprocess.PIPE)
    stdout, stderr = p.communicate()
    if stdout == "COMM\n":
        return False
    if 'python' in stdout[stdout.find("\n")+1:]:
        return int(contents)

    return False

def deamon_daemonize(pidfile):
    global progname
    try:
        pid = os.fork()
        if pid > 0:
            # exit first child
            sys.exit(0)
    except OSError as err:
        sys.stderr.write('fork #1 failed: {0}\n'.format(err))
        sys.exit(1)
    # decouple from parent environment
    os.setsid()
    os.umask(0)
    # do second fork
    try:
        pid = os.fork()
        if pid > 0:
            # exit from second parent
            sys.exit(0)
    except OSError as err:
        sys.stderr.write('fork #2 failed: {0}\n'.format(err))
        sys.exit(1)
    # write pidfile
    atexit.register(delpid)
    pid = str(os.getpid())
    try:
        fd = os.open(pidfile, os.O_CREAT | os.O_RDWR)
    except IOError as e:
        sys.exit("Process already running? Failed to open pidfile %s: %s" % (progname, str(e)))
    assert not fcntl.flock(fd, fcntl.LOCK_EX)
    os.ftruncate(fd, 0)
    os.write(fd, "%d\n" % int(pid))
    os.fsync(fd)
    # redirect standard file descriptors
    sys.stdout.flush()
    sys.stderr.flush()
    si = open(os.devnull, 'r')
    so = open(os.devnull, 'a+')
    se = open(os.devnull, 'a+')
    os.dup2(si.fileno(), sys.stdin.fileno())
    os.dup2(so.fileno(), sys.stdout.fileno())
    os.dup2(se.fileno(), sys.stderr.fileno())

def deamon_detach(pidfile):
    if pidfile == None:
        sys.exit("Cannot start deamon: no pid file defined.")
    # Check for a pidfile to see if the daemon already runs
    if pid_is_running(pidfile):
        sys.exit("Daemon already running.")

    # Start the daemon
    deamon_daemonize(pidfile)

def deamon_stop(pidfile):
    if pidfile == None:
        sys.exit("Cannot stop deamon: no pid file defined.")
    # Get the pid from the pidfile
    pid = pid_is_running(pidfile)
    if not pid:
        sys.stderr.write("Daemon not running.\n")
        exit(0)

    # Try killing the daemon process
    error = os.kill(pid,SIGTERM)
    if error:
        sys.exit(error)

def deamon_status(pidfile):
    global progname
    if pid_is_running(pidfile):
        sys.stderr.write("%s is running.\n" % progname)
    else:
        sys.stderr.write("%s is NOT running.\n" % progname)

# Define Global Variables

# Archive data when Internet connectivity failed
# throw away oldest first of this channel
# or throw away object from another channel
def HeapCleanup(space):
    global Heap, HeapSze, Archive
    while sys.getsizeof(Heap) > HeapSze-space:
        # search largest channel
        channel = None
        for key in Archive.keys():
            if not channel: channel = key
            if len(Archive[key]) > len(Archive[channel]): channel = key
        if not channel: return False
        heapPop(Archive[channel][0]['ident'])
        heapPop(Archive[channel][0]['data'])
        Archive[channel].pop(0)
    return True

def heapAppend(data):
    global Heap, HeapId
    for key in Heap.keys():
        if Heap[key]['data'] == data:
            Heap[key]['refs'] += 1
            return int(key)
    HeapId += 1
    Heap['%d' % HeapId] = { 'refs': 1, 'data': data }
    return HeapId

def heapPop(Id):
    global Heap
    if not ('%d' % Id) in Heap.keys():
        return {}
    Sid = '%d' % Id
    Heap[Sid]['refs'] -= 1
    if not Heap[Sid]['refs']: del Heap[Sid]
    return

def heapRef(Id):
    global Heap
    if not ('%d' % Id) in Heap.keys():
        return {}
    return Heap['%d' % Id]['data']

# get some saved data from archive
def refQueue(channel):
    global Archive
    if len(Archive[channel]):
        rts = {
            'ident': heapRef(Archive[channel][0]['ident']),
            'data': heapRef(Archive[channel][0]['data'])
            }
        return rts
    return {}

# removes oldest data tuple from channle queue
def deQueue(channel):
    global Archive
    if len(Archive[channel]):
        heapPop(Archive[channel][0]['ident'])
        heapPop(Archive[channel][0]['data'])
        Archive[channel].pop(0)
        return True
    return False

# push ident and data dicts to the channel queue
def Queue(channels,ident,data):
    """ Each output channel has a queue. identification and data values are
        pushed to a heap.
        Queue routine pushes data tuple to all channel queues.
        refQueue returns the oldest data tuple.
        deQueue removes oldest data tuple for a channel
    """
    global Archive, Heap
    if (not len(ident)) and (len(data) <= 1): return False
    Channels = channels
    if not type(Channels) is list: Channels = [Channels]
    if not len(Channels): return False
    if not HeapCleanup(sys.getsizeof(ident)+sys.getsizeof(data)):
        MySyslog.log('WARNING','Archived space exhausted, skipping data')
        # TO DO: use picle to collect data into filesystem
        Archive = {}
        Heap = {}
    id_nr = heapAppend(ident) ; da_nr = heapAppend(data)
    First = True
    for Chan in Channels:
        if not First:
            Heap['%d' % id_nr]['refs'] += 1
            Heap['%d' % da_nr]['refs'] += 1
        else:
            First = False
        if not Chan in Archive.keys():
            Archive[Chan] = []
        Archive[Chan].append( {'ident': id_nr, 'data': da_nr} )
    return True

# maintain meteo values, correct with last seen
def updateMeteo(old, new):
    for key in new.keys():
        if new[key] == None: continue
        for name in ['temp','rh','rv','hum','press']:
          if key.find(name) >= 0:
            if name in ['rv','hum']: name = 'rh'
            if name in old.keys():
                if type(old[name]) is int:  old[name] = round(new[key],2)
                else: old[name] = round((old[name]+new[key])/2.0,2)
                break
    return True

# ================ List of Global Variables to be stored in DB
# next has keys as: time, dylos[4], temp, humidity, asense[8]
# ================ End of Variable List

# =================================================================
# read forever sensor data and publicise the results
# =================================================================
# compile the sensors values telegram and output the telegram to the world
# TO DO: multiple input channels can block each other: select/multi threading
def sensorread():
    """ Main routine: read input values from plugins (threaded)
        and print collected measurements and identication to output channels
        Queue output if internet connectivity failed.
    """
    #Continuously loop collecting all data
    global Conf, INTERVAL
    if not 'fields' in Conf['id'].keys():
        Conf['id']['fields'] = ['time']
        Conf['id']['units'] = ['s']
    Conf['id']['types'] = ['time']
    data = { 'time': 0 }
    # default meteo data for sensor corrections, corrected as soon as seen
    meteo = { 'temp': 25, 'press': 1000, 'rh': 70 }
    first = True
    local = True
    start = 0
    # for now if input vai internet is defined, local sensor input is disabled
    # TO DO: have 2 threads: one for input and one (main thread) for output
    # TO DO: handle multiple input channels with select and threads
    while True:
        if not len(Conf['outputs']):
            MyLogger.log(modulename,'FATAL',"No output available any more. Abort.")
        data = {'time': data['time']}
        ident = Conf['id']
        local = True
        gotData = False
        t_cnt = 0 ; t_time = 0 ; start += 1
        for Sensor in Conf['inputs']:
            if not Conf[Sensor]['input']:
                continue
            try:
                if start == 1:
                    MyLogger.log(modulename,'INFO','Starting up sensor %s' % Sensor)
                    if ('display' in Conf['outputs']) and Conf['display']['output']:
                      try:
                        text = { 'text': ["Starting %s" % Sensor] }
                        Conf['display']['module'].publish(
                            ident=ident,
                            data=text
                        )
                      except: pass
                else:
                    MyLogger.log(modulename,'DEBUG','Collecting data from sensor %s' % Sensor)
                if Sensor in ['alphasense']:
                    sensed = Conf[Sensor]['module'].getdata(meteo=meteo)
                else:
                    sensed = Conf[Sensor]['module'].getdata()
                if (not type(sensed) is dict) or (not len(sensed)):
                    continue
                if 'hostname' in Conf[Sensor].keys():
                    # if len(Conf['inputs'])-1:
                    ident = {}
                    if 'register' in sensed.keys():
                        ident = sensed['register']
                    if 'data' in sensed.keys():
                        data.update(sensed['data'])
                        gotData = True
                    local = False
                    break
                if ('time' in sensed.keys()) and sensed['time']:
                    t_cnt += 1
                    t_time += sensed['time']                       
                for key in sensed.keys():
                    if (not type(sensed[key]) is str):
                        if (sensed[key] != None)  and math.isnan(sensed[key]):
                            MyLogger.log(modulename,'ATTENT','Sensor %s has NaN value.' % Sensor)
                            sensed[key] = None
                    if key == 'time': continue
                    if (key in data.keys()) and (sensed[key] != None):
                        # some sensor key are the same, except only 2 of them
                        # examples are meteo values eg temp, humidity
                        MyLogger.log(modulename,'DEBUG',"There is more then one %s in data stream: collected: %5.1f, new %5.1f" % (key,data[key],sensed[key]))
                        if (type(data[key]) is int) and (type(sensed[key]) is int):
                            sensed[key] = int((sensed[key]+data[key]+0.5)/2)
                        else:
                            sensed[key] = (sensed[key]+data[key])/2
                data.update(sensed)
                updateMeteo(meteo,sensed)
                gotData = True
            except KeyboardInterrupt:
                exit(0)
            except (Exception) as error:
                MyLogger.log(modulename,'ERROR',"%s Error : %s. Disabled." % (Sensor,error))
                Conf['inputs'].remove(Sensor)
                if not len(Conf['inputs']):
                    MyLogger.log(modulename,'FATAL',"No input sensors active any more. Exiting.")
                continue
            if first and local:
                for i in range(0,len(Conf[Sensor]['module'].Conf['fields'])):
                    if not Conf[Sensor]['module'].Conf['fields'][i] in Conf['id']['fields']:
                        Conf['id']['fields'].append(Conf[Sensor]['module'].Conf['fields'][i])
                        Conf['id']['units'].append(Conf[Sensor]['module'].Conf['units'][i])
                        Type = None
                        if ('type' in Conf[Sensor]['module'].Conf.keys()) and (Conf[Sensor]['module'].Conf['type'] != None):
                            Type = Conf[Sensor]['module'].Conf['type']
                        if Sensor in ('gps','rssi',None): Type = format(Sensor)
                        Conf['id']['types'].append(format(Type).replace(' ','_'))
                if Sensor == 'gps':
                    if ((not 'geolocation' in Conf['id'].keys())) or \
                        (Conf['id']['geolocation'] == None):
                        Conf['id']['geolocation'] = data["geolocation"]
                if (Sensor == 'rssi') and ('rssi' in data.keys()) and data['rssi']:
                    if ('description' in Conf['id'].keys()) and Conf['id']['description']:
                        Conf['id']['description'] += " wifi signal level: %d" % data['rssi']
                    else:
                        Conf['id']['description'] = " wifi signal level: %d" % data['rssi']
        first = False

        if local:
            data['time'] = int(time())   # datetime.datetime.now()
            if t_cnt and t_time:
                data['time'] = int(t_time/t_cnt)
            # ident = Conf['id']
        elif not len(ident):
            continue
        elif (not 'project' in ident.keys()) or (not 'serial' in ident.keys()):
            continue
        # TO DO: push inputs into an array with idents and data and publish them
        # next have threads to fill and empty the buffer supervised with a semaphore
        
        if gotData:      # data collected?
            # queue for all channels the data tuple
            Queue(Conf['outputs'],ident,data)
            for Out in Conf['outputs']:
                if (not Conf[Out]['output']) or (not 'module' in Conf[Out].keys()):
                    deQueue(Out)
                    continue
                # TO DO: do this async
                while True:
                    rec = refQueue(Out) # record should have more as rec['data']['time']
                    if (not len(rec)) or (not 'data' in rec.keys()) or (len(rec['data']) <= 1):
                        break
                    try:
                        Conf[Out]['module'].publish(
                            ident = rec['ident'],
                            data = rec['data'],
                            internet = Conf['internet']
                        )
                        deQueue(Out)
                    except IOError:
                        if 'fd' in Conf[Out]['module'].Conf.keys():
                            if (Conf[Out]['module'].Conf['fd'] != None) and (Conf[Out]['module'].Conf['fd']):
                                # temporary connectivity problem
                                if type(Conf[Out]['module'].Conf['fd']) is file:
                                    close(Conf[Out]['module'].Conf['fd'])     # try again later
                                Conf[Out]['module'].Conf['fd'] = 0
                                MyLogger.log(modulename,'WARNING','Publishing for %s has temporary failure. Try again.' % Out)
                                break
                            else:
                                while(deQueue(Out)): continue
                                Conf['outputs'].remove(Out)
                                MyLogger.log(modulename,'ERROR','Publishing for %s permanent error.' % Out)
                                break
                    except StandardError as err:
                        if not 'ErrorCount' in Conf[Out].keys():
                            Conf[Out]['ErrorCount'] = 0
                        Conf[Out]['ErrorCount'] += 1
                        MyLogger.log(modulename,'ERROR',"Publish via %s failed with error: %s" % (Out,err))
                        if Conf[Out]['ErrorCount'] < 10:
                            deQueue(Out)        # throw this output record away
                            continue
                        MyLogger.log(modulename,'ERROR',"Publish via %s is too much failing. Skipping this output stream." % Out)
                        while(deQueue(Out)): continue
                        Conf['outputs'].remove(Out)
                        Conf[Out]['module'].Conf['output'] = False
                        break
        if local:
            if INTERVAL - (time() - data['time']) > 0:    # limit to once per minute
                sleep(INTERVAL-(time()-data['time'])) 
        local = True
    return False

# make sure plugins are compatible
def CheckVersion(version):
    global __version__
    if version == None:
        return False
    mod = re.split('\.',version, maxsplit = 3)
    mine = re.split('\.',__version__, maxsplit = 3)
    if len(mod) < 2:
        return False
    if (int(mod[0]) != int(mine[0])):
        return False
    if (int(mod[1]) > int(mine[1])):
        return False
    return True

# try to save some memory by freeing memory of unused plugins
def FreeConfMem(*IO):
    global Conf
    for io in IO:
        for key in Conf.keys():
            if not type(Conf[key]) is dict:
                continue
            if (io in Conf[key].keys()) and (not Conf[key][io]):
                # the unload in python does not really free much mem
                if 'module' in Conf[key].keys():
                    try:
                        del Conf[key]['module']
                        sys.modules.pop(Conf[key]['import'])
                    except:
                        pass
                del Conf[key]
                MyLogger.log(modulename,'DEBUG',"Deleted plugin My%s (unused)." % key.upper())
    return True

# load optional configured input/output module plugins
# clean up the configuration
def LoadWrapup(io):
    global Conf, INPUTS_I, OUTPUTS_I
    def Review(io,internet):     # allow only local plugings or remote plugins
        global Conf
        net = []
        notNet = []
        for i in range(0,len(Conf[io])):
            if ('hostname' in Conf[Conf[io][i]].keys()) and Conf[Conf[io][i]]['hostname']:
                net.append(Conf[io][i])
            else:
                notNet.append(Conf[io][i])
        if internet:
            return net
        else:
            return notNet
            
    if io == 'inputs':
        inet = Review(io,True)
        if len(inet): # found input channel from internet
            for Nme in Review(io,False):
                Conf[Nme]['input'] = False  # turn local sensors off
            Conf['inputs'] = inet
    for Nme in Conf[io]:
        if (not Conf[Nme][io.replace('s','')]) or (not 'import' in Conf[Nme].keys()):
            continue
        if Nme in INPUTS_I + OUTPUTS_I: # need internet connectivity?
            try:
                if not Conf['internet']['module']:      # only once
                    MyLogger.log(modulename,'DEBUG',"Importing module: %s" % Conf['internet']['import'])
                    Conf['internet']['module'] = __import__(Conf['internet']['import'])
                    Conf['internet']['connected']=Conf['internet']['module'].internet(Conf['id'])
            except:
                MyLogger.log(modulename,'FATAL',"Unable to install internet access.")
        if ('import' in Conf[Nme].keys()) and (not 'module' in Conf[Nme].keys()):
            MyLogger.log(modulename,'DEBUG',"Importing %s plugin: %s" % (io,Conf[Nme]['import']))
            try:
                Conf[Nme]['module'] = __import__(Conf[Nme]['import'])
                if not CheckVersion(Conf[Nme]['module'].__version__):
                    MyLogger.log(modulename,'FATAL',"Module %s version is not compatible." % Nme)
            except NameError:
                MyLogger.log(modulename,'FATAL',"Module %s has no version defined." % Nme)
            except ImportError:
                MyLogger.log(modulename,'FATAL',"Unable to import input/output module %s" % Conf[Nme]['import'])
        # handle options for the module
        if ('module' in Conf[Nme].keys()):
            Conf[Nme]['module'].Conf.update(Conf[Nme])  # set module attributes

def ConfRawModule(inputs):
    ''' Configure and initialize the RAW module '''
    # to do: put this code into a class module
    global Conf
    RawSenses = []
    for item in inputs:
        if Conf['raw'] == None: # clean up raw refs
            if 'raw' in Conf[item].keys(): del Conf[item]['raw']
            if 'raw' in Conf[item]['module'].Conf.keys():
                del Conf[item]['module'].Conf['raw']
            continue
        # raw module configuration (to do: put the code in a class module)
        if 'raw' in Conf[item].keys() and Conf[item]['raw'] and ('module' in Conf['raw'].keys()):
            Conf[item]['module'].Conf['raw'] = Conf['raw']['module']
            RawSenses.append(item)
        else: Conf[item]['module'].Conf['raw'] = None
    if len(RawSenses):  # initialize RAW module config
        Conf['raw']['database'] = "%s_%s" % (Conf['id']['project'],Conf['id']['serial'])
        for Nme in Conf['raw']:
            if (Nme != 'module') and (Nme != 'import'):
                Conf['raw']['module'].Conf[Nme] = Conf['raw'][Nme]
        MyLogger.log(modulename,'INFO',"Raw measurements for %s on db %s is ENABLED." % (', '.join(RawSenses),Conf['raw']['database']))

# ===============================================================
# Main program
# ===============================================================
# initialise

get_config()
process = integrate_options()
MyLogger.Conf.update(Conf['logging'])
LoadWrapup('inputs')
LoadWrapup('outputs')
ConfRawModule(INPUTS)

################# ================================================ ##############
#                     start running                                ##############
################# ================================================ ##############
if ('start_dir' in Conf['process'].keys()) and Conf['process']['start_dir']:
    try:
        os.chdir(Conf['process']['start_dir'])
    except:
        MyLogger.log(modulename,'FATAL',"Could not change directory to %s." % Conf['process']['start_dir'])

if process == 'interactive':  ## interactive mode ===========
    print("Stop this process NOT via <cntrl>c, but via <cntrl>z and kill %1")
    show_startup()
    FreeConfMem('input','output')
    del INPUTS; del INPUTS_I ; del OUTPUTS; del OUTPUTS_I
    sensorread()                   # ============================= RUN
else:                              ## service mode     ===========
    import atexit
    from os import geteuid, getegid
    from signal import SIGTERM
    import fcntl
    try:
        if ('uid' in Conf['process'].keys()) and (Conf['process']['uid']):
            setuid(Conf['process']['uid'])
        if ('gid' in Conf['process'].keys()) and (Conf['process']['gid']):
            setgid(Conf['process']['gid'])
    except:
        MyLogger.log(modulename,'ERROR',"Cannot set process uid (%d) or gid (%d)." % (setuid(Conf['process']['uid'],etgid(Conf['process']['gid']))))
    if geteuid() == 0:
        MyLogger.log(modulename,'ERROR',"Process deamon is running under root permissions!")
    pidfile = Conf['process']['pid'] + progname + '.pid'
    os.chdir(Conf['process']['home'])    # current directory now is here
    if process == 'start':
        show_startup()
        FreeConfMem('input','output')
        del INPUTS; del INPUTS_I ; del OUTPUTS; del OUTPUTS_I
        Conf['console']['output'] = False
        deamon_detach(pidfile)
        WaitTime = 60   # wait time to restart sensorread

        for RunCnt in range(1,30):
            LastTime = time()
            try:
                sensorread()            # ======================== RUN
            except IOError, e:
                for name in Conf.keys():
                    if Conf[name].has_key('fd') and Conf[name,'id']:
                        try:
                            close(Conf[name,'fd'])
                        except:
                            pass
                        Conf[name,'fd'] = None
                MyLogger.log(modulename,'ERROR',"IO error %s, try to restart" % e)
            if (time() - LastTime) > 60:
                WaitTime = 60
            else:
                WaitTime *= 2
            if WaitTime > 60*60:
                WaitTime = 60*60
            sleep(WaitTime)
                    
    elif process == 'stop':
        deamon_stop(pidfile)
    elif process == 'status':
        deamon_status(pidfile)
    else:
        sys.exit("Unknown process request.")
exit(0)
