teusH/MySense/RPi/sds011.py

# -*- coding: utf-8 -*-
"""
Copyright 2016, Frank Heuer, Germany

This file is part of SDS011.

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
Diese Datei ist Teil von SDS011.

SDS011 ist Freie Software: Sie können es unter den Bedingungen
der GNU General Public License, wie von der Free Software Foundation,
Version 3 der Lizenz oder (nach Ihrer Wahl) jeder späteren
veröffentlichten Version, weiterverbreiten und/oder modifizieren.

SDS011 wird in der Hoffnung, dass es nützlich sein wird, aber
OHNE JEDE GEWÄHRLEISTUNG, bereitgestellt; sogar ohne die implizite
Gewährleistung der MARKTFÄHIGKEIT oder EIGNUNG FÜR EINEN BESTIMMTEN ZWECK.
Siehe die GNU General Public License für weitere Details.

Sie sollten eine Kopie der GNU General Public License zusammen mit SDS011
erhalten haben. Wenn nicht, siehe <http://www.gnu.org/licenses/>.
"""

"""
This module contains the SDS011 class for controlling
the sds011 particle matter sensor from Nova using the HL-340-serial TTL USB adapter
"""

# this module has been updated by Teus Hagen May 2017
# all errors introduced with this update come from teus

from enum import IntEnum
import time
import struct
import serial
import math
import signal

class SDS011(object):
    """Class representing the SD011 dust sensor and its methods.
        The device_path on Win is one of your COM ports,
        on Linux it is one of "/dev/ttyUSB..." or "/dev/ttyAMA..."
    """

    '''
    The serial communication uses special encoded bytes:
    each serial message starts with 0xAA and ends with 0xAB.
    The message sent to the sensor:
    the second byte is 0xB4, the 16th and 17th byte is 0xFF.
    In the response message from SDS011 the second byte is 0xC5.
    If it is a response sent automaticaly by the sensor in "Initiative" Report Mode,
    the second byte is 0xC0.
    The third byte is always the command byte,
    except in response to a request command or a sensor initiated response,
    the second byte is 0xC0.
    So a message to the sensor might look as, for
    Report Mode:
    ------------------------
    Setting to Initiative:
    Message  aa:b4:02:01:00:00:00:00:00:00:00:00:00:00:00:ff:ff:01:ab
    Response aa:c5:02:01:00:00:cc:0b:da:ab

    Setting to Passive:
    Message  aa:b4:02:01:01:00:00:00:00:00:00:00:00:00:00:ff:ff:02:ab
    Response aa:c5:02:01:01:00:cc:0b:db:ab

    '''

    __SerialStart = 0xAA
    __SerialEnd = 0xAB
    __SendByte = 0xB4
    __ResponseByte = 0xC5
    __ReceiveByte = 0xC0
    __ResponseLength = 10
    __CommandLength = 19
    __CommandTerminator = 0xFF

    class Command(IntEnum):
        """Enumeration of commands, the SDS011 can understand."""
        ReportMode = 2,
        Request = 4,
        DeviceId = 5,
        WorkState = 6,
        Firmware = 7,
        DutyCycle = 8

    class CommandMode(IntEnum):
        """One command can get the corrent configuration of the sensor or set it"""
        Getting = 0,
        Setting = 1

    class ReportModes(IntEnum):
        '''the Report modes the sensor can run in:
        In passive mode one has to send a request command,
        in order to get the measurement values as a response.'''
        Initiative = 0,
        Passiv = 1

    class WorkStates(IntEnum):
        '''the Work states, the sensor can have.
        In sleeping mode it does not send any data.
        To get data you have to wake it up'''
        Sleeping = 0,
        Measuring = 1
    # Constructor

    def __init__(self, device_path, **args):
        '''
        The device_path on Win is one of your COM ports.
        On Linux one of "/dev/ttyUSB..." or "/dev/ttyAMA..."
        '''
        def timeoutHdlr(signum,frame):
            signal.alarm(0)
            raise IOError("timeout on sds011 initialisation")

        self.logger = None
        if 'logger' in args.keys():             # log routine
            self.logger = args['logger']
        self.debug = 0
        if 'debug' in args.keys():              # debug level
            self.debug = int(args['debug'])
        self.timeout = 2
        if 'timeout' in args.keys():            # serial line read timeout
            self.timeout = int(args['timeout'])
        self.pcs = False
        if 'concentration' in args.keys():      # in mass or values in concentration
            self.pcs = args['concentration']
        if self.logger == None:
            print("WARNING: no logging for SDS011")
            self.debug = 0
        if self.debug:
            self.log("DEBUG","Start of the constructor with device_path {0}\n".format(device_path))
        self.__device_path = device_path
        self.device = None
        signal.signal(signal.SIGALRM, timeoutHdlr)
        tried = 0
        while True:
            if self.device != None:
                self.device.close()
                self.device = None
            try:
                self.device = serial.Serial(device_path,
                                    baudrate=9600, stopbits=serial.STOPBITS_ONE,
                                    parity=serial.PARITY_NONE,
                                    bytesize=serial.EIGHTBITS,
                                    timeout=2)
                if self.device.isOpen() is False:
                    if not self.device.open():
                        raise IOError("Unable to open USB to SDS011")
            except:
                raise IOError("SDS011: unable to set serial device %s" % device_path)

            # ToDo: initiate whith the values, the sensor has to be queried for that
            self.__firmware = None
            self.__reportmode = None
            self.__workstate = None
            self.__dutycycle = None
            self.__device_id = None
            self.__read_timeout = 0
            self.__dutycycle_start = time.time()
            self.__read_timeout_drift_percent = 2
            try:
                signal.alarm(self.timeout)
                # within response the __device_id will be set
                first_response = self.__response()
                if len(first_response) == 0:
                    # Device might be sleeping. So wake it up
                    self.log("WARNING","While constructing the instance "
                            "the sensor is not responding. "
                            "Maybe in sleeping in passive mode or in a "
                            "duty cycle? Will wake it up!")
                    self.__send(self.Command.WorkState,
                            self.__construct_data(self.CommandMode.Setting,
                                              self.WorkStates.Measuring))
                    self.__send(self.Command.DutyCycle, self.__construct_data(
                            self.CommandMode.Setting, 0))
                # at this point, device is awake, shure. So store this state
                self.__workstate = self.WorkStates.Measuring
                self.__get_current_config()
            except IOError:
                if tried > 3:
                    self.debugPrt(1,"Failed to initialize sds011 settings")
                    raise IOError("Initializing sds1011")
                self.debugPrt(1,"Timeout on initial sds011 settings")
                tried += 1
                continue
            signal.alarm(0)
            signal.signal(signal.SIGALRM, signal.SIG_IGN)
            self.device.timeout = self.timeout
            self.debugPrt(1,"Sensor has firmware %s" % self.__firmware)
            self.debugPrt(1,"Sensor is in reportmode %s" % self.__reportmode)
            self.debugPrt(1,"Sensor is in workstate %s" % self.__workstate)
            self.debugPrt(1,"Sensor is in dutycycle %s, None if Zero" % self.__dutycycle)
            self.debugPrt(1,"Sensor has Device ID: %s" % self.device_id)
            self.debugPrt(3,"The constructor is successfully executed.")
            break

    def log(self,level,string):
        if self.logger != None:
            self.logger('sds011 class',level,string)

    def debugPrt(self,level,string):
        if self.debug >= level and self.logger != None: self.logger('sds011 class','DEBUG',string)

    # conversion parameters come from:
    # http://ir.uiowa.edu/cgi/viewcontent.cgi?article=5915&context=etd
    def Mass2Con(self,pm,value):
        """Convert pm size from ug/m3 back to concentration pcs/0.01sqf"""
        if not self.pcs: return value
        pi = 3.14159
        density = 1.65 * pow (10, 12)
        radius = 0.44
        if pm == 'pm10': radius = 2.60
        radius *= pow(10,-6)
        volume = (4.0/3.0) * pi * pow(radius,3)
        mass = density * volume
        K = 3531.5
        concentration = value / (K * mass)
        return int(concentration+0.5)

    # Destructor
    def __del__(self):
        # it's better to clean up
        if self.device is not None: self.device.close()

    # ReportMode
    @property
    def device_path(self):
        """The device path of the sensor"""
        return self.__device_path

    # ReportMode
    @property
    def reportmode(self):
        """The report mode, the sensor has at the moment"""
        return self.__reportmode

    @reportmode.setter
    def reportmode(self, value):
        '''Setter for report mode. Use self.ReportMode IntEnum'''
        if (isinstance(value, self.ReportModes) or
                value is None):
            self.__send(self.Command.ReportMode, self.__construct_data(
                self.CommandMode.Setting, value))
            self.__reportmode = value
            self.debugPrt(1,"report mode setting: %s" % value)
        else:
            raise TypeError("report mode must be of type SDS011.ReportModes")

    # workstate
    @property
    def workstate(self):
        """The workstate of the sensor as a value of type self.WorkStates"""
        return self.__workstate

    @workstate.setter
    def workstate(self, value):
        if (isinstance(value, self.WorkStates) or
                value is None):
            self.__send(self.Command.WorkState, self.__construct_data(
                self.CommandMode.Setting, value))
            self.__workstate = value
            self.debugPrt(1,"workstate setted: %s" % value)
        else:
            raise TypeError("Report Mode must be of type SDS011.WorkStates")
    # dutycycle

    @property
    def dutycycle(self):
        """The duty cycle the sensor has as a value of type int"""
        return self.__dutycycle

    @dutycycle.setter
    def dutycycle(self, value):

        if (isinstance(value, int) or
                value is None):
            if value < 0 or value > 30:
                raise ValueError(
                    "Duty cycle has to be between 0 and 30 inclusive!")
            self.__send(self.Command.DutyCycle, self.__construct_data(
                self.CommandMode.Setting, value))
            self.__dutycycle = value
            # Calculate new timeout value
            self.__read_timeout = self.__calculate_read_timeout(value)
            self.__dutycycle_start = time.time()
            self.debugPrt(1,"New timeout for duty cycle = %s" % self.__read_timeout)
            self.debugPrt(1,"Duty cycle setted: %s" % value)
            self.__get_current_config()
        else:
            raise TypeError("Duty cycle must be of type SDS011.DutyCycles")

    @property
    def device_id(self):
        """The device id as a string"""
        return "{0:02x}{1:02x}".format(self.__device_id[0], self.__device_id[1]).upper()

    @property
    def firmware(self):
        """The firmware of the device"""
        return self.__firmware

    def __construct_data(self, cmdmode, cmdvalue):
        '''construct a data bytearray from cmdmode and cmdvalue.
        cmdvalue has to be self.CommandMode type and cmdvalue int
        returns bytearry of lenth 2'''
        if not isinstance(cmdmode, self.CommandMode):
            raise TypeError(
                "cmdmode must be of type {0}", type(self.CommandMode))
        if not isinstance(cmdvalue, int):
            raise TypeError("cmdvalue must be of type {0}", type(int))
        retval = bytearray()
        retval.append(cmdmode)
        retval.append(cmdvalue)
        self.debugPrt(3,"Data %s for command mode %s." % (cmdvalue, cmdmode))
        return retval

    def __get_current_config(self):
        '''Get's the senors status at construction time of this instance
        to reflect the real status of the physical sensor.'''
        # Getting the Dutycycle
        response = self.__send(self.Command.DutyCycle,
                               self.__construct_data(self.CommandMode.Getting, 0))
        if response is not None and len(response) > 0:

            dutycycle = response[1]
            self.__dutycycle = dutycycle
            self.__read_timeout = self.__calculate_read_timeout(dutycycle)
            self.__dutycycle_start = time.time()
        else:
            raise RuntimeError("SDS011 The duty cycle is not detectable")
        response = None

        # Getting reportmode
        response = self.__send(self.Command.ReportMode,
                               self.__construct_data(self.CommandMode.Getting, 0))
        if response is not None and len(response) > 0:
            reportmode = self.ReportModes(response[1])
            self.__reportmode = reportmode
        else:
            raise RuntimeError("SDS011 The report mode not detectable")
        response = None

        # Getting firmware
        response = self.__send(self.Command.Firmware,
                               self.__construct_data(self.CommandMode.Getting, 0))
        if response is not None and len(response) > 0:
            self.__firmware = "{0:02d}{1:02d}{2:02d}".format(
                response[0], response[1], response[2])
        else:
            raise RuntimeError("SDS011 The firmware is not detectable")
        response = None

    def __calculate_read_timeout(self, timeoutvalue):
        newtimeout = 60 * timeoutvalue + \
            self.__read_timeout_drift_percent / 100 * 60 * timeoutvalue
        self.debugPrt(2 ,"Read timeout calculated for %s: %s" % (timeoutvalue, newtimeout))
        return newtimeout

    def get_values(self):
        '''gets the sensor response and returns measured value of pm10 and pm25'''
        self.debugPrt(3,"get_values entered")
        if self.__workstate == self.WorkStates.Sleeping:
            raise RuntimeError("The SDS011 sensor is sleeping and will not " +
                                    "send any values. Wake it up first.")
        if self.__reportmode == self.ReportModes.Passiv:
            raise RuntimeError("The SDS011 sensor is in passive report mode "
                                     "and will not automaticly send values. "
                                     "You have to call Request() to get values.")

        self.__dutycycle_start = time.time()
        while self.dutycycle == 0 or \
                time.time() < self.__dutycycle_start + self.__read_timeout:
            response_data = self.__response()
            #self.debugPrt(3,
            #    "Received from sensor a response with values %s.", response_data)
            if len(response_data):
                self.debugPrt(1,"Received response from sensor %d bytes" % len(response_data))
            return self.__extract_values_from_response(response_data)
        raise IOError(
            "No data within read timeout of %d has been received" % self.__read_timeout)

    def request(self):
        """Request measurement data as a tuple from sensor when its in ReporMode.Passiv"""
        response = self.__send(self.Command.Request, bytearray())
        retval = self.__extract_values_from_response(response)
        return retval

    def __extract_values_from_response(self, response_data):
        """extracts the value of pm25 and pm10 from sensor response"""
        data = response_data[2:6]
        value_of_2point5micro = None
        value_of_10micro = None
        if len(data) == 4:
            value_of_2point5micro = self.Mass2Con('pm2.5',float(data[0] + data[1] * 256) / 10.0)
            value_of_10micro = self.Mass2Con('pm10',float(data[2] + data[3] * 256) / 10.0)
            self.debugPrt(4,"get_values is successfully executed.")
            if self.dutycycle != 0:
                self.__dutycycle_start = time.time()
            return (value_of_10micro, value_of_2point5micro)
        elif self.dutycycle == 0:
            raise ValueError("Data is missing")

    def __send(self, command, data):
        '''The method for sending commands to the sensor and returning the response'''
        #self.debugPrt(3,"send() entered with command %s and data %s." % (command.name, data))
        self.debugPrt(2,"send() command %s." % command.name)
        # Proof the input
        if not isinstance(command, self.Command):
            raise TypeError("The command must be of type SDS011.Command")
        if not isinstance(data, bytearray):
            raise TypeError("The data must be of type byte array")
        self.debugPrt(3,"Input parameter checked")
        # Initialise the commandarray
        bytes_to_send = bytearray()
        bytes_to_send.append(self.__SerialStart)
        bytes_to_send.append(self.__SendByte)
        bytes_to_send.append(command.value)
        # Add data and set zero to the remainder
        for i in range(0, 12):
            if i < len(data):
                bytes_to_send.append(data[i])
            else:
                bytes_to_send.append(0)
        # last two bytes before the checksum is the CommandTerminator
        bytes_to_send.append(self.__CommandTerminator)
        bytes_to_send.append(self.__CommandTerminator)
        # calculate the checksum
        checksum = self.__checksum_make(bytes_to_send)
        # append the checksum
        bytes_to_send.append(checksum % 256)
        # and append the terminator for serial sent
        bytes_to_send.append(self.__SerialEnd)

        #self.debugPrt(3,"Going to send: %s", ""join("%02x:" % b for b in bytes_to_send))
        # send the command
        written_bytes = self.device.write(bytes_to_send)
        self.device.flush()
        if written_bytes != len(bytes_to_send):
            raise IOError("Not all bytes written")
        #self.debugPrt(3,"Sended and flushed: %s" % bytes_to_send)
        if len(bytes_to_send) != 19:
            self.debugPrt(1,"Sended and flushed: %d bytes, expected 19" % len(bytes_to_send))
        # check the receive value
        received = self.__response(command)
        if len(received) != 10:
            self.debugPrt(1,"Received: %d bytes, expected 10" % len(received))
        if len(received) == 0:
            raise IOError("SDS011 sensor is not responding")
        # when no command or command is request command,
        # second byte has to be ReceiveByte
        if ((command is None or command == self.Command.Request) and
                received[1] != self.__ReceiveByte):
            raise ValueError(
                "expected to receive value {0:#X} for value request \
                or polling not found. Actual data:{1}".format(self.__ReceiveByte, received[1]))
        # check, if response is response of the command, except Command.Request
        if command is not self.Command.Request:
            if received[2] != command.value:
                raise ValueError(
                    "The expected receive value for value command not found")
            else:
                returnvalue = received[3: -2]
        else:
            returnvalue = received
        # return just the received data. Further evaluation of data outsite
        # this  function
        self.debugPrt(2,"Leaving send() normal and returning %s" % received[3: -2])
        return returnvalue

    def __response(self, command=None):
        '''get and check the response from the sensor. Response can be
        the response of a command sent or just the measurement data while sensor
        is in reportmode Initiative'''
        # receive the response while listening serial input
        bytes_received = bytearray(1)
        data = bytes(0)
        while True:
            data = self.device.read(1)
            '''if no bytes are read the sensor might be in sleep mode.
            It makes no sense to raise an exception here. The raise condition
            should be checked in a context outside of this fuction'''
            if len(data) > 0:
                bytes_received[0] = ord(data)
                # if this is true, serial data is coming in
                if bytes_received[0] == self.__SerialStart:
                    single_byte = self.device.read(1)
                    if (((command is not None and command != self.Command.Request)
                         and ord(single_byte) == self.__ResponseByte) or
                            ((command is None or command is self.Command.Request)
                             and ord(single_byte) == self.__ReceiveByte)):
                        bytes_received.append(ord(single_byte))
                        break
            else:
                if self.__dutycycle == 0:
                    self.log('sds011 class',"ERROR","A sensor response has not arrived within timeout limit. "
                                  "If the sensor is in sleeping mode wake it up first!"
                                  " Returning an empty byte array as response!")
                else:
                    self.debugPrt(1,"No response as expected while in dutycycle")
                return bytearray()

        data = self.device.read(8)
        if len(data) != 8:
            raise IOError("Read response timeout")
        thebytes = struct.unpack('BBBBBBBB', data)
        bytes_received.extend(thebytes)
        if command is not None and command is not self.Command.Request:
            if bytes_received[1] is not self.__ResponseByte:
                raise IOError("ResponseByte not found in response")
            if bytes_received[2] != command.value:
                raise IOError(
                    "Third byte of serial data {0} received is not a response \
                    to prior sent command {1}".format(bytes_received[2], command.name))
        if command is None or command is self.Command.Request:
            if bytes_received[1] is not self.__ReceiveByte:
                raise IOError("Received byte not found for Value Request")
        # proof checksum
        if self.__checksum_make(bytes_received[0:-2]) != bytes_received[-2]:
            raise IOError("Checksum of received data not valid")
        # set device_id if device Id is None, proof it, if it's not None
        if self.__device_id is None:
            self.__device_id = bytes_received[-4:-2]
        elif self.__device_id is not None and not self.__device_id.__eq__(bytes_received[-4:-2]):
            raise ValueError("Data received (%s) does not belong "
                             "to this device with id %s.",
                             bytes_received, bytes_received[-4:-2], self.__device_id)
        self.debugPrt(2,"The response() was successful")
        return bytes_received

    def reset(self):
        '''
        Sets report mode to Initiative, workstate to Measuring and duty cyle to 0
        '''
        self.workstate = self.WorkStates.Measuring
        self.reportmode = self.ReportModes.Initiative
        self.dutycycle = 0

    def __checksum_make(self, data):
        '''
        Generates the checksum for data to be sent or received from the sensor.
        The data has to be of type byte array and must start with 0xAA,
        followed by 0xB4 or 0xC5 or 0xC0 as second byte. The sequence must end before
        the position of the checksum.
        '''
        self.debugPrt(4,"Building the checksum for data %s." % data)
        # Build checksum for data to send or receive
        if len(data) not in (self.__CommandLength - 2, self.__ResponseLength - 2):
            raise ValueError("The data has to be {0} or {1} long".format(
                self.__CommandLength - 2, self.__ResponseLength))
        if data[0] != self.__SerialStart:
            raise ValueError("Data is missing the Startbit")
        if data[1] not in (self.__SendByte, self.__ResponseByte, self.__ReceiveByte):
            raise ValueError(
                "Data is missing SendBit-, ReceiveBit- or ReceiveValue-Byte")
        if data[1] != self.__ReceiveByte and data[2] not in list(map(int, self.Command)):
            raise ValueError(
                "The data command byte value {0} is not valid".format(data[2]))
        #checksum = command.value + bytes_to_send[15] + bytes_to_send[16]
        checksum = 0
        for i in range(2, len(data)):
            checksum = checksum + data[i]
        checksum = checksum % 256
        self.debugPrt(4,"The calculated checksum: %s." % checksum)
        return checksum
