teusH/MySense/RPi/MyInternet.py

#!/usr/bin/env python3
# -*- coding: utf-8 -*-
# Contact Teus Hagen webmaster@behouddeparel.nl to report improvements and bugs
# 
# Copyright (C) 2017, Behoud de Parel, Teus Hagen, the Netherlands
#
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

# $Id: MyInternet.py,v 2.6 2018/09/14 16:48:35 teus Exp teus $

# TO DO:

""" Maintain internet connection and info about the ip and rssi values
"""
modulename='$RCSfile: MyInternet.py,v $'[10:-4]
__version__ = "0." + "$Revision: 2.6 $"[11:-2]

# configurable options
__options__ = []

Conf = {
    # 'connected': defined?,  # if key defined and is there internet?
    # 'last':     None,   # last time checked to throddle connection info
}

try:
    import MyLogger
    import re
    import subprocess
    from time import time
    from random import shuffle
    import socket
    try:
        import urllib2 as urlreq
        from urllib2 import URLError
    except ImportError:
        import urllib.request as urlreq
        from urllib.error import URLError
except ImportError as e:
    MyLogger.log(modulename,'FATAL',"Unable to load module %s" % e)

# see if there is an internet connection.
# on wifi provide rssi strength
# return None on no internet, rssi strength 0 on no wifi otherwise rssi strength
def internet(ident):
    global Conf
    def get_internal_ip(ident):
        global Conf
        if 'connected' in Conf.keys():
            if Conf['connected'] != None:
                return Conf['connected']
        Conf = { 'connected': False, 'intern_ip': [], 'extern_ip': None }
        try:
            p=subprocess.Popen('/sbin/ifconfig',shell=True,stdout=subprocess.PIPE)
            stdout, stderr = p.communicate()
            ips = re.findall('inet6* (addr:)*\s*([0-9a-f]+([\.:][0-9a-f]+)+)', stdout)
            for item in ips:
                # TO DO: may need to exclude wifi AP ip addresses
                if (item[0][0:4] != '127.') and (item[0][0:5] != 'fe80:'):
                    Conf['intern_ip'].append(item[0])
            if len(Conf['intern_ip']):
                ident['intern_ip'] = Conf['intern_ip']
                Conf['connected'] = True
        except:
            Conf['connected'] = False
        return Conf['connected']
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
